alexliesenfeld/dgx-spark-printables/spark-atom/shop-img/ChatGPT Image Aug 3, 2026 at 11_18_05 PM.png

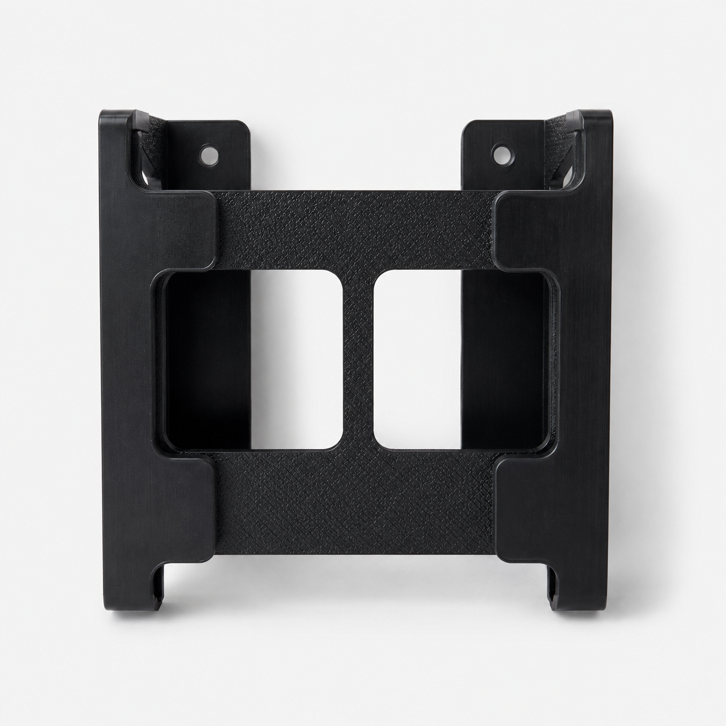
spark-atom/shop-img/ChatGPT Image Aug 3, 2026 at 11_18_05 PM.png
