alexliesenfeld/dgx-spark-printables/spark-atom/shop-img/ChatGPT Image Aug 3, 2026 at 11_45_13 PM.png

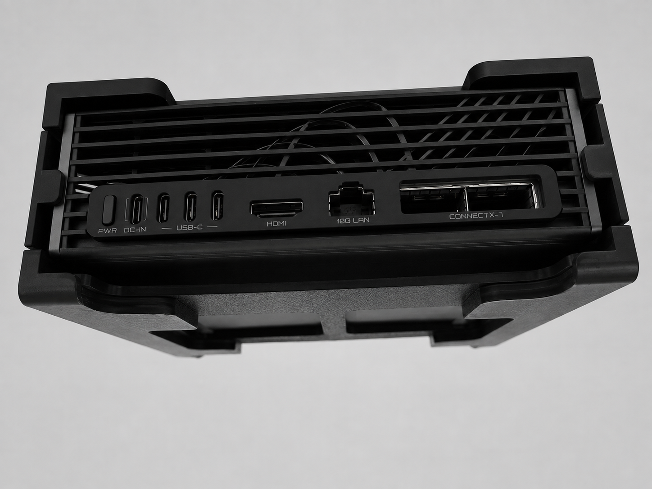
spark-atom/shop-img/ChatGPT Image Aug 3, 2026 at 11_45_13 PM.png
