alexliesenfeld/dgx-spark-printables/spark-atom/shop-img/IMG_5974.JPG

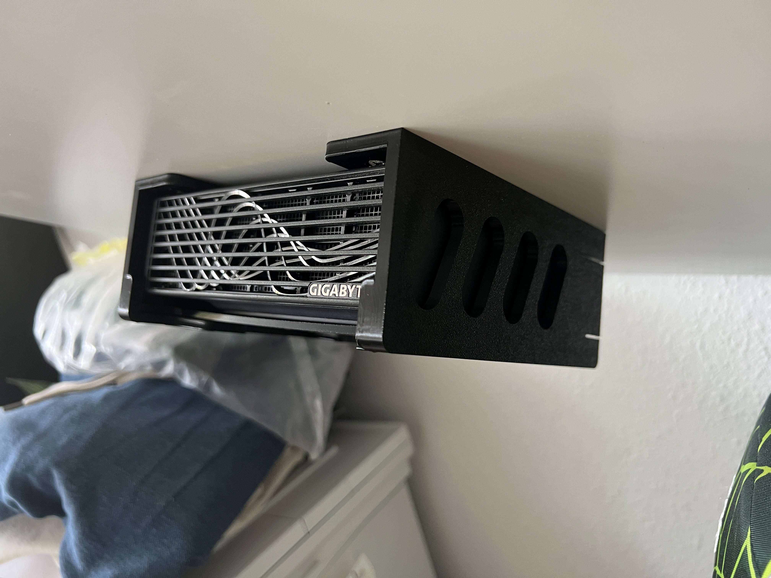
spark-atom/shop-img/IMG_5974.JPG
