alexliesenfeld/dgx-spark-printables/spark-atom/shop-img/IMG_5975.JPG

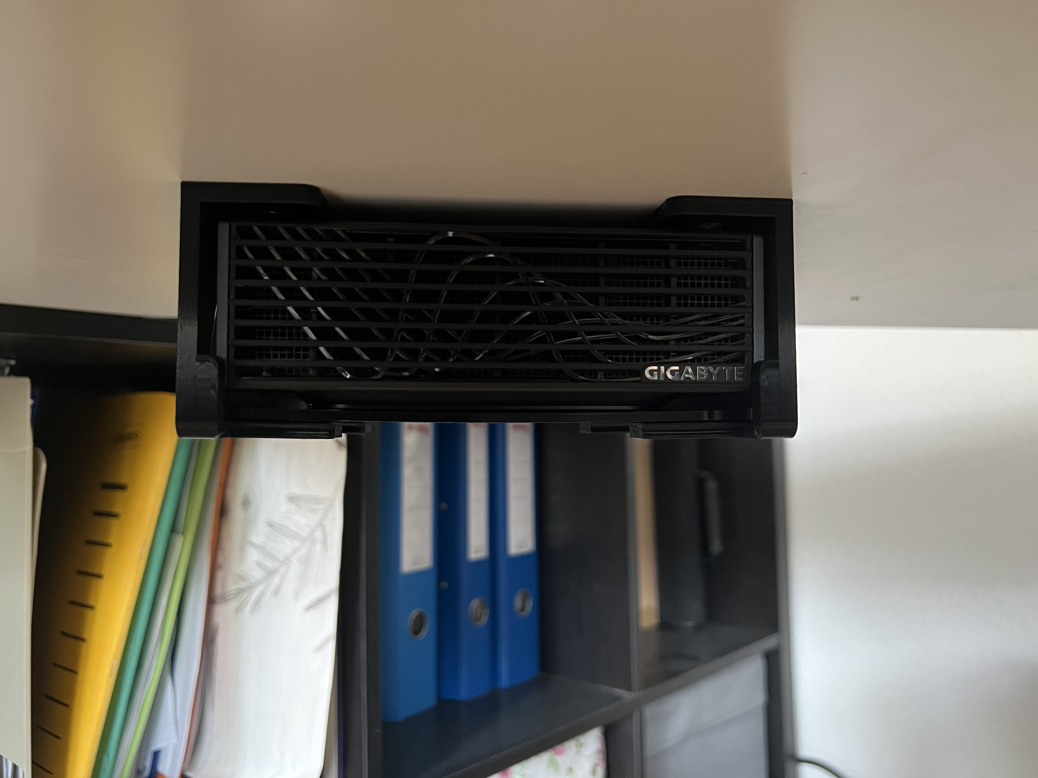
spark-atom/shop-img/IMG_5975.JPG
