alexliesenfeld/dgx-spark-printables/spark-atom/shop-img/IMG_5976.JPG

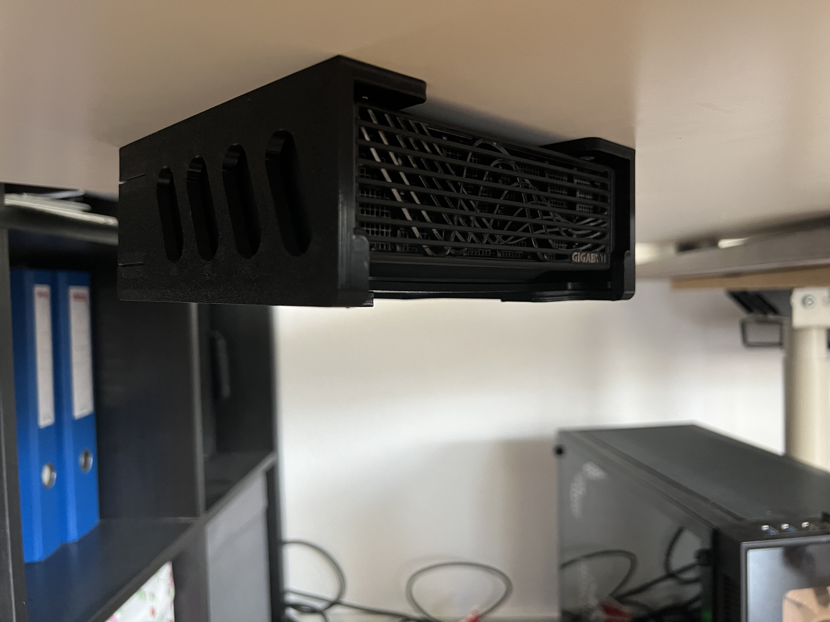
spark-atom/shop-img/IMG_5976.JPG
