alexliesenfeld/dgx-spark-printables/spark-atom/shop-img/IMG_5977.JPG

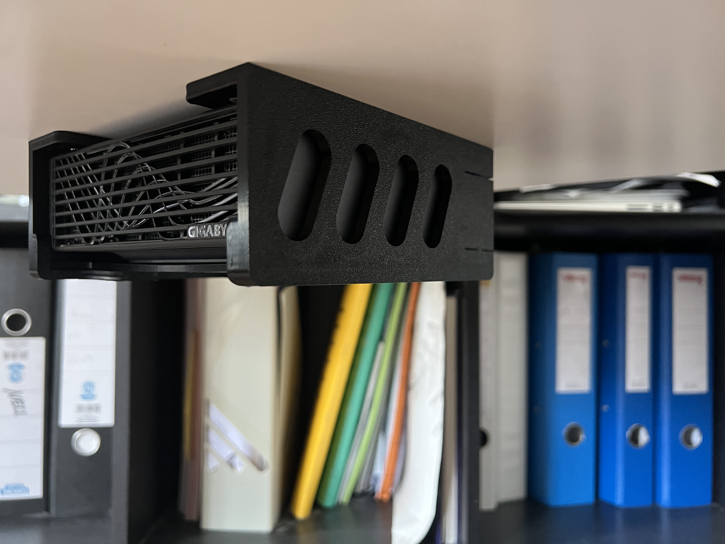
spark-atom/shop-img/IMG_5977.JPG
