alexliesenfeld/dgx-spark-printables/spark-atom/shop-img/openart-download/openart-sample_1785825434368_0cd59f5f.png

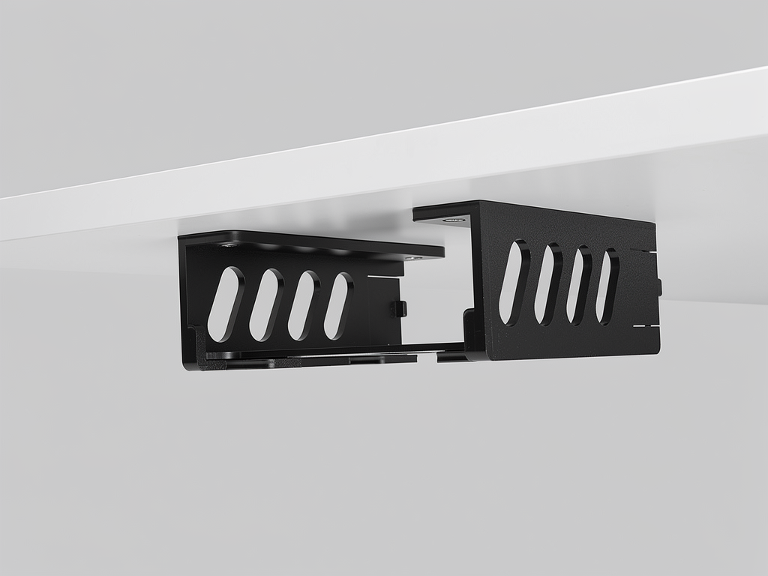
spark-atom/shop-img/openart-download/openart-sample_1785825434368_0cd59f5f.png
