alexliesenfeld/dgx-spark-printables/spark-atom/shop-img/openart-download/openart-sample_1785825800298_190668a8.png

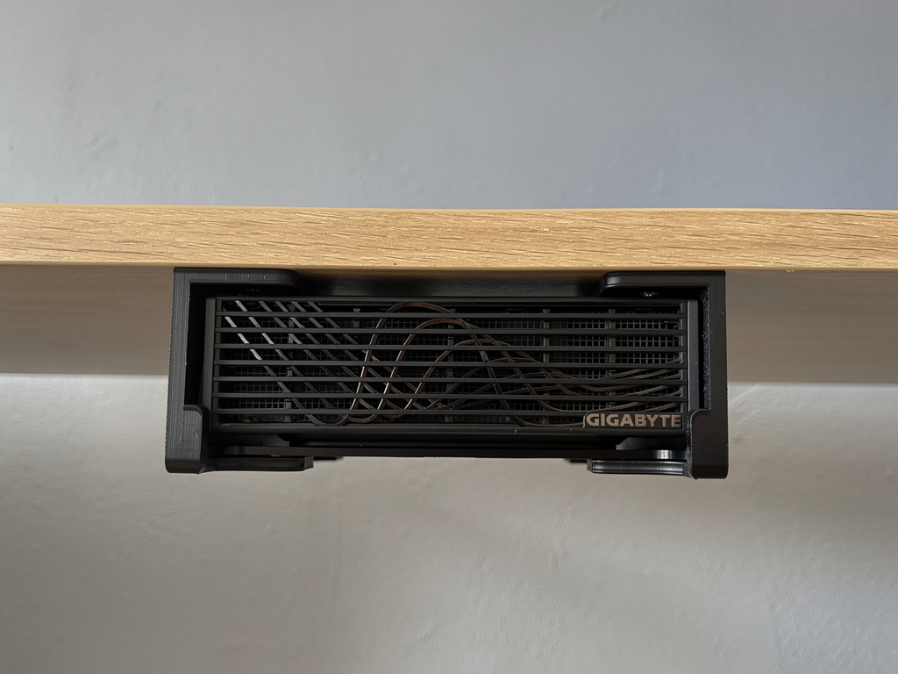
spark-atom/shop-img/openart-download/openart-sample_1785825800298_190668a8.png
