alexliesenfeld/dgx-spark-printables/spark-atom/shop-img/openart-sample_1785825800171_0b8fc502.png

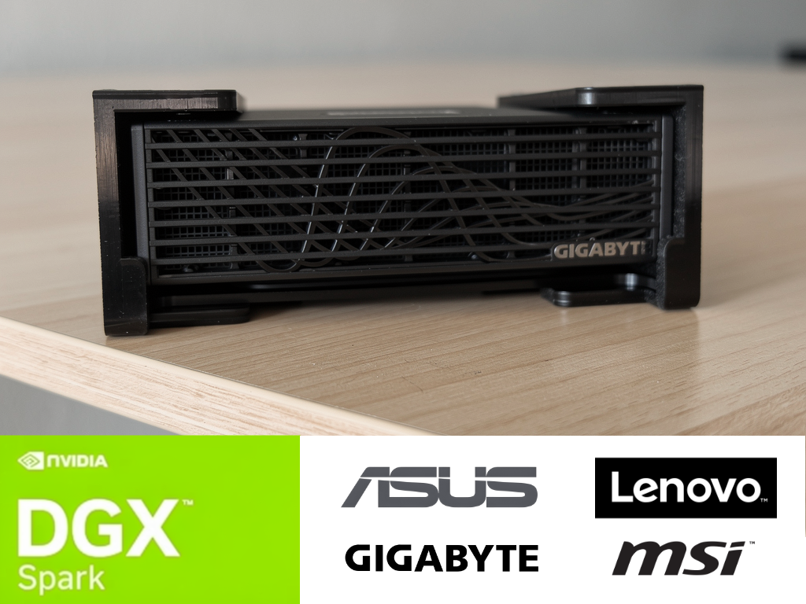
spark-atom/shop-img/openart-sample_1785825800171_0b8fc502.png
