alexliesenfeld/dgx-spark-printables/spark-atom/shop-img/untitled folder/IMG_5968.JPG

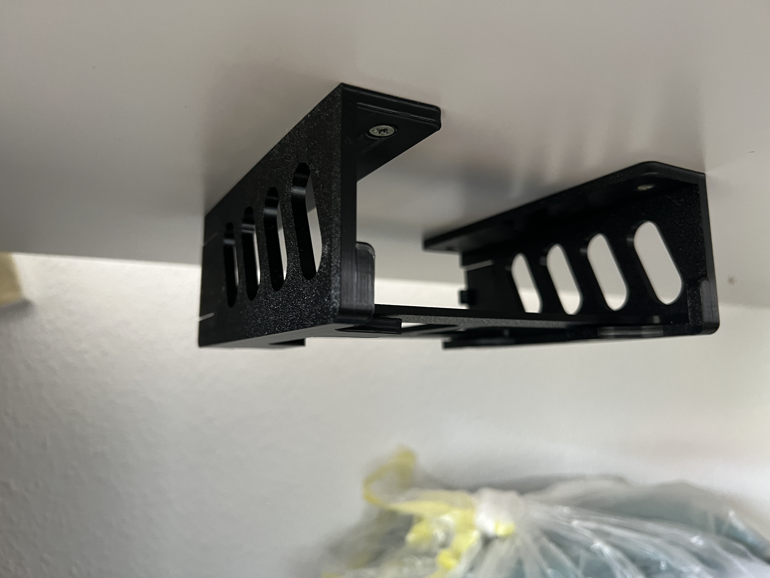
spark-atom/shop-img/untitled folder/IMG_5968.JPG
