alexliesenfeld/dgx-spark-printables/spark-atom/shop-img/untitled folder/IMG_5969.JPG

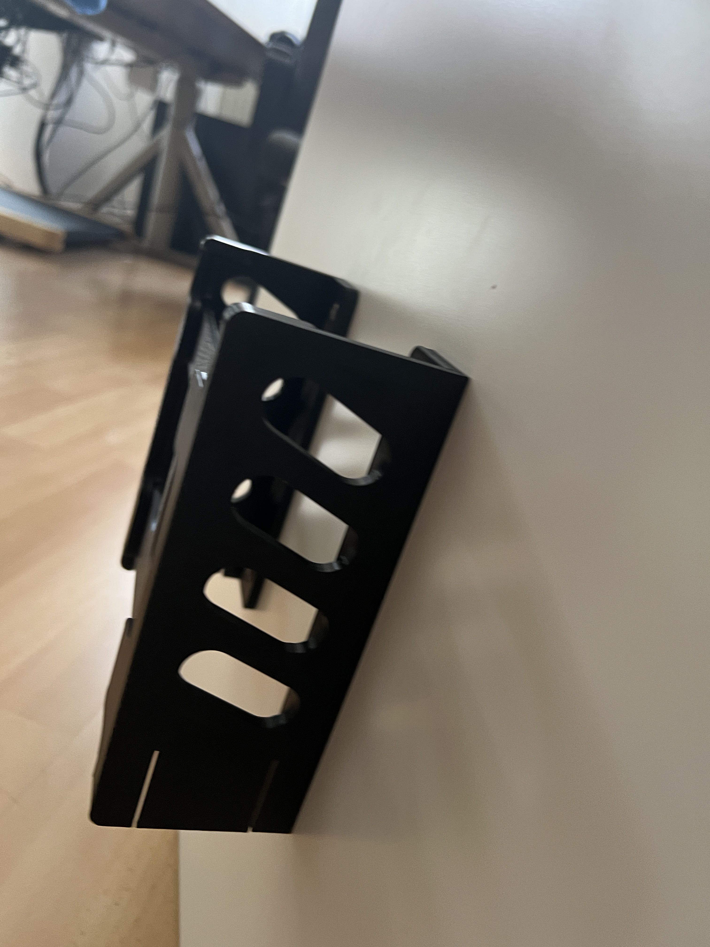
spark-atom/shop-img/untitled folder/IMG_5969.JPG
