alexliesenfeld/dgx-spark-printables/spark-atom/shop-img/untitled folder/IMG_5972.JPG

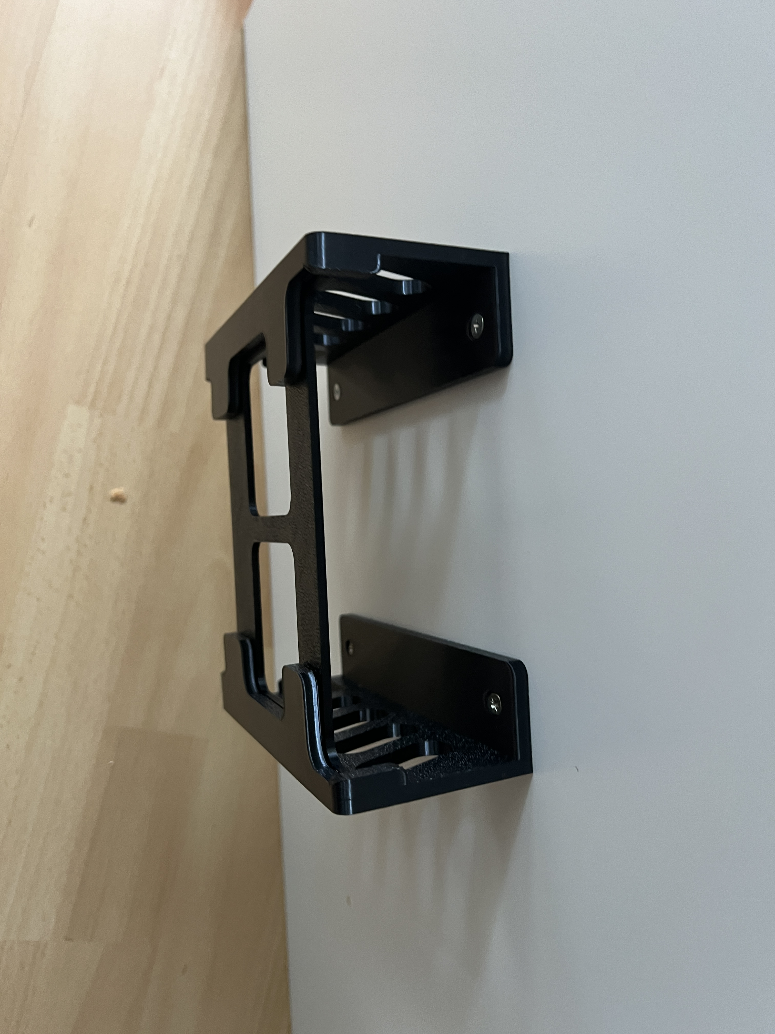
spark-atom/shop-img/untitled folder/IMG_5972.JPG
