alexliesenfeld/dgx-spark-printables/spark-rack-10/dgx_spark_rack_mount_demo.scad

/*
 * Demo view: rack mount with the 150 x 150 x 50.5 mm DGX Spark mockup and
 * two rear-mounted 80 x 80 x 25 mm fan mockups installed.
 *
 * This file is for visualization only. Export the printable assembly or its
 * individual parts from dgx_spark_rack_mount.scad instead.
 */

part_override = "demo";
include <dgx_spark_rack_mount.scad>
