alexliesenfeld/dgx-spark-printables/spark-atom/images/acer-bottom-projection.scad

/*
 * Demo-only pixel projection generated from acer.jpg.
 * Rows are stored top-to-bottom; the module flips them so the photograph's
 * bottom edge maps to Y=0, the physical front of the device.
 * Adjacent equal-shade pixels are merged into rectangles for faster previews.
 */

acer_projection_size = 160;
acer_projection_rectangles = [
    [0, 0, 1, 2, 51],
    [0, 1, 154, 1, 34],
    [0, 155, 1, 1, 51],
    [0, 156, 4, 2, 34],
    [1, 1, 2, 1, 34],
    [1, 3, 11, 1, 51],
    [1, 14, 36, 1, 34],
    [1, 50, 15, 1, 17],
    [1, 65, 3, 1, 34],
    [1, 68, 2, 1, 17],
    [1, 70, 2, 1, 34],
    [1, 72, 1, 1, 17],
    [1, 73, 1, 1, 34],
    [1, 74, 5, 1, 17],
    [1, 79, 2, 1, 34],
    [1, 81, 75, 1, 17],
    [2, 0, 3, 2, 34],
    [2, 3, 17, 1, 51],
    [2, 20, 80, 1, 34],
    [2, 100, 3, 1, 17],
    [2, 103, 1, 1, 34],
    [2, 104, 15, 1, 17],
    [2, 119, 2, 1, 34],
    [2, 121, 1, 1, 17],
    [2, 122, 1, 1, 34],
    [2, 123, 1, 1, 17],
    [2, 124, 5, 1, 34],
    [2, 129, 3, 1, 17],
    [2, 132, 2, 1, 34],
    [2, 134, 4, 1, 17],
    [2, 138, 22, 1, 34],
    [3, 3, 19, 1, 51],
    [3, 22, 1, 1, 34],
    [3, 23, 13, 1, 51],
    [3, 36, 1, 1, 34],
    [3, 37, 3, 1, 51],
    [3, 40, 62, 1, 34],
    [3, 102, 1, 1, 17],
    [3, 103, 3, 1, 34],
    [3, 106, 1, 1, 17],
    [3, 107, 2, 1, 34],
    [3, 109, 5, 1, 17],
    [3, 114, 1, 1, 34],
    [3, 115, 2, 1, 17],
    [3, 117, 43, 1, 34],
    [4, 0, 4, 1, 34],
    [4, 4, 13, 1, 51],
    [4, 17, 1, 1, 34],
    [4, 18, 1, 1, 51],
    [4, 19, 2, 1, 34],
    [4, 21, 1, 1, 51],
    [4, 22, 138, 1, 34],
    [5, 0, 160, 3, 34],
    [8, 0, 3, 2, 34],
    [8, 3, 2, 1, 51],
    [8, 5, 10, 1, 34],
    [8, 15, 1, 1, 17],
    [8, 16, 9, 1, 34],
    [8, 25, 1, 1, 17],
    [8, 26, 1, 1, 34],
    [8, 27, 118, 1, 17],
    [8, 145, 15, 1, 34],
    [9, 3, 1, 1, 51],
    [9, 4, 24, 1, 34],
    [9, 28, 1, 1, 17],
    [9, 29, 6, 1, 34],
    [9, 35, 121, 1, 17],
    [9, 156, 4, 88, 34],
    [10, 0, 2, 2, 34],
    [10, 2, 1, 2, 51],
    [10, 3, 26, 1, 34],
    [10, 29, 1, 1, 17],
    [10, 30, 3, 1, 34],
    [10, 33, 4, 1, 17],
    [10, 37, 2, 1, 34],
    [10, 39, 2, 1, 17],
    [10, 41, 1, 1, 34],
    [10, 42, 1, 1, 17],
    [10, 43, 1, 1, 34],
    [10, 44, 106, 1, 17],
    [10, 150, 1, 1, 34],
    [10, 151, 1, 1, 17],
    [10, 152, 1, 1, 34],
    [10, 153, 1, 1, 17],
    [10, 154, 1, 1, 34],
    [10, 155, 1, 1, 17],
    [11, 3, 28, 1, 34],
    [11, 31, 1, 1, 17],
    [11, 32, 7, 1, 34],
    [11, 39, 1, 1, 17],
    [11, 40, 3, 1, 34],
    [11, 43, 1, 1, 17],
    [11, 44, 1, 1, 34],
    [11, 45, 2, 1, 17],
    [11, 47, 1, 1, 34],
    [11, 48, 7, 1, 17],
    [11, 55, 1, 1, 34],
    [11, 56, 96, 1, 17],
    [11, 152, 2, 1, 34],
    [11, 154, 2, 1, 17],
    [12, 0, 50, 2, 34],
    [12, 50, 1, 2, 17],
    [12, 51, 2, 1, 34],
    [12, 53, 98, 1, 17],
    [12, 151, 1, 1, 34],
    [12, 152, 1, 1, 17],
    [12, 153, 2, 2, 34],
    [12, 155, 1, 3, 17],
    [13, 51, 3, 1, 34],
    [13, 54, 1, 1, 17],
    [13, 55, 4, 1, 34],
    [13, 59, 2, 1, 17],
    [13, 61, 2, 1, 34],
    [13, 63, 4, 1, 17],
    [13, 67, 1, 1, 34],
    [13, 68, 82, 1, 17],
    [13, 150, 1, 1, 34],
    [13, 151, 2, 1, 17],
    [14, 0, 2, 10, 34],
    [14, 2, 1, 7, 51],
    [14, 3, 64, 1, 34],
    [14, 67, 3, 1, 17],
    [14, 70, 2, 1, 34],
    [14, 72, 1, 1, 17],
    [14, 73, 1, 1, 34],
    [14, 74, 78, 1, 17],
    [14, 152, 1, 1, 34],
    [14, 153, 1, 1, 17],
    [14, 154, 1, 1, 34],
    [15, 3, 73, 1, 34],
    [15, 76, 1, 1, 17],
    [15, 77, 1, 1, 34],
    [15, 78, 1, 1, 17],
    [15, 79, 4, 1, 34],
    [15, 83, 1, 1, 17],
    [15, 84, 2, 1, 34],
    [15, 86, 18, 1, 17],
    [15, 104, 1, 1, 34],
    [15, 105, 51, 1, 17],
    [16, 3, 87, 1, 34],
    [16, 90, 2, 1, 17],
    [16, 92, 5, 1, 34],
    [16, 97, 1, 1, 17],
    [16, 98, 11, 1, 34],
    [16, 109, 1, 1, 17],
    [16, 110, 3, 1, 34],
    [16, 113, 1, 1, 17],
    [16, 114, 1, 1, 34],
    [16, 115, 12, 1, 17],
    [16, 127, 5, 1, 34],
    [16, 132, 1, 1, 17],
    [16, 133, 1, 1, 34],
    [16, 134, 1, 1, 17],
    [16, 135, 2, 1, 34],
    [16, 137, 19, 1, 17],
    [17, 3, 111, 1, 34],
    [17, 114, 1, 1, 17],
    [17, 115, 25, 1, 34],
    [17, 140, 13, 1, 17],
    [17, 153, 1, 1, 34],
    [17, 154, 2, 1, 17],
    [18, 3, 20, 1, 34],
    [18, 23, 9, 1, 51],
    [18, 32, 109, 1, 34],
    [18, 141, 1, 1, 17],
    [18, 142, 2, 1, 34],
    [18, 144, 12, 2, 17],
    [19, 3, 18, 1, 34],
    [19, 21, 11, 1, 51],
    [19, 32, 98, 1, 34],
    [19, 130, 5, 1, 51],
    [19, 135, 1, 1, 34],
    [19, 136, 1, 1, 51],
    [19, 137, 7, 1, 34],
    [20, 3, 16, 1, 34],
    [20, 19, 3, 1, 51],
    [20, 22, 6, 1, 68],
    [20, 28, 3, 1, 51],
    [20, 31, 65, 1, 34],
    [20, 96, 1, 1, 17],
    [20, 97, 3, 1, 34],
    [20, 100, 1, 2, 17],
    [20, 101, 12, 1, 34],
    [20, 113, 2, 1, 17],
    [20, 115, 1, 1, 34],
    [20, 116, 5, 1, 17],
    [20, 121, 9, 1, 34],
    [20, 130, 2, 1, 51],
    [20, 132, 3, 2, 68],
    [20, 135, 4, 1, 51],
    [20, 139, 6, 1, 34],
    [20, 145, 1, 1, 17],
    [20, 146, 1, 1, 34],
    [20, 147, 9, 1, 17],
    [21, 2, 2, 3, 51],
    [21, 4, 14, 1, 34],
    [21, 18, 2, 1, 51],
    [21, 20, 2, 1, 68],
    [21, 22, 2, 1, 85],
    [21, 24, 3, 1, 68],
    [21, 27, 2, 1, 51],
    [21, 29, 64, 1, 34],
    [21, 93, 1, 1, 17],
    [21, 94, 6, 1, 34],
    [21, 101, 9, 1, 34],
    [21, 110, 1, 1, 17],
    [21, 111, 5, 1, 34],
    [21, 116, 1, 1, 17],
    [21, 117, 2, 1, 34],
    [21, 119, 4, 1, 17],
    [21, 123, 8, 1, 34],
    [21, 131, 1, 1, 51],
    [21, 135, 1, 1, 85],
    [21, 136, 3, 1, 68],
    [21, 139, 1, 1, 51],
    [21, 140, 6, 1, 34],
    [21, 146, 3, 1, 17],
    [21, 149, 1, 2, 34],
    [21, 150, 6, 2, 17],
    [22, 4, 12, 1, 34],
    [22, 16, 3, 1, 51],
    [22, 19, 1, 1, 68],
    [22, 20, 4, 1, 85],
    [22, 24, 2, 1, 68],
    [22, 26, 2, 1, 51],
    [22, 28, 103, 1, 34],
    [22, 131, 2, 1, 51],
    [22, 133, 1, 1, 68],
    [22, 134, 5, 1, 85],
    [22, 139, 1, 1, 68],
    [22, 140, 2, 1, 51],
    [22, 142, 6, 1, 34],
    [22, 148, 1, 1, 17],
    [23, 4, 11, 1, 34],
    [23, 15, 2, 1, 51],
    [23, 17, 2, 1, 68],
    [23, 19, 4, 1, 85],
    [23, 23, 1, 1, 68],
    [23, 24, 2, 1, 51],
    [23, 26, 106, 1, 34],
    [23, 132, 1, 1, 51],
    [23, 133, 2, 1, 68],
    [23, 135, 1, 2, 85],
    [23, 136, 3, 1, 102],
    [23, 139, 2, 1, 85],
    [23, 141, 1, 1, 68],
    [23, 142, 1, 1, 51],
    [23, 143, 8, 1, 34],
    [23, 151, 5, 1, 17],
    [24, 0, 15, 1, 34],
    [24, 15, 1, 1, 51],
    [24, 16, 1, 1, 68],
    [24, 17, 2, 1, 85],
    [24, 19, 2, 1, 102],
    [24, 21, 1, 1, 85],
    [24, 22, 1, 2, 68],
    [24, 23, 2, 1, 51],
    [24, 25, 7, 1, 34],
    [24, 32, 97, 1, 17],
    [24, 129, 2, 1, 34],
    [24, 131, 3, 1, 51],
    [24, 134, 1, 1, 68],
    [24, 136, 5, 1, 102],
    [24, 141, 1, 1, 85],
    [24, 142, 1, 1, 68],
    [24, 143, 1, 1, 51],
    [24, 144, 5, 1, 34],
    [24, 149, 7, 1, 17],
    [25, 0, 14, 1, 34],
    [25, 14, 1, 1, 51],
    [25, 15, 1, 1, 68],
    [25, 16, 2, 1, 85],
    [25, 18, 2, 1, 102],
    [25, 20, 2, 1, 85],
    [25, 23, 1, 1, 51],
    [25, 24, 1, 1, 34],
    [25, 25, 2, 1, 51],
    [25, 27, 2, 1, 34],
    [25, 29, 1, 1, 17],
    [25, 30, 77, 1, 34],
    [25, 107, 1, 1, 17],
    [25, 108, 5, 1, 34],
    [25, 113, 1, 1, 17],
    [25, 114, 15, 1, 34],
    [25, 129, 2, 1, 17],
    [25, 131, 2, 1, 34],
    [25, 133, 1, 1, 68],
    [25, 134, 3, 1, 85],
    [25, 137, 2, 2, 102],
    [25, 139, 1, 1, 119],
    [25, 140, 2, 1, 102],
    [25, 142, 1, 1, 85],
    [25, 143, 1, 1, 68],
    [25, 144, 1, 2, 51],
    [25, 145, 5, 1, 34],
    [25, 150, 6, 1, 17],
    [26, 0, 2, 1, 34],
    [26, 2, 1, 1, 51],
    [26, 3, 10, 1, 34],
    [26, 13, 1, 2, 51],
    [26, 14, 2, 1, 68],
    [26, 16, 1, 1, 85],
    [26, 17, 3, 1, 102],
    [26, 20, 1, 1, 85],
    [26, 21, 1, 1, 68],
    [26, 22, 4, 1, 51],
    [26, 26, 4, 1, 34],
    [26, 30, 13, 1, 51],
    [26, 43, 2, 1, 34],
    [26, 45, 1, 1, 51],
    [26, 46, 1, 1, 34],
    [26, 47, 1, 1, 51],
    [26, 48, 85, 1, 34],
    [26, 133, 1, 1, 17],
    [26, 134, 1, 1, 51],
    [26, 135, 2, 1, 85],
    [26, 139, 3, 1, 119],
    [26, 142, 1, 1, 102],
    [26, 143, 1, 1, 85],
    [26, 145, 6, 1, 34],
    [26, 151, 5, 4, 17],
    [27, 0, 13, 1, 34],
    [27, 14, 1, 1, 68],
    [27, 15, 1, 1, 85],
    [27, 16, 3, 1, 102],
    [27, 19, 1, 1, 85],
    [27, 20, 1, 1, 68],
    [27, 21, 2, 1, 51],
    [27, 23, 1, 1, 68],
    [27, 24, 1, 1, 34],
    [27, 25, 1, 1, 17],
    [27, 26, 1, 1, 34],
    [27, 27, 9, 1, 51],
    [27, 36, 1, 1, 34],
    [27, 37, 4, 1, 51],
    [27, 41, 1, 1, 34],
    [27, 42, 1, 1, 51],
    [27, 43, 91, 1, 34],
    [27, 134, 1, 1, 17],
    [27, 135, 1, 1, 34],
    [27, 136, 3, 1, 102],
    [27, 139, 4, 1, 119],
    [27, 143, 1, 1, 102],
    [27, 144, 1, 1, 68],
    [27, 145, 1, 1, 51],
    [27, 146, 5, 1, 34],
    [28, 0, 2, 2, 34],
    [28, 2, 1, 2, 51],
    [28, 3, 9, 1, 34],
    [28, 12, 1, 1, 51],
    [28, 13, 1, 2, 68],
    [28, 14, 1, 2, 85],
    [28, 15, 3, 1, 102],
    [28, 18, 1, 2, 85],
    [28, 19, 1, 2, 68],
    [28, 20, 2, 1, 51],
    [28, 22, 1, 1, 68],
    [28, 23, 2, 1, 34],
    [28, 25, 18, 1, 51],
    [28, 43, 1, 1, 34],
    [28, 44, 1, 1, 51],
    [28, 45, 1, 1, 34],
    [28, 46, 1, 1, 51],
    [28, 47, 87, 1, 34],
    [28, 134, 1, 1, 51],
    [28, 135, 2, 1, 34],
    [28, 137, 2, 1, 102],
    [28, 139, 5, 1, 119],
    [28, 144, 1, 1, 85],
    [28, 145, 1, 1, 68],
    [28, 146, 1, 2, 51],
    [28, 147, 4, 2, 34],
    [29, 3, 8, 1, 34],
    [29, 11, 2, 1, 51],
    [29, 15, 1, 1, 102],
    [29, 16, 1, 1, 119],
    [29, 17, 1, 1, 102],
    [29, 20, 1, 1, 51],
    [29, 21, 1, 1, 68],
    [29, 22, 2, 1, 34],
    [29, 24, 24, 1, 51],
    [29, 48, 2, 1, 34],
    [29, 50, 3, 1, 51],
    [29, 53, 82, 1, 34],
    [29, 135, 1, 1, 51],
    [29, 136, 2, 1, 34],
    [29, 138, 1, 1, 119],
    [29, 139, 1, 1, 102],
    [29, 140, 4, 1, 119],
    [29, 144, 1, 1, 102],
    [29, 145, 1, 1, 85],
    [30, 0, 11, 2, 34],
    [30, 11, 1, 2, 51],
    [30, 12, 1, 2, 68],
    [30, 13, 1, 2, 85],
    [30, 14, 3, 1, 102],
    [30, 17, 1, 2, 85],
    [30, 18, 1, 1, 68],
    [30, 19, 1, 1, 51],
    [30, 20, 1, 2, 68],
    [30, 21, 1, 1, 51],
    [30, 22, 1, 1, 34],
    [30, 23, 1, 1, 51],
    [30, 24, 1, 1, 34],
    [30, 25, 15, 1, 51],
    [30, 40, 1, 1, 34],
    [30, 41, 4, 1, 51],
    [30, 45, 5, 1, 34],
    [30, 50, 2, 1, 51],
    [30, 52, 84, 1, 34],
    [30, 136, 1, 1, 51],
    [30, 137, 1, 1, 17],
    [30, 138, 1, 1, 68],
    [30, 139, 6, 1, 119],
    [30, 145, 1, 3, 102],
    [30, 146, 1, 1, 68],
    [30, 147, 1, 2, 51],
    [30, 148, 4, 3, 34],
    [30, 152, 4, 13, 17],
    [31, 14, 1, 1, 102],
    [31, 15, 1, 1, 119],
    [31, 16, 1, 1, 102],
    [31, 18, 2, 1, 51],
    [31, 21, 1, 2, 34],
    [31, 22, 21, 1, 51],
    [31, 43, 1, 1, 34],
    [31, 44, 1, 1, 51],
    [31, 45, 2, 1, 34],
    [31, 47, 2, 1, 51],
    [31, 49, 88, 1, 34],
    [31, 137, 1, 2, 51],
    [31, 138, 1, 1, 17],
    [31, 139, 1, 1, 102],
    [31, 140, 2, 1, 119],
    [31, 142, 1, 1, 136],
    [31, 143, 2, 1, 119],
    [31, 146, 1, 2, 85],
    [32, 0, 2, 2, 34],
    [32, 2, 1, 2, 51],
    [32, 3, 7, 2, 34],
    [32, 10, 2, 1, 51],
    [32, 12, 1, 4, 85],
    [32, 13, 3, 1, 102],
    [32, 16, 1, 2, 85],
    [32, 17, 1, 1, 68],
    [32, 18, 1, 1, 51],
    [32, 19, 1, 2, 68],
    [32, 20, 1, 1, 51],
    [32, 22, 30, 1, 51],
    [32, 52, 1, 1, 34],
    [32, 53, 1, 1, 51],
    [32, 54, 83, 1, 34],
    [32, 138, 1, 1, 34],
    [32, 139, 1, 1, 51],
    [32, 140, 3, 1, 119],
    [32, 143, 1, 2, 136],
    [32, 144, 1, 1, 119],
    [32, 147, 1, 3, 68],
    [33, 10, 1, 4, 51],
    [33, 11, 1, 4, 68],
    [33, 13, 1, 2, 102],
    [33, 14, 1, 2, 119],
    [33, 15, 1, 2, 102],
    [33, 17, 2, 1, 51],
    [33, 20, 1, 2, 34],
    [33, 21, 10, 1, 51],
    [33, 31, 107, 1, 34],
    [33, 138, 1, 3, 51],
    [33, 139, 1, 3, 34],
    [33, 140, 1, 1, 102],
    [33, 141, 2, 1, 119],
    [33, 144, 2, 1, 119],
    [33, 146, 1, 49, 102],
    [33, 148, 1, 6, 51],
    [33, 149, 3, 10, 34],
    [34, 0, 10, 3, 34],
    [34, 16, 1, 3, 68],
    [34, 17, 3, 1, 51],
    [34, 21, 8, 1, 51],
    [34, 29, 1, 1, 34],
    [34, 30, 1, 1, 17],
    [34, 31, 98, 1, 34],
    [34, 129, 1, 1, 17],
    [34, 130, 3, 1, 34],
    [34, 133, 2, 1, 51],
    [34, 135, 3, 1, 34],
    [34, 140, 1, 1, 85],
    [34, 141, 5, 3, 119],
    [35, 13, 3, 1, 102],
    [35, 17, 2, 1, 51],
    [35, 19, 2, 1, 34],
    [35, 21, 7, 1, 51],
    [35, 28, 1, 1, 34],
    [35, 29, 1, 1, 17],
    [35, 30, 100, 1, 51],
    [35, 130, 1, 1, 17],
    [35, 131, 1, 1, 34],
    [35, 132, 1, 2, 51],
    [35, 133, 5, 1, 34],
    [35, 140, 1, 1, 51],
    [35, 147, 1, 66, 85],
    [36, 12, 3, 32, 102],
    [36, 15, 1, 4, 85],
    [36, 17, 1, 14, 34],
    [36, 18, 1, 1, 68],
    [36, 19, 1, 10, 34],
    [36, 20, 7, 4, 51],
    [36, 27, 1, 4, 34],
    [36, 28, 1, 4, 17],
    [36, 29, 3, 1, 51],
    [36, 32, 96, 1, 34],
    [36, 128, 2, 1, 51],
    [36, 130, 1, 1, 34],
    [36, 131, 1, 4, 17],
    [36, 133, 8, 1, 34],
    [37, 0, 9, 4, 34],
    [37, 9, 2, 4, 51],
    [37, 11, 1, 16, 85],
    [37, 16, 1, 13, 51],
    [37, 18, 1, 29, 51],
    [37, 29, 2, 2, 51],
    [37, 31, 98, 2, 34],
    [37, 129, 2, 2, 51],
    [37, 132, 7, 1, 34],
    [37, 139, 1, 34, 51],
    [37, 140, 1, 1, 34],
    [37, 141, 1, 1, 102],
    [37, 142, 4, 1, 119],
    [38, 132, 2, 1, 34],
    [38, 134, 1, 1, 51],
    [38, 135, 4, 3, 34],
    [38, 140, 1, 85, 17],
    [38, 141, 2, 1, 102],
    [38, 143, 3, 22, 119],
    [39, 29, 100, 1, 34],
    [39, 129, 1, 1, 51],
    [39, 130, 1, 1, 34],
    [39, 132, 1, 1, 34],
    [39, 133, 2, 1, 51],
    [39, 141, 1, 18, 85],
    [39, 142, 1, 21, 102],
    [39, 148, 1, 6, 68],
    [40, 15, 1, 43, 68],
    [40, 20, 8, 2, 51],
    [40, 28, 1, 2, 34],
    [40, 29, 1, 1, 17],
    [40, 30, 100, 1, 34],
    [40, 130, 1, 1, 17],
    [40, 131, 3, 1, 34],
    [40, 134, 1, 1, 51],
    [41, 0, 10, 1, 34],
    [41, 10, 1, 1, 51],
    [41, 29, 2, 1, 17],
    [41, 31, 98, 1, 34],
    [41, 129, 2, 1, 17],
    [41, 131, 8, 1, 34],
    [42, 0, 4, 1, 34],
    [42, 4, 1, 1, 17],
    [42, 5, 4, 1, 34],
    [42, 9, 2, 1, 51],
    [42, 20, 10, 1, 51],
    [42, 30, 95, 1, 34],
    [42, 125, 4, 1, 17],
    [42, 129, 2, 1, 34],
    [42, 131, 1, 1, 51],
    [42, 132, 7, 1, 34],
    [43, 0, 10, 1, 34],
    [43, 10, 1, 1, 51],
    [43, 20, 42, 1, 51],
    [43, 62, 6, 1, 34],
    [43, 68, 2, 1, 51],
    [43, 70, 10, 1, 34],
    [43, 80, 1, 1, 51],
    [43, 81, 58, 1, 34],
    [43, 149, 2, 1, 34],
    [43, 151, 5, 1, 17],
    [44, 0, 9, 1, 34],
    [44, 9, 2, 1, 51],
    [44, 20, 31, 1, 51],
    [44, 51, 1, 1, 34],
    [44, 52, 11, 1, 51],
    [44, 63, 1, 1, 34],
    [44, 64, 2, 1, 51],
    [44, 66, 4, 1, 34],
    [44, 70, 1, 1, 51],
    [44, 71, 2, 1, 34],
    [44, 73, 1, 1, 51],
    [44, 74, 5, 1, 34],
    [44, 79, 1, 1, 51],
    [44, 80, 4, 1, 34],
    [44, 84, 1, 1, 51],
    [44, 85, 54, 1, 34],
    [44, 149, 3, 2, 34],
    [44, 152, 4, 2, 17],
    [45, 0, 4, 62, 34],
    [45, 4, 1, 20, 17],
    [45, 5, 5, 2, 34],
    [45, 10, 1, 2, 51],
    [45, 20, 8, 23, 51],
    [45, 28, 111, 1, 34],
    [45, 148, 1, 1, 51],
    [46, 19, 1, 1, 17],
    [46, 28, 100, 1, 17],
    [46, 128, 11, 1, 34],
    [46, 148, 1, 4, 68],
    [46, 149, 2, 15, 34],
    [46, 151, 5, 15, 17],
    [47, 5, 4, 1, 34],
    [47, 9, 2, 1, 51],
    [47, 19, 1, 1, 34],
    [47, 28, 101, 1, 17],
    [47, 129, 10, 1, 34],
    [48, 5, 5, 17, 34],
    [48, 10, 1, 77, 51],
    [48, 19, 1, 1, 17],
    [48, 28, 102, 1, 17],
    [48, 130, 9, 1, 34],
    [49, 19, 1, 1, 34],
    [49, 28, 103, 1, 17],
    [49, 131, 8, 1, 34],
    [50, 16, 2, 1, 34],
    [50, 19, 1, 8, 17],
    [50, 28, 104, 17, 17],
    [50, 132, 7, 17, 34],
    [50, 148, 1, 71, 51],
    [51, 16, 1, 1, 51],
    [51, 17, 1, 1, 34],
    [52, 16, 2, 14, 34],
    [53, 11, 1, 17, 68],
    [57, 141, 1, 66, 68],
    [58, 19, 1, 1, 34],
    [59, 19, 1, 8, 17],
    [60, 142, 2, 4, 102],
    [60, 144, 2, 4, 119],
    [61, 149, 1, 3, 34],
    [61, 150, 6, 3, 17],
    [64, 142, 1, 1, 102],
    [64, 143, 3, 1, 119],
    [64, 149, 2, 1, 34],
    [64, 151, 5, 1, 17],
    [65, 4, 2, 1, 17],
    [65, 6, 4, 1, 34],
    [65, 142, 2, 2, 102],
    [65, 144, 2, 2, 119],
    [65, 149, 1, 1, 34],
    [65, 150, 6, 1, 17],
    [66, 4, 1, 1, 17],
    [66, 5, 5, 1, 34],
    [66, 16, 3, 1, 34],
    [66, 149, 2, 2, 34],
    [66, 151, 5, 2, 17],
    [67, 4, 2, 1, 17],
    [67, 6, 4, 1, 34],
    [67, 16, 4, 2, 34],
    [67, 28, 24, 1, 34],
    [67, 52, 1, 1, 17],
    [67, 53, 1, 1, 34],
    [67, 54, 1, 1, 17],
    [67, 55, 2, 1, 34],
    [67, 57, 2, 1, 17],
    [67, 59, 1, 1, 34],
    [67, 60, 1, 1, 17],
    [67, 61, 4, 1, 34],
    [67, 65, 2, 1, 17],
    [67, 67, 2, 1, 34],
    [67, 69, 62, 1, 17],
    [67, 131, 8, 1, 34],
    [67, 142, 1, 2, 102],
    [67, 143, 3, 2, 119],
    [68, 4, 3, 2, 17],
    [68, 7, 3, 2, 34],
    [68, 12, 2, 1, 102],
    [68, 14, 1, 1, 85],
    [68, 20, 46, 1, 51],
    [68, 66, 1, 1, 34],
    [68, 67, 3, 1, 51],
    [68, 70, 2, 1, 34],
    [68, 72, 1, 1, 51],
    [68, 73, 13, 1, 34],
    [68, 86, 1, 1, 51],
    [68, 87, 52, 1, 34],
    [68, 149, 1, 3, 34],
    [68, 150, 6, 3, 17],
    [69, 12, 3, 2, 102],
    [69, 16, 3, 8, 34],
    [69, 19, 1, 56, 17],
    [69, 20, 34, 1, 51],
    [69, 54, 1, 1, 34],
    [69, 55, 4, 1, 51],
    [69, 59, 1, 1, 34],
    [69, 60, 9, 1, 51],
    [69, 69, 1, 1, 34],
    [69, 70, 1, 1, 51],
    [69, 71, 68, 1, 34],
    [69, 142, 2, 3, 102],
    [69, 144, 2, 7, 119],
    [70, 4, 2, 1, 17],
    [70, 6, 4, 1, 34],
    [70, 11, 1, 4, 85],
    [70, 20, 48, 1, 51],
    [70, 68, 2, 1, 34],
    [70, 70, 4, 1, 51],
    [70, 74, 65, 1, 34],
    [71, 4, 3, 1, 17],
    [71, 7, 3, 1, 34],
    [71, 12, 2, 3, 102],
    [71, 14, 1, 26, 85],
    [71, 20, 45, 1, 51],
    [71, 65, 1, 1, 34],
    [71, 66, 3, 1, 51],
    [71, 69, 5, 1, 34],
    [71, 74, 1, 1, 51],
    [71, 75, 65, 1, 34],
    [71, 149, 2, 1, 34],
    [71, 151, 5, 1, 17],
    [72, 4, 2, 1, 17],
    [72, 6, 4, 1, 34],
    [72, 20, 39, 1, 51],
    [72, 59, 1, 1, 34],
    [72, 60, 8, 1, 51],
    [72, 68, 71, 1, 34],
    [72, 139, 1, 2, 51],
    [72, 142, 1, 1, 85],
    [72, 143, 1, 1, 102],
    [72, 149, 1, 4, 34],
    [72, 150, 6, 4, 17],
    [73, 4, 3, 1, 17],
    [73, 7, 3, 4, 34],
    [73, 20, 48, 1, 51],
    [73, 68, 2, 1, 34],
    [73, 70, 1, 1, 51],
    [73, 71, 68, 1, 34],
    [73, 142, 2, 2, 102],
    [74, 4, 1, 2, 17],
    [74, 5, 1, 2, 34],
    [74, 6, 1, 2, 17],
    [74, 11, 2, 1, 85],
    [74, 13, 1, 1, 102],
    [74, 20, 45, 1, 51],
    [74, 65, 1, 1, 34],
    [74, 66, 1, 1, 51],
    [74, 67, 1, 1, 34],
    [74, 68, 3, 1, 51],
    [74, 71, 3, 1, 34],
    [74, 74, 1, 2, 51],
    [74, 75, 65, 2, 34],
    [75, 11, 1, 5, 85],
    [75, 12, 2, 5, 102],
    [75, 20, 53, 1, 51],
    [75, 73, 1, 1, 34],
    [75, 142, 1, 2, 85],
    [75, 143, 1, 1, 102],
    [76, 4, 3, 1, 17],
    [76, 20, 50, 1, 51],
    [76, 70, 2, 1, 34],
    [76, 72, 1, 1, 51],
    [76, 73, 2, 1, 34],
    [76, 75, 2, 1, 51],
    [76, 77, 6, 1, 34],
    [76, 83, 1, 1, 51],
    [76, 84, 55, 1, 34],
    [76, 139, 1, 2, 51],
    [76, 143, 3, 4, 119],
    [76, 149, 2, 1, 34],
    [76, 151, 5, 1, 17],
    [77, 4, 1, 1, 17],
    [77, 5, 5, 1, 34],
    [77, 16, 2, 1, 34],
    [77, 18, 1, 1, 51],
    [77, 20, 46, 1, 51],
    [77, 66, 1, 1, 34],
    [77, 67, 3, 1, 51],
    [77, 70, 1, 1, 34],
    [77, 71, 2, 1, 51],
    [77, 73, 1, 1, 34],
    [77, 74, 2, 1, 51],
    [77, 76, 16, 1, 34],
    [77, 92, 1, 1, 51],
    [77, 93, 46, 1, 34],
    [77, 142, 1, 3, 102],
    [77, 149, 1, 3, 34],
    [77, 150, 6, 3, 17],
    [78, 4, 2, 1, 17],
    [78, 6, 4, 1, 34],
    [78, 16, 3, 2, 34],
    [78, 20, 54, 1, 51],
    [78, 74, 1, 1, 34],
    [78, 75, 1, 1, 51],
    [78, 76, 4, 1, 34],
    [78, 80, 1, 1, 51],
    [78, 81, 59, 1, 34],
    [79, 4, 3, 3, 17],
    [79, 7, 3, 3, 34],
    [79, 20, 41, 1, 51],
    [79, 61, 1, 1, 34],
    [79, 62, 13, 1, 51],
    [79, 75, 3, 2, 34],
    [79, 78, 1, 1, 51],
    [79, 79, 5, 1, 34],
    [79, 84, 2, 1, 51],
    [79, 86, 8, 1, 34],
    [79, 94, 1, 1, 51],
    [79, 95, 44, 1, 34],
    [79, 139, 1, 7, 51],
    [80, 11, 2, 7, 85],
    [80, 13, 1, 17, 102],
    [80, 16, 2, 1, 34],
    [80, 18, 1, 1, 51],
    [80, 20, 53, 1, 51],
    [80, 73, 1, 1, 34],
    [80, 74, 1, 1, 51],
    [80, 78, 2, 1, 51],
    [80, 80, 3, 1, 34],
    [80, 83, 1, 1, 51],
    [80, 84, 1, 1, 34],
    [80, 85, 1, 1, 51],
    [80, 86, 53, 1, 34],
    [80, 142, 2, 1, 102],
    [80, 144, 2, 2, 119],
    [80, 149, 2, 1, 34],
    [80, 151, 5, 1, 17],
    [81, 16, 3, 20, 34],
    [81, 20, 46, 1, 51],
    [81, 66, 1, 1, 34],
    [81, 67, 2, 1, 51],
    [81, 69, 1, 1, 34],
    [81, 70, 3, 1, 51],
    [81, 73, 2, 1, 34],
    [81, 75, 1, 1, 51],
    [81, 76, 8, 1, 34],
    [81, 84, 1, 1, 51],
    [81, 85, 3, 1, 34],
    [81, 88, 1, 1, 51],
    [81, 89, 50, 1, 34],
    [81, 142, 1, 40, 85],
    [81, 143, 1, 9, 102],
    [81, 149, 1, 2, 34],
    [81, 150, 6, 2, 17],
    [82, 4, 2, 1, 17],
    [82, 6, 4, 1, 34],
    [82, 20, 43, 1, 51],
    [82, 63, 1, 1, 34],
    [82, 64, 1, 1, 51],
    [82, 65, 1, 1, 34],
    [82, 66, 2, 1, 51],
    [82, 68, 1, 1, 34],
    [82, 69, 4, 1, 51],
    [82, 73, 1, 1, 34],
    [82, 74, 1, 1, 51],
    [82, 75, 64, 1, 34],
    [82, 144, 1, 8, 119],
    [82, 145, 2, 8, 102],
    [83, 4, 3, 1, 17],
    [83, 7, 3, 1, 34],
    [83, 15, 1, 2, 51],
    [83, 20, 44, 1, 51],
    [83, 64, 1, 1, 34],
    [83, 65, 2, 1, 51],
    [83, 67, 2, 1, 34],
    [83, 69, 2, 1, 51],
    [83, 71, 2, 1, 34],
    [83, 73, 1, 1, 51],
    [83, 74, 13, 1, 34],
    [83, 87, 1, 1, 51],
    [83, 88, 51, 1, 34],
    [83, 149, 2, 4, 34],
    [83, 151, 5, 4, 17],
    [84, 4, 2, 1, 17],
    [84, 6, 4, 1, 34],
    [84, 20, 40, 1, 51],
    [84, 60, 1, 1, 34],
    [84, 61, 6, 1, 51],
    [84, 67, 4, 1, 34],
    [84, 71, 1, 3, 51],
    [84, 72, 67, 2, 34],
    [85, 4, 3, 4, 17],
    [85, 7, 3, 4, 34],
    [85, 15, 1, 1, 68],
    [85, 20, 37, 1, 51],
    [85, 57, 1, 1, 34],
    [85, 58, 3, 1, 51],
    [85, 61, 2, 1, 34],
    [85, 63, 1, 1, 51],
    [85, 64, 1, 2, 34],
    [85, 65, 5, 1, 51],
    [85, 70, 1, 1, 34],
    [86, 15, 1, 43, 51],
    [86, 20, 38, 2, 51],
    [86, 58, 1, 2, 34],
    [86, 59, 1, 1, 51],
    [86, 60, 1, 1, 34],
    [86, 61, 3, 1, 51],
    [86, 65, 1, 1, 51],
    [86, 66, 1, 1, 34],
    [86, 67, 2, 1, 51],
    [86, 69, 2, 1, 34],
    [86, 72, 68, 1, 34],
    [87, 11, 1, 1, 68],
    [87, 12, 1, 1, 85],
    [87, 59, 2, 1, 51],
    [87, 61, 5, 1, 34],
    [87, 66, 2, 1, 51],
    [87, 68, 16, 1, 34],
    [87, 84, 1, 1, 51],
    [87, 85, 54, 1, 34],
    [87, 139, 1, 1, 51],
    [87, 149, 1, 1, 34],
    [87, 150, 6, 1, 17],
    [88, 11, 2, 4, 85],
    [88, 20, 40, 1, 51],
    [88, 60, 4, 1, 34],
    [88, 64, 1, 1, 51],
    [88, 65, 1, 2, 34],
    [88, 66, 1, 2, 51],
    [88, 67, 73, 2, 34],
    [88, 149, 2, 3, 34],
    [88, 151, 5, 3, 17],
    [89, 4, 4, 1, 17],
    [89, 8, 2, 1, 34],
    [89, 20, 34, 1, 51],
    [89, 54, 1, 1, 34],
    [89, 55, 10, 1, 51],
    [90, 4, 3, 7, 17],
    [90, 7, 3, 9, 34],
    [90, 20, 37, 1, 51],
    [90, 57, 1, 1, 34],
    [90, 58, 4, 1, 51],
    [90, 62, 2, 1, 34],
    [90, 64, 2, 1, 51],
    [90, 66, 74, 1, 34],
    [90, 143, 4, 11, 102],
    [91, 20, 35, 1, 51],
    [91, 55, 84, 1, 34],
    [91, 139, 1, 4, 51],
    [91, 149, 1, 3, 34],
    [91, 150, 6, 3, 17],
    [92, 11, 1, 30, 68],
    [92, 12, 1, 5, 85],
    [92, 20, 38, 2, 51],
    [92, 58, 1, 3, 34],
    [92, 59, 1, 2, 51],
    [92, 60, 2, 1, 34],
    [92, 62, 2, 1, 51],
    [92, 64, 6, 1, 34],
    [92, 70, 1, 1, 51],
    [92, 71, 68, 1, 34],
    [93, 60, 79, 1, 34],
    [94, 20, 33, 1, 51],
    [94, 53, 1, 1, 34],
    [94, 54, 4, 1, 51],
    [94, 59, 2, 1, 51],
    [94, 61, 78, 1, 34],
    [94, 149, 2, 23, 34],
    [94, 151, 5, 3, 17],
    [95, 20, 32, 2, 51],
    [95, 52, 3, 1, 34],
    [95, 55, 1, 1, 51],
    [95, 56, 1, 1, 34],
    [95, 57, 1, 1, 51],
    [95, 58, 5, 1, 34],
    [95, 63, 1, 1, 51],
    [95, 64, 76, 1, 34],
    [96, 52, 13, 1, 34],
    [96, 65, 1, 1, 51],
    [96, 66, 74, 1, 34],
    [97, 4, 1, 10, 17],
    [97, 5, 1, 2, 34],
    [97, 6, 1, 2, 17],
    [97, 12, 3, 1, 85],
    [97, 20, 29, 3, 51],
    [97, 49, 2, 1, 34],
    [97, 51, 2, 1, 51],
    [97, 53, 87, 1, 34],
    [97, 151, 6, 1, 17],
    [97, 157, 3, 1, 34],
    [98, 12, 1, 3, 85],
    [98, 13, 1, 3, 102],
    [98, 14, 1, 3, 85],
    [98, 49, 91, 1, 34],
    [98, 151, 5, 11, 17],
    [98, 156, 4, 11, 34],
    [99, 5, 5, 8, 34],
    [99, 49, 2, 1, 34],
    [99, 51, 1, 1, 51],
    [99, 52, 88, 2, 34],
    [100, 20, 32, 1, 51],
    [101, 12, 3, 19, 85],
    [101, 16, 2, 1, 34],
    [101, 18, 1, 1, 51],
    [101, 20, 28, 1, 51],
    [101, 48, 92, 1, 34],
    [101, 143, 3, 1, 102],
    [101, 146, 2, 1, 85],
    [102, 16, 3, 13, 34],
    [102, 20, 29, 1, 51],
    [102, 49, 91, 1, 34],
    [102, 143, 4, 2, 102],
    [102, 147, 1, 1, 85],
    [103, 20, 30, 1, 51],
    [103, 50, 90, 1, 34],
    [103, 147, 1, 1, 68],
    [104, 20, 25, 1, 51],
    [104, 45, 95, 1, 34],
    [104, 143, 3, 17, 102],
    [104, 146, 2, 1, 85],
    [105, 20, 22, 1, 51],
    [105, 42, 1, 1, 34],
    [105, 43, 1, 1, 51],
    [105, 44, 2, 1, 34],
    [105, 46, 1, 1, 51],
    [105, 47, 93, 1, 34],
    [105, 146, 1, 17, 85],
    [105, 147, 1, 19, 68],
    [106, 20, 23, 1, 51],
    [106, 43, 2, 1, 34],
    [106, 45, 1, 1, 51],
    [106, 46, 2, 1, 34],
    [106, 48, 1, 1, 51],
    [106, 49, 91, 1, 34],
    [107, 0, 10, 3, 34],
    [107, 20, 18, 1, 51],
    [107, 38, 2, 1, 34],
    [107, 40, 3, 1, 51],
    [107, 43, 1, 1, 34],
    [107, 44, 2, 1, 51],
    [107, 46, 94, 2, 34],
    [108, 20, 12, 1, 51],
    [108, 32, 3, 1, 34],
    [108, 35, 3, 1, 51],
    [108, 38, 3, 1, 34],
    [108, 41, 1, 1, 51],
    [108, 42, 1, 1, 34],
    [108, 43, 1, 1, 51],
    [108, 44, 1, 1, 34],
    [108, 45, 1, 1, 51],
    [109, 20, 1, 3, 51],
    [109, 21, 1, 3, 34],
    [109, 22, 5, 1, 51],
    [109, 27, 1, 1, 34],
    [109, 28, 4, 1, 51],
    [109, 32, 1, 1, 34],
    [109, 33, 1, 1, 51],
    [109, 34, 1, 1, 34],
    [109, 35, 2, 1, 51],
    [109, 37, 2, 1, 34],
    [109, 39, 1, 2, 51],
    [109, 40, 100, 1, 34],
    [109, 151, 6, 2, 17],
    [109, 157, 3, 2, 34],
    [110, 0, 4, 2, 34],
    [110, 4, 1, 2, 17],
    [110, 5, 5, 2, 34],
    [110, 22, 4, 3, 51],
    [110, 26, 2, 2, 34],
    [110, 28, 5, 1, 51],
    [110, 33, 2, 1, 34],
    [110, 35, 1, 2, 51],
    [110, 36, 3, 1, 34],
    [110, 40, 1, 1, 34],
    [110, 41, 2, 1, 51],
    [110, 43, 97, 1, 34],
    [111, 28, 3, 1, 51],
    [111, 31, 1, 1, 34],
    [111, 32, 2, 1, 51],
    [111, 34, 1, 1, 34],
    [111, 36, 104, 1, 34],
    [111, 151, 5, 6, 17],
    [111, 156, 4, 6, 34],
    [112, 0, 10, 1, 34],
    [112, 20, 2, 1, 34],
    [112, 26, 5, 1, 34],
    [112, 31, 1, 1, 51],
    [112, 32, 1, 1, 34],
    [112, 33, 1, 1, 51],
    [112, 34, 6, 1, 34],
    [112, 40, 1, 1, 51],
    [112, 41, 99, 1, 34],
    [113, 0, 4, 1, 34],
    [113, 4, 1, 1, 17],
    [113, 5, 5, 1, 34],
    [113, 20, 3, 1, 34],
    [113, 23, 1, 1, 51],
    [113, 24, 116, 1, 34],
    [114, 0, 10, 1, 34],
    [114, 20, 120, 2, 34],
    [115, 0, 4, 1, 34],
    [115, 4, 2, 1, 17],
    [115, 6, 4, 1, 34],
    [115, 16, 2, 1, 34],
    [115, 18, 1, 1, 51],
    [116, 0, 10, 1, 34],
    [116, 16, 3, 6, 34],
    [116, 20, 11, 1, 34],
    [116, 31, 1, 1, 51],
    [116, 32, 4, 1, 34],
    [116, 36, 1, 1, 51],
    [116, 37, 1, 1, 34],
    [116, 38, 2, 1, 51],
    [116, 40, 1, 1, 34],
    [116, 41, 1, 1, 51],
    [116, 42, 98, 1, 34],
    [117, 0, 4, 5, 34],
    [117, 4, 1, 5, 17],
    [117, 5, 5, 5, 34],
    [117, 20, 86, 1, 34],
    [117, 106, 6, 1, 17],
    [117, 112, 2, 1, 34],
    [117, 114, 1, 1, 17],
    [117, 115, 11, 1, 34],
    [117, 126, 4, 1, 17],
    [117, 130, 10, 1, 34],
    [117, 149, 1, 1, 34],
    [117, 150, 7, 1, 17],
    [117, 157, 3, 10, 34],
    [118, 20, 9, 1, 34],
    [118, 29, 2, 1, 17],
    [118, 31, 98, 1, 34],
    [118, 129, 2, 1, 17],
    [118, 131, 9, 1, 34],
    [118, 149, 2, 2, 34],
    [118, 151, 6, 2, 17],
    [119, 20, 8, 2, 34],
    [119, 28, 2, 1, 17],
    [119, 30, 1, 1, 51],
    [119, 31, 15, 1, 34],
    [119, 46, 2, 1, 51],
    [119, 48, 6, 1, 34],
    [119, 54, 8, 1, 51],
    [119, 62, 2, 1, 34],
    [119, 64, 1, 1, 51],
    [119, 65, 26, 1, 34],
    [119, 91, 1, 1, 51],
    [119, 92, 4, 1, 34],
    [119, 96, 1, 1, 51],
    [119, 97, 6, 1, 34],
    [119, 103, 6, 1, 51],
    [119, 109, 19, 1, 34],
    [119, 128, 2, 1, 51],
    [119, 130, 2, 1, 17],
    [119, 132, 8, 2, 34],
    [120, 12, 2, 2, 85],
    [120, 14, 1, 4, 68],
    [120, 28, 1, 1, 17],
    [120, 29, 102, 1, 34],
    [120, 131, 1, 1, 17],
    [120, 149, 1, 1, 34],
    [120, 150, 7, 7, 17],
    [121, 20, 7, 3, 34],
    [121, 27, 2, 3, 17],
    [121, 29, 101, 1, 34],
    [121, 130, 1, 1, 51],
    [121, 131, 2, 2, 17],
    [121, 133, 7, 2, 34],
    [121, 142, 2, 2, 85],
    [121, 144, 2, 1, 102],
    [121, 148, 2, 6, 34],
    [122, 0, 10, 3, 34],
    [122, 11, 2, 2, 68],
    [122, 13, 1, 2, 85],
    [122, 16, 2, 1, 34],
    [122, 18, 1, 1, 51],
    [122, 29, 102, 2, 34],
    [122, 144, 1, 1, 102],
    [122, 145, 2, 1, 85],
    [123, 16, 3, 2, 34],
    [123, 131, 1, 1, 17],
    [123, 132, 9, 1, 34],
    [123, 141, 2, 2, 68],
    [123, 143, 4, 1, 85],
    [124, 11, 4, 1, 68],
    [124, 20, 8, 1, 34],
    [124, 28, 2, 1, 17],
    [124, 30, 100, 1, 34],
    [124, 130, 2, 1, 17],
    [124, 132, 7, 1, 34],
    [124, 139, 1, 3, 17],
    [124, 140, 1, 1, 34],
    [124, 143, 3, 2, 85],
    [124, 146, 1, 2, 68],
    [124, 147, 1, 3, 51],
    [125, 0, 11, 3, 34],
    [125, 11, 1, 3, 51],
    [125, 12, 3, 3, 68],
    [125, 16, 4, 2, 34],
    [125, 20, 1, 3, 17],
    [125, 21, 8, 1, 34],
    [125, 29, 14, 1, 17],
    [125, 43, 1, 1, 34],
    [125, 44, 11, 1, 17],
    [125, 55, 1, 1, 34],
    [125, 56, 75, 1, 17],
    [125, 131, 8, 1, 34],
    [125, 140, 2, 2, 51],
    [125, 142, 1, 1, 68],
    [126, 21, 47, 1, 34],
    [126, 68, 6, 1, 17],
    [126, 74, 1, 1, 34],
    [126, 75, 10, 1, 17],
    [126, 85, 1, 1, 34],
    [126, 86, 8, 1, 17],
    [126, 94, 5, 1, 34],
    [126, 99, 2, 1, 17],
    [126, 101, 4, 1, 34],
    [126, 105, 10, 1, 17],
    [126, 115, 1, 1, 34],
    [126, 116, 14, 1, 17],
    [126, 130, 9, 1, 34],
    [126, 142, 5, 1, 68],
    [127, 16, 2, 2, 34],
    [127, 18, 1, 1, 17],
    [127, 19, 1, 1, 34],
    [127, 21, 87, 1, 34],
    [127, 108, 1, 1, 17],
    [127, 109, 9, 1, 34],
    [127, 118, 1, 1, 17],
    [127, 119, 19, 1, 34],
    [127, 138, 1, 1, 17],
    [127, 139, 3, 3, 34],
    [127, 142, 1, 1, 51],
    [127, 143, 3, 1, 68],
    [127, 146, 1, 2, 51],
    [127, 147, 2, 2, 34],
    [127, 149, 7, 2, 17],
    [127, 156, 4, 4, 34],
    [128, 0, 12, 3, 34],
    [128, 12, 1, 2, 51],
    [128, 13, 2, 2, 68],
    [128, 18, 2, 2, 17],
    [128, 20, 1, 2, 34],
    [128, 21, 1, 1, 17],
    [128, 22, 52, 1, 34],
    [128, 74, 1, 1, 17],
    [128, 75, 4, 1, 34],
    [128, 79, 1, 1, 17],
    [128, 80, 11, 1, 34],
    [128, 91, 1, 1, 17],
    [128, 92, 13, 1, 34],
    [128, 105, 1, 1, 17],
    [128, 106, 1, 1, 34],
    [128, 107, 2, 1, 17],
    [128, 109, 28, 2, 34],
    [128, 137, 2, 2, 17],
    [128, 142, 2, 1, 51],
    [128, 144, 2, 1, 68],
    [129, 15, 2, 2, 51],
    [129, 17, 1, 3, 34],
    [129, 21, 2, 1, 17],
    [129, 23, 49, 1, 34],
    [129, 72, 1, 1, 17],
    [129, 73, 14, 1, 34],
    [129, 87, 1, 2, 17],
    [129, 88, 18, 1, 34],
    [129, 106, 1, 1, 17],
    [129, 107, 1, 1, 34],
    [129, 108, 1, 1, 17],
    [129, 142, 4, 1, 51],
    [129, 146, 2, 2, 34],
    [129, 148, 8, 2, 17],
    [130, 12, 2, 1, 51],
    [130, 14, 1, 1, 68],
    [130, 18, 3, 1, 17],
    [130, 21, 1, 1, 34],
    [130, 22, 2, 1, 17],
    [130, 24, 50, 1, 34],
    [130, 74, 1, 1, 17],
    [130, 75, 12, 1, 34],
    [130, 88, 2, 1, 34],
    [130, 90, 1, 1, 17],
    [130, 91, 14, 1, 34],
    [130, 105, 1, 1, 17],
    [130, 106, 7, 1, 34],
    [130, 113, 1, 1, 17],
    [130, 114, 22, 1, 34],
    [130, 136, 4, 1, 17],
    [130, 140, 3, 1, 34],
    [130, 143, 3, 1, 51],
    [131, 0, 13, 1, 34],
    [131, 13, 4, 1, 51],
    [131, 18, 4, 1, 17],
    [131, 22, 1, 1, 34],
    [131, 23, 2, 1, 17],
    [131, 25, 45, 1, 34],
    [131, 70, 1, 1, 17],
    [131, 71, 1, 1, 34],
    [131, 72, 5, 1, 17],
    [131, 77, 3, 1, 34],
    [131, 80, 1, 1, 17],
    [131, 81, 4, 1, 34],
    [131, 85, 2, 1, 17],
    [131, 87, 2, 1, 34],
    [131, 89, 1, 1, 17],
    [131, 90, 1, 1, 34],
    [131, 91, 1, 1, 17],
    [131, 92, 13, 1, 34],
    [131, 105, 2, 1, 17],
    [131, 107, 5, 1, 34],
    [131, 112, 1, 1, 17],
    [131, 113, 21, 1, 34],
    [131, 134, 7, 1, 17],
    [131, 141, 2, 1, 34],
    [131, 143, 2, 1, 51],
    [131, 145, 2, 1, 34],
    [131, 147, 10, 1, 17],
    [131, 157, 3, 2, 34],
    [132, 0, 9, 1, 34],
    [132, 9, 1, 1, 17],
    [132, 10, 4, 1, 34],
    [132, 14, 3, 2, 51],
    [132, 17, 2, 2, 34],
    [132, 19, 4, 1, 17],
    [132, 23, 1, 1, 34],
    [132, 24, 2, 1, 17],
    [132, 26, 38, 1, 34],
    [132, 64, 9, 1, 17],
    [132, 73, 1, 1, 34],
    [132, 74, 5, 1, 17],
    [132, 79, 1, 1, 34],
    [132, 80, 3, 1, 17],
    [132, 83, 1, 1, 34],
    [132, 84, 6, 1, 17],
    [132, 90, 3, 1, 34],
    [132, 93, 1, 1, 17],
    [132, 94, 3, 1, 34],
    [132, 97, 1, 1, 17],
    [132, 98, 5, 1, 34],
    [132, 103, 2, 1, 17],
    [132, 105, 1, 2, 34],
    [132, 106, 4, 1, 17],
    [132, 110, 3, 1, 34],
    [132, 113, 2, 1, 17],
    [132, 115, 1, 1, 34],
    [132, 116, 1, 1, 17],
    [132, 117, 6, 1, 34],
    [132, 123, 1, 2, 17],
    [132, 124, 4, 2, 34],
    [132, 128, 1, 2, 17],
    [132, 129, 4, 1, 34],
    [132, 133, 8, 1, 17],
    [132, 141, 5, 2, 34],
    [132, 146, 11, 1, 17],
    [133, 0, 8, 1, 34],
    [133, 8, 1, 1, 17],
    [133, 9, 5, 1, 34],
    [133, 19, 9, 1, 17],
    [133, 28, 37, 1, 34],
    [133, 65, 12, 1, 17],
    [133, 77, 2, 1, 34],
    [133, 79, 1, 1, 17],
    [133, 80, 1, 1, 34],
    [133, 81, 7, 1, 17],
    [133, 88, 1, 1, 34],
    [133, 89, 4, 1, 17],
    [133, 93, 8, 1, 34],
    [133, 101, 4, 1, 17],
    [133, 106, 2, 1, 17],
    [133, 108, 2, 1, 34],
    [133, 110, 5, 1, 17],
    [133, 115, 4, 1, 34],
    [133, 119, 3, 1, 17],
    [133, 122, 1, 1, 34],
    [133, 129, 1, 1, 34],
    [133, 130, 11, 1, 17],
    [133, 146, 10, 1, 17],
    [133, 156, 4, 8, 34],
    [134, 0, 9, 1, 34],
    [134, 9, 3, 1, 17],
    [134, 12, 3, 1, 34],
    [134, 15, 3, 1, 51],
    [134, 18, 1, 1, 34],
    [134, 19, 13, 1, 17],
    [134, 32, 13, 1, 34],
    [134, 45, 1, 1, 17],
    [134, 46, 4, 1, 34],
    [134, 50, 4, 1, 17],
    [134, 54, 2, 1, 34],
    [134, 56, 85, 1, 17],
    [134, 141, 4, 1, 34],
    [134, 145, 11, 1, 17],
    [135, 0, 8, 2, 34],
    [135, 8, 2, 1, 17],
    [135, 10, 6, 1, 34],
    [135, 16, 2, 1, 51],
    [135, 18, 2, 1, 34],
    [135, 20, 120, 1, 17],
    [135, 140, 4, 1, 34],
    [135, 144, 12, 1, 17],
    [136, 8, 3, 1, 17],
    [136, 11, 1, 1, 34],
    [136, 12, 1, 1, 17],
    [136, 13, 8, 1, 34],
    [136, 21, 135, 2, 17],
    [137, 0, 7, 1, 34],
    [137, 7, 3, 1, 17],
    [137, 10, 1, 1, 34],
    [137, 11, 3, 1, 17],
    [137, 14, 7, 1, 34],
    [138, 0, 6, 1, 34],
    [138, 6, 1, 1, 17],
    [138, 7, 1, 1, 34],
    [138, 8, 7, 1, 17],
    [138, 15, 7, 1, 34],
    [138, 22, 134, 1, 17],
    [139, 0, 5, 1, 34],
    [139, 5, 10, 1, 17],
    [139, 15, 8, 1, 34],
    [139, 23, 133, 2, 17],
    [140, 0, 6, 1, 34],
    [140, 6, 12, 1, 17],
    [140, 18, 5, 1, 34],
    [141, 0, 4, 8, 34],
    [141, 4, 15, 1, 17],
    [141, 19, 5, 1, 34],
    [141, 24, 133, 1, 17],
    [141, 157, 3, 1, 34],
    [142, 4, 152, 3, 17],
    [142, 156, 4, 10, 34],
    [145, 4, 6, 1, 17],
    [145, 10, 140, 1, 0],
    [145, 150, 6, 1, 17],
    [146, 4, 152, 3, 17],
    [149, 0, 3, 1, 34],
    [149, 3, 153, 1, 17],
    [150, 0, 4, 2, 34],
    [150, 4, 152, 2, 17],
    [152, 0, 48, 1, 34],
    [152, 48, 2, 1, 17],
    [152, 50, 10, 1, 34],
    [152, 60, 1, 1, 17],
    [152, 61, 99, 1, 34],
    [153, 0, 160, 1, 34],
    [154, 0, 29, 1, 34],
    [154, 29, 1, 1, 17],
    [154, 30, 8, 1, 34],
    [154, 38, 3, 1, 17],
    [154, 41, 3, 1, 34],
    [154, 44, 1, 1, 17],
    [154, 45, 1, 1, 34],
    [154, 46, 1, 1, 17],
    [154, 47, 4, 1, 34],
    [154, 51, 4, 1, 17],
    [154, 55, 3, 1, 34],
    [154, 58, 2, 1, 17],
    [154, 60, 4, 1, 34],
    [154, 64, 2, 1, 17],
    [154, 66, 20, 1, 34],
    [154, 86, 1, 1, 17],
    [154, 87, 73, 1, 34],
    [155, 0, 30, 1, 34],
    [155, 30, 1, 1, 17],
    [155, 31, 6, 1, 34],
    [155, 37, 5, 1, 17],
    [155, 42, 1, 1, 34],
    [155, 43, 5, 1, 17],
    [155, 48, 3, 1, 34],
    [155, 51, 2, 1, 17],
    [155, 53, 2, 1, 34],
    [155, 55, 1, 1, 17],
    [155, 56, 1, 1, 34],
    [155, 57, 1, 1, 17],
    [155, 58, 1, 1, 34],
    [155, 59, 5, 1, 17],
    [155, 64, 14, 1, 34],
    [155, 78, 24, 1, 17],
    [155, 102, 58, 1, 34],
    [156, 0, 3, 2, 34],
    [156, 3, 1, 2, 51],
    [156, 4, 2, 1, 34],
    [156, 6, 1, 1, 17],
    [156, 7, 2, 1, 34],
    [156, 9, 2, 1, 17],
    [156, 11, 1, 1, 34],
    [156, 12, 1, 1, 17],
    [156, 13, 1, 1, 34],
    [156, 14, 1, 1, 17],
    [156, 15, 1, 1, 34],
    [156, 16, 140, 1, 17],
    [156, 156, 4, 2, 34],
    [157, 4, 3, 1, 17],
    [157, 7, 1, 1, 34],
    [157, 8, 2, 1, 17],
    [157, 10, 1, 1, 34],
    [157, 11, 145, 1, 17],
    [158, 0, 4, 1, 34],
    [158, 4, 156, 1, 17],
    [159, 0, 159, 1, 17],
    [159, 159, 1, 1, 34]
];

module acer_bottom_projection(width = 150, depth = 150, thickness = 0.05) {
    pixel_x = width / acer_projection_size;
    pixel_y = depth / acer_projection_size;

    for (rect = acer_projection_rectangles) {
        shade = rect[4] / 255;
        color([shade, shade, shade])
            translate([rect[1] * pixel_x,
                       (acer_projection_size - rect[0] - rect[3]) * pixel_y,
                       -thickness])
                cube([rect[2] * pixel_x + 0.01,
                      rect[3] * pixel_y + 0.01,
                      thickness]);
    }
}
