alexliesenfeld/dgx-spark-printables/spark-atom/images/asus-gx10-bottom-projection.scad

/*
 * Demo-only pixel projection generated from asus-gx10-bottom.jpg.
 * Rows are stored top-to-bottom; the module flips them so the photograph's
 * bottom edge maps to Y=0, the physical front of the device.
 * Adjacent equal-shade pixels are merged into rectangles for faster previews.
 */

gx10_projection_size = 160;
gx10_projection_rectangles = [
    [0, 0, 1, 1, 153],
    [0, 1, 1, 1, 187],
    [0, 2, 62, 2, 170],
    [0, 64, 1, 2, 153],
    [0, 65, 1, 2, 170],
    [0, 66, 2, 1, 153],
    [0, 68, 2, 1, 170],
    [0, 70, 4, 1, 153],
    [0, 74, 3, 1, 170],
    [0, 77, 1, 1, 153],
    [0, 78, 1, 1, 170],
    [0, 79, 3, 1, 153],
    [0, 82, 1, 1, 170],
    [0, 83, 28, 1, 153],
    [0, 111, 29, 1, 136],
    [0, 140, 19, 1, 119],
    [0, 159, 1, 1, 85],
    [1, 0, 1, 81, 136],
    [1, 1, 1, 81, 153],
    [1, 66, 1, 1, 153],
    [1, 67, 3, 1, 170],
    [1, 70, 3, 1, 153],
    [1, 73, 6, 1, 170],
    [1, 79, 1, 1, 153],
    [1, 80, 1, 1, 170],
    [1, 81, 1, 1, 153],
    [1, 82, 2, 1, 170],
    [1, 84, 21, 1, 153],
    [1, 105, 2, 1, 136],
    [1, 107, 2, 1, 153],
    [1, 109, 24, 1, 136],
    [1, 133, 22, 1, 119],
    [1, 155, 3, 1, 102],
    [1, 158, 2, 1, 85],
    [2, 2, 63, 1, 204],
    [2, 65, 1, 1, 187],
    [2, 66, 4, 1, 204],
    [2, 70, 23, 1, 187],
    [2, 93, 30, 1, 170],
    [2, 123, 15, 1, 153],
    [2, 138, 1, 1, 136],
    [2, 139, 1, 1, 153],
    [2, 140, 9, 1, 136],
    [2, 149, 1, 1, 119],
    [2, 150, 1, 1, 136],
    [2, 151, 1, 1, 119],
    [2, 152, 4, 1, 136],
    [2, 156, 2, 1, 119],
    [2, 158, 1, 5, 102],
    [2, 159, 1, 5, 85],
    [3, 2, 6, 1, 187],
    [3, 8, 4, 1, 204],
    [3, 12, 8, 1, 187],
    [3, 20, 4, 1, 204],
    [3, 24, 7, 1, 187],
    [3, 31, 1, 1, 204],
    [3, 32, 40, 1, 187],
    [3, 72, 43, 1, 170],
    [3, 115, 1, 1, 153],
    [3, 116, 1, 1, 170],
    [3, 117, 14, 1, 153],
    [3, 131, 18, 1, 136],
    [3, 149, 3, 1, 119],
    [3, 152, 1, 1, 136],
    [3, 153, 5, 1, 119],
    [4, 2, 3, 2, 187],
    [4, 5, 3, 2, 204],
    [4, 8, 1, 1, 187],
    [4, 9, 9, 1, 204],
    [4, 18, 4, 1, 187],
    [4, 22, 14, 1, 204],
    [4, 36, 2, 1, 187],
    [4, 38, 2, 1, 204],
    [4, 40, 2, 1, 187],
    [4, 42, 4, 1, 204],
    [4, 46, 2, 1, 187],
    [4, 48, 4, 1, 204],
    [4, 52, 23, 1, 187],
    [4, 75, 2, 1, 170],
    [4, 77, 6, 1, 187],
    [4, 83, 1, 1, 170],
    [4, 84, 1, 2, 187],
    [4, 85, 29, 1, 170],
    [4, 114, 17, 1, 153],
    [4, 131, 1, 1, 136],
    [4, 132, 1, 1, 153],
    [4, 133, 14, 1, 136],
    [4, 147, 2, 1, 119],
    [4, 149, 1, 1, 136],
    [4, 150, 8, 1, 119],
    [5, 8, 2, 3, 187],
    [5, 10, 8, 1, 204],
    [5, 18, 1, 1, 187],
    [5, 19, 1, 1, 204],
    [5, 20, 2, 1, 187],
    [5, 22, 5, 1, 204],
    [5, 27, 1, 1, 187],
    [5, 28, 2, 1, 204],
    [5, 30, 1, 1, 187],
    [5, 31, 5, 1, 204],
    [5, 36, 3, 1, 187],
    [5, 39, 1, 1, 204],
    [5, 40, 3, 1, 187],
    [5, 43, 1, 1, 204],
    [5, 44, 5, 1, 187],
    [5, 49, 2, 1, 204],
    [5, 51, 23, 1, 187],
    [5, 74, 4, 1, 170],
    [5, 78, 1, 1, 187],
    [5, 79, 5, 1, 170],
    [5, 85, 26, 1, 170],
    [5, 111, 1, 2, 153],
    [5, 112, 2, 1, 170],
    [5, 114, 16, 1, 153],
    [5, 130, 1, 1, 136],
    [5, 131, 2, 1, 153],
    [5, 133, 2, 1, 136],
    [5, 135, 1, 1, 153],
    [5, 136, 12, 1, 136],
    [5, 148, 10, 1, 119],
    [6, 2, 4, 1, 187],
    [6, 6, 2, 1, 204],
    [6, 10, 1, 1, 204],
    [6, 11, 1, 1, 187],
    [6, 12, 8, 1, 204],
    [6, 20, 3, 1, 187],
    [6, 23, 3, 1, 204],
    [6, 26, 5, 1, 187],
    [6, 31, 3, 1, 204],
    [6, 34, 4, 2, 187],
    [6, 38, 2, 3, 204],
    [6, 40, 1, 2, 187],
    [6, 41, 3, 2, 204],
    [6, 44, 6, 2, 187],
    [6, 50, 2, 1, 204],
    [6, 52, 23, 1, 187],
    [6, 75, 1, 1, 170],
    [6, 76, 5, 1, 187],
    [6, 81, 1, 1, 170],
    [6, 82, 1, 1, 187],
    [6, 83, 28, 1, 170],
    [6, 112, 1, 2, 170],
    [6, 113, 19, 1, 153],
    [6, 132, 1, 1, 136],
    [6, 133, 1, 1, 153],
    [6, 134, 13, 1, 136],
    [6, 147, 1, 1, 119],
    [6, 148, 3, 1, 136],
    [6, 151, 7, 1, 119],
    [7, 2, 2, 1, 187],
    [7, 4, 4, 1, 204],
    [7, 10, 2, 1, 170],
    [7, 12, 1, 1, 153],
    [7, 13, 1, 1, 170],
    [7, 14, 1, 1, 204],
    [7, 15, 1, 1, 187],
    [7, 16, 4, 1, 204],
    [7, 20, 2, 1, 187],
    [7, 22, 4, 1, 204],
    [7, 26, 4, 1, 187],
    [7, 30, 4, 1, 204],
    [7, 50, 1, 1, 204],
    [7, 51, 32, 1, 187],
    [7, 83, 27, 1, 170],
    [7, 110, 2, 1, 153],
    [7, 113, 18, 1, 153],
    [7, 131, 1, 1, 136],
    [7, 132, 1, 1, 153],
    [7, 133, 14, 1, 136],
    [7, 147, 1, 1, 102],
    [7, 148, 2, 1, 85],
    [7, 150, 8, 1, 119],
    [7, 158, 2, 26, 85],
    [8, 2, 5, 1, 204],
    [8, 7, 1, 1, 187],
    [8, 8, 1, 1, 204],
    [8, 9, 1, 1, 153],
    [8, 10, 1, 1, 170],
    [8, 11, 2, 1, 204],
    [8, 13, 1, 1, 136],
    [8, 14, 1, 3, 170],
    [8, 15, 5, 1, 204],
    [8, 20, 1, 1, 187],
    [8, 21, 6, 1, 204],
    [8, 27, 1, 1, 187],
    [8, 28, 7, 1, 204],
    [8, 35, 3, 1, 187],
    [8, 40, 4, 1, 187],
    [8, 44, 1, 3, 204],
    [8, 45, 1, 1, 187],
    [8, 46, 1, 1, 204],
    [8, 47, 27, 1, 187],
    [8, 74, 1, 1, 170],
    [8, 75, 1, 1, 187],
    [8, 76, 1, 1, 170],
    [8, 77, 2, 1, 187],
    [8, 79, 1, 1, 170],
    [8, 80, 3, 1, 187],
    [8, 83, 29, 1, 170],
    [8, 112, 2, 1, 153],
    [8, 114, 1, 1, 170],
    [8, 115, 16, 1, 153],
    [8, 131, 3, 1, 136],
    [8, 134, 1, 1, 153],
    [8, 135, 10, 1, 136],
    [8, 145, 1, 1, 119],
    [8, 146, 1, 1, 102],
    [8, 147, 2, 1, 68],
    [8, 149, 1, 1, 51],
    [8, 150, 1, 1, 102],
    [8, 151, 1, 1, 136],
    [8, 152, 6, 1, 119],
    [9, 2, 6, 1, 204],
    [9, 8, 1, 1, 187],
    [9, 9, 1, 2, 136],
    [9, 10, 1, 1, 204],
    [9, 11, 1, 1, 187],
    [9, 12, 1, 1, 204],
    [9, 13, 1, 2, 153],
    [9, 15, 4, 1, 204],
    [9, 19, 2, 1, 187],
    [9, 21, 3, 1, 204],
    [9, 24, 1, 1, 187],
    [9, 25, 1, 1, 204],
    [9, 26, 2, 1, 187],
    [9, 28, 6, 1, 204],
    [9, 34, 4, 1, 187],
    [9, 38, 3, 1, 204],
    [9, 41, 3, 1, 187],
    [9, 45, 2, 1, 187],
    [9, 47, 1, 1, 204],
    [9, 48, 26, 1, 187],
    [9, 74, 4, 1, 170],
    [9, 78, 3, 1, 187],
    [9, 81, 29, 1, 170],
    [9, 110, 15, 1, 153],
    [9, 125, 1, 1, 136],
    [9, 126, 5, 1, 153],
    [9, 131, 14, 1, 136],
    [9, 145, 1, 2, 102],
    [9, 146, 5, 1, 68],
    [9, 151, 6, 1, 119],
    [9, 157, 1, 1, 102],
    [10, 2, 5, 2, 204],
    [10, 7, 1, 2, 187],
    [10, 8, 1, 2, 204],
    [10, 10, 3, 1, 204],
    [10, 15, 3, 1, 204],
    [10, 18, 4, 2, 187],
    [10, 22, 2, 2, 204],
    [10, 24, 6, 1, 187],
    [10, 30, 6, 1, 204],
    [10, 36, 3, 1, 187],
    [10, 39, 3, 1, 204],
    [10, 42, 2, 1, 187],
    [10, 45, 3, 1, 187],
    [10, 48, 2, 1, 204],
    [10, 50, 23, 2, 187],
    [10, 73, 3, 1, 170],
    [10, 76, 3, 1, 187],
    [10, 79, 32, 1, 170],
    [10, 111, 15, 1, 153],
    [10, 126, 16, 1, 136],
    [10, 142, 2, 1, 119],
    [10, 144, 1, 1, 136],
    [10, 146, 1, 1, 68],
    [10, 147, 2, 1, 85],
    [10, 149, 1, 1, 68],
    [10, 150, 1, 1, 102],
    [10, 151, 7, 1, 119],
    [11, 9, 1, 1, 170],
    [11, 10, 1, 1, 153],
    [11, 11, 3, 1, 170],
    [11, 14, 4, 1, 204],
    [11, 24, 5, 1, 187],
    [11, 29, 7, 1, 204],
    [11, 36, 4, 1, 187],
    [11, 40, 2, 1, 204],
    [11, 42, 1, 1, 187],
    [11, 43, 1, 1, 204],
    [11, 44, 5, 1, 187],
    [11, 49, 1, 1, 204],
    [11, 73, 4, 1, 170],
    [11, 77, 4, 1, 187],
    [11, 81, 30, 1, 170],
    [11, 111, 13, 1, 153],
    [11, 124, 1, 1, 136],
    [11, 125, 1, 1, 153],
    [11, 126, 20, 1, 136],
    [11, 146, 1, 1, 85],
    [11, 147, 1, 1, 51],
    [11, 148, 1, 1, 68],
    [11, 149, 1, 1, 102],
    [11, 150, 8, 1, 119],
    [12, 2, 4, 2, 204],
    [12, 6, 2, 2, 187],
    [12, 8, 2, 1, 204],
    [12, 10, 3, 1, 170],
    [12, 13, 4, 1, 204],
    [12, 17, 3, 1, 187],
    [12, 20, 5, 1, 204],
    [12, 25, 1, 1, 187],
    [12, 26, 2, 1, 204],
    [12, 28, 8, 2, 187],
    [12, 36, 4, 1, 204],
    [12, 40, 1, 1, 187],
    [12, 41, 4, 1, 204],
    [12, 45, 6, 1, 187],
    [12, 51, 1, 1, 204],
    [12, 52, 25, 1, 187],
    [12, 77, 28, 1, 170],
    [12, 105, 1, 2, 153],
    [12, 106, 2, 1, 170],
    [12, 108, 1, 1, 153],
    [12, 109, 1, 1, 170],
    [12, 110, 15, 1, 153],
    [12, 125, 5, 1, 136],
    [12, 130, 1, 1, 153],
    [12, 131, 11, 1, 136],
    [12, 142, 1, 1, 119],
    [12, 143, 1, 1, 136],
    [12, 144, 2, 1, 119],
    [12, 146, 1, 2, 136],
    [12, 147, 2, 1, 119],
    [12, 149, 1, 1, 136],
    [12, 150, 7, 1, 119],
    [12, 157, 1, 2, 102],
    [13, 8, 5, 1, 204],
    [13, 13, 1, 1, 187],
    [13, 14, 5, 1, 204],
    [13, 19, 1, 1, 187],
    [13, 20, 4, 1, 170],
    [13, 24, 1, 1, 187],
    [13, 25, 3, 1, 204],
    [13, 36, 3, 1, 204],
    [13, 39, 1, 1, 187],
    [13, 40, 2, 1, 204],
    [13, 42, 2, 1, 187],
    [13, 44, 1, 1, 204],
    [13, 45, 31, 1, 187],
    [13, 76, 29, 2, 170],
    [13, 106, 1, 1, 170],
    [13, 107, 20, 1, 153],
    [13, 127, 9, 1, 136],
    [13, 136, 4, 1, 119],
    [13, 140, 3, 1, 136],
    [13, 143, 3, 1, 119],
    [13, 147, 10, 1, 119],
    [14, 2, 1, 1, 187],
    [14, 3, 2, 1, 204],
    [14, 5, 3, 1, 187],
    [14, 8, 3, 1, 204],
    [14, 11, 3, 1, 187],
    [14, 14, 4, 1, 204],
    [14, 18, 1, 1, 153],
    [14, 19, 2, 1, 119],
    [14, 21, 3, 1, 102],
    [14, 24, 1, 1, 119],
    [14, 25, 1, 1, 136],
    [14, 26, 1, 1, 170],
    [14, 27, 3, 1, 204],
    [14, 30, 5, 1, 187],
    [14, 35, 3, 2, 204],
    [14, 38, 28, 1, 187],
    [14, 66, 2, 1, 170],
    [14, 68, 1, 1, 187],
    [14, 69, 3, 1, 170],
    [14, 72, 1, 1, 187],
    [14, 73, 1, 1, 170],
    [14, 74, 2, 2, 187],
    [14, 105, 14, 1, 153],
    [14, 119, 1, 2, 136],
    [14, 120, 4, 2, 153],
    [14, 124, 10, 1, 136],
    [14, 134, 1, 1, 102],
    [14, 135, 2, 1, 85],
    [14, 137, 3, 1, 68],
    [14, 140, 1, 1, 85],
    [14, 141, 1, 1, 102],
    [14, 142, 1, 1, 136],
    [14, 143, 13, 1, 119],
    [14, 156, 1, 1, 102],
    [14, 157, 1, 1, 119],
    [15, 2, 2, 4, 204],
    [15, 4, 1, 1, 187],
    [15, 5, 1, 1, 204],
    [15, 6, 2, 1, 187],
    [15, 8, 4, 1, 204],
    [15, 12, 3, 1, 187],
    [15, 15, 1, 1, 204],
    [15, 16, 1, 1, 187],
    [15, 17, 1, 1, 136],
    [15, 18, 2, 1, 102],
    [15, 20, 4, 1, 119],
    [15, 24, 3, 1, 102],
    [15, 27, 1, 1, 170],
    [15, 28, 1, 1, 204],
    [15, 29, 1, 1, 187],
    [15, 30, 1, 1, 204],
    [15, 31, 4, 1, 187],
    [15, 38, 6, 1, 187],
    [15, 44, 1, 1, 204],
    [15, 45, 1, 1, 187],
    [15, 46, 1, 1, 204],
    [15, 47, 19, 1, 187],
    [15, 66, 1, 1, 170],
    [15, 67, 2, 1, 187],
    [15, 69, 5, 1, 170],
    [15, 76, 28, 1, 170],
    [15, 104, 1, 1, 153],
    [15, 105, 1, 1, 170],
    [15, 106, 13, 1, 153],
    [15, 124, 8, 1, 136],
    [15, 132, 1, 1, 119],
    [15, 133, 1, 1, 85],
    [15, 134, 8, 1, 68],
    [15, 142, 1, 1, 85],
    [15, 143, 12, 1, 119],
    [15, 155, 3, 1, 102],
    [16, 4, 8, 2, 187],
    [16, 12, 3, 2, 204],
    [16, 15, 1, 1, 187],
    [16, 16, 1, 1, 119],
    [16, 17, 1, 1, 102],
    [16, 18, 9, 1, 119],
    [16, 27, 1, 1, 102],
    [16, 28, 1, 1, 153],
    [16, 29, 1, 1, 204],
    [16, 30, 2, 1, 187],
    [16, 32, 6, 1, 204],
    [16, 38, 3, 1, 187],
    [16, 41, 1, 1, 204],
    [16, 42, 23, 1, 187],
    [16, 65, 7, 1, 170],
    [16, 72, 3, 2, 187],
    [16, 75, 27, 2, 170],
    [16, 102, 1, 1, 153],
    [16, 103, 4, 1, 170],
    [16, 107, 13, 1, 153],
    [16, 120, 2, 1, 136],
    [16, 122, 2, 1, 153],
    [16, 124, 3, 1, 136],
    [16, 127, 1, 1, 153],
    [16, 128, 3, 1, 136],
    [16, 131, 1, 1, 119],
    [16, 132, 1, 1, 85],
    [16, 133, 1, 1, 68],
    [16, 134, 8, 1, 85],
    [16, 142, 2, 1, 68],
    [16, 144, 11, 1, 119],
    [16, 155, 1, 1, 102],
    [16, 156, 1, 1, 119],
    [16, 157, 1, 2, 102],
    [17, 15, 1, 1, 136],
    [17, 16, 1, 1, 102],
    [17, 17, 11, 1, 119],
    [17, 28, 1, 1, 85],
    [17, 29, 1, 1, 170],
    [17, 30, 1, 1, 204],
    [17, 31, 1, 1, 187],
    [17, 32, 4, 1, 204],
    [17, 36, 9, 1, 187],
    [17, 45, 1, 1, 204],
    [17, 46, 20, 1, 187],
    [17, 66, 4, 1, 170],
    [17, 70, 1, 1, 187],
    [17, 71, 1, 2, 170],
    [17, 102, 2, 1, 153],
    [17, 104, 2, 1, 170],
    [17, 106, 14, 1, 153],
    [17, 120, 1, 1, 136],
    [17, 121, 2, 1, 153],
    [17, 123, 1, 1, 136],
    [17, 124, 1, 1, 153],
    [17, 125, 5, 1, 136],
    [17, 130, 1, 1, 119],
    [17, 131, 1, 1, 85],
    [17, 132, 4, 1, 68],
    [17, 136, 4, 1, 85],
    [17, 140, 2, 1, 68],
    [17, 142, 1, 1, 85],
    [17, 143, 1, 1, 68],
    [17, 144, 1, 1, 85],
    [17, 145, 9, 1, 119],
    [17, 154, 1, 1, 102],
    [17, 155, 2, 1, 119],
    [18, 4, 2, 1, 187],
    [18, 6, 2, 2, 204],
    [18, 8, 1, 2, 187],
    [18, 9, 5, 2, 204],
    [18, 14, 1, 1, 170],
    [18, 15, 1, 3, 102],
    [18, 16, 10, 1, 119],
    [18, 26, 1, 1, 102],
    [18, 27, 1, 1, 119],
    [18, 28, 1, 1, 102],
    [18, 29, 1, 1, 119],
    [18, 30, 10, 1, 187],
    [18, 40, 1, 1, 204],
    [18, 41, 5, 1, 187],
    [18, 46, 1, 1, 204],
    [18, 47, 24, 1, 187],
    [18, 72, 2, 1, 187],
    [18, 74, 29, 1, 170],
    [18, 103, 17, 1, 153],
    [18, 120, 10, 1, 136],
    [18, 130, 1, 1, 85],
    [18, 131, 7, 1, 68],
    [18, 138, 1, 1, 85],
    [18, 139, 1, 1, 68],
    [18, 140, 1, 2, 85],
    [18, 141, 2, 2, 68],
    [18, 143, 1, 2, 85],
    [18, 144, 1, 1, 68],
    [18, 145, 1, 1, 102],
    [18, 146, 2, 1, 119],
    [18, 148, 1, 1, 102],
    [18, 149, 6, 1, 119],
    [18, 155, 3, 1, 102],
    [19, 2, 2, 1, 187],
    [19, 4, 1, 1, 204],
    [19, 5, 1, 1, 187],
    [19, 14, 1, 1, 136],
    [19, 16, 13, 1, 119],
    [19, 29, 1, 5, 85],
    [19, 30, 1, 1, 170],
    [19, 31, 1, 5, 204],
    [19, 32, 35, 1, 187],
    [19, 67, 1, 1, 170],
    [19, 68, 5, 1, 187],
    [19, 73, 1, 1, 170],
    [19, 74, 1, 1, 187],
    [19, 75, 26, 1, 170],
    [19, 101, 1, 1, 153],
    [19, 102, 4, 1, 170],
    [19, 106, 13, 1, 153],
    [19, 119, 10, 1, 136],
    [19, 129, 1, 1, 119],
    [19, 130, 1, 2, 68],
    [19, 131, 1, 1, 85],
    [19, 132, 8, 1, 68],
    [19, 144, 2, 1, 68],
    [19, 146, 7, 1, 119],
    [19, 153, 1, 1, 102],
    [19, 154, 2, 1, 119],
    [19, 156, 2, 1, 102],
    [20, 2, 12, 1, 204],
    [20, 14, 1, 1, 119],
    [20, 16, 11, 1, 119],
    [20, 27, 1, 4, 102],
    [20, 28, 1, 5, 119],
    [20, 30, 1, 1, 136],
    [20, 32, 1, 4, 187],
    [20, 33, 2, 1, 204],
    [20, 35, 10, 1, 187],
    [20, 45, 1, 1, 204],
    [20, 46, 23, 1, 187],
    [20, 69, 30, 1, 170],
    [20, 99, 1, 1, 153],
    [20, 100, 4, 1, 170],
    [20, 104, 13, 1, 153],
    [20, 117, 2, 1, 136],
    [20, 119, 1, 1, 153],
    [20, 120, 9, 1, 136],
    [20, 129, 1, 1, 102],
    [20, 131, 4, 1, 85],
    [20, 135, 3, 2, 68],
    [20, 138, 2, 1, 85],
    [20, 140, 6, 1, 68],
    [20, 146, 1, 2, 102],
    [20, 147, 5, 1, 119],
    [20, 152, 1, 2, 102],
    [20, 153, 1, 2, 119],
    [20, 154, 4, 2, 102],
    [21, 2, 11, 1, 204],
    [21, 13, 1, 2, 187],
    [21, 14, 13, 1, 119],
    [21, 30, 1, 3, 119],
    [21, 33, 1, 1, 204],
    [21, 34, 28, 1, 187],
    [21, 62, 2, 1, 170],
    [21, 64, 6, 1, 187],
    [21, 70, 28, 1, 170],
    [21, 98, 2, 1, 153],
    [21, 100, 2, 1, 170],
    [21, 102, 14, 1, 153],
    [21, 116, 4, 1, 136],
    [21, 120, 1, 1, 153],
    [21, 121, 8, 1, 136],
    [21, 129, 1, 3, 85],
    [21, 130, 2, 1, 68],
    [21, 132, 3, 1, 85],
    [21, 138, 1, 1, 85],
    [21, 139, 7, 1, 68],
    [21, 147, 3, 1, 119],
    [21, 150, 1, 1, 102],
    [21, 151, 1, 1, 119],
    [22, 2, 4, 1, 204],
    [22, 6, 4, 1, 187],
    [22, 10, 3, 1, 204],
    [22, 14, 1, 2, 119],
    [22, 15, 1, 4, 102],
    [22, 16, 11, 1, 119],
    [22, 33, 2, 2, 204],
    [22, 35, 3, 2, 187],
    [22, 38, 1, 1, 204],
    [22, 39, 29, 1, 187],
    [22, 68, 29, 1, 170],
    [22, 97, 2, 1, 153],
    [22, 99, 3, 1, 170],
    [22, 102, 11, 1, 153],
    [22, 113, 1, 1, 136],
    [22, 114, 3, 1, 153],
    [22, 117, 12, 1, 136],
    [22, 130, 1, 2, 68],
    [22, 131, 3, 2, 85],
    [22, 134, 12, 1, 68],
    [22, 146, 1, 1, 85],
    [22, 147, 6, 1, 119],
    [22, 153, 5, 1, 102],
    [23, 2, 2, 1, 204],
    [23, 4, 9, 1, 187],
    [23, 13, 1, 1, 204],
    [23, 16, 5, 1, 119],
    [23, 21, 3, 1, 102],
    [23, 24, 3, 1, 119],
    [23, 38, 2, 1, 204],
    [23, 40, 26, 1, 187],
    [23, 66, 32, 1, 170],
    [23, 98, 20, 1, 153],
    [23, 118, 11, 1, 136],
    [23, 134, 4, 1, 68],
    [23, 138, 1, 1, 85],
    [23, 139, 7, 1, 68],
    [23, 146, 1, 3, 102],
    [23, 147, 4, 1, 119],
    [23, 151, 7, 1, 102],
    [24, 2, 3, 1, 204],
    [24, 5, 6, 1, 187],
    [24, 11, 3, 2, 204],
    [24, 14, 1, 1, 136],
    [24, 16, 2, 1, 119],
    [24, 18, 1, 1, 102],
    [24, 19, 4, 1, 119],
    [24, 23, 1, 2, 102],
    [24, 24, 2, 2, 119],
    [24, 26, 2, 1, 102],
    [24, 29, 1, 1, 68],
    [24, 30, 1, 1, 153],
    [24, 31, 4, 1, 204],
    [24, 35, 4, 1, 187],
    [24, 39, 1, 1, 204],
    [24, 40, 18, 1, 187],
    [24, 58, 1, 1, 170],
    [24, 59, 1, 1, 187],
    [24, 60, 2, 1, 170],
    [24, 62, 2, 2, 187],
    [24, 64, 33, 1, 170],
    [24, 97, 1, 1, 153],
    [24, 98, 1, 1, 170],
    [24, 99, 18, 1, 153],
    [24, 117, 1, 1, 136],
    [24, 118, 1, 1, 153],
    [24, 119, 10, 1, 136],
    [24, 129, 1, 1, 102],
    [24, 130, 1, 2, 51],
    [24, 131, 1, 1, 85],
    [24, 132, 14, 1, 68],
    [24, 147, 1, 1, 119],
    [24, 148, 1, 1, 102],
    [24, 149, 3, 1, 119],
    [24, 152, 6, 1, 102],
    [25, 2, 4, 1, 204],
    [25, 6, 5, 1, 187],
    [25, 14, 1, 1, 170],
    [25, 16, 7, 1, 119],
    [25, 26, 1, 1, 102],
    [25, 27, 1, 1, 119],
    [25, 28, 1, 1, 102],
    [25, 29, 1, 1, 85],
    [25, 30, 1, 1, 170],
    [25, 31, 1, 1, 204],
    [25, 32, 2, 1, 187],
    [25, 34, 2, 1, 204],
    [25, 36, 22, 1, 187],
    [25, 58, 4, 1, 170],
    [25, 64, 4, 1, 170],
    [25, 68, 1, 1, 187],
    [25, 69, 27, 1, 170],
    [25, 96, 20, 1, 153],
    [25, 116, 1, 1, 136],
    [25, 117, 1, 1, 153],
    [25, 118, 11, 1, 136],
    [25, 129, 1, 1, 119],
    [25, 131, 1, 1, 68],
    [25, 132, 1, 2, 85],
    [25, 133, 13, 1, 68],
    [25, 147, 2, 1, 119],
    [25, 149, 1, 1, 102],
    [25, 150, 1, 1, 119],
    [25, 151, 1, 1, 102],
    [25, 152, 1, 1, 119],
    [25, 153, 5, 1, 102],
    [26, 2, 2, 1, 204],
    [26, 4, 8, 1, 187],
    [26, 12, 1, 1, 204],
    [26, 13, 1, 1, 187],
    [26, 14, 1, 1, 204],
    [26, 15, 1, 1, 136],
    [26, 16, 1, 1, 102],
    [26, 17, 5, 1, 119],
    [26, 22, 2, 2, 102],
    [26, 24, 1, 1, 119],
    [26, 25, 1, 1, 102],
    [26, 26, 2, 1, 119],
    [26, 28, 1, 1, 68],
    [26, 29, 1, 1, 136],
    [26, 30, 30, 2, 187],
    [26, 60, 1, 1, 170],
    [26, 61, 1, 1, 187],
    [26, 62, 1, 1, 170],
    [26, 63, 1, 1, 187],
    [26, 64, 31, 1, 170],
    [26, 95, 1, 1, 153],
    [26, 96, 2, 1, 170],
    [26, 98, 13, 1, 153],
    [26, 111, 1, 1, 136],
    [26, 112, 4, 1, 153],
    [26, 116, 12, 1, 136],
    [26, 128, 1, 1, 119],
    [26, 129, 1, 1, 136],
    [26, 130, 1, 1, 85],
    [26, 131, 1, 1, 51],
    [26, 133, 11, 1, 68],
    [26, 144, 1, 1, 51],
    [26, 145, 1, 1, 85],
    [26, 146, 1, 2, 119],
    [26, 147, 11, 1, 102],
    [27, 2, 10, 1, 187],
    [27, 12, 3, 1, 204],
    [27, 15, 1, 1, 187],
    [27, 16, 1, 1, 119],
    [27, 17, 1, 1, 102],
    [27, 18, 4, 1, 119],
    [27, 24, 2, 1, 119],
    [27, 26, 1, 1, 102],
    [27, 27, 1, 1, 68],
    [27, 28, 1, 1, 119],
    [27, 29, 1, 1, 170],
    [27, 60, 37, 1, 170],
    [27, 97, 16, 1, 153],
    [27, 113, 16, 1, 136],
    [27, 129, 2, 1, 119],
    [27, 131, 1, 1, 68],
    [27, 132, 1, 1, 51],
    [27, 133, 1, 1, 85],
    [27, 134, 9, 1, 68],
    [27, 143, 1, 1, 51],
    [27, 144, 1, 1, 68],
    [27, 145, 1, 1, 102],
    [27, 147, 2, 1, 102],
    [27, 149, 1, 1, 119],
    [27, 150, 8, 1, 102],
    [28, 2, 3, 1, 187],
    [28, 5, 9, 1, 204],
    [28, 14, 1, 1, 187],
    [28, 15, 1, 1, 204],
    [28, 16, 1, 1, 187],
    [28, 17, 1, 1, 119],
    [28, 18, 1, 1, 85],
    [28, 19, 1, 2, 102],
    [28, 20, 5, 1, 119],
    [28, 25, 1, 1, 85],
    [28, 26, 1, 1, 68],
    [28, 27, 1, 1, 119],
    [28, 28, 1, 1, 170],
    [28, 29, 26, 1, 187],
    [28, 55, 1, 1, 170],
    [28, 56, 8, 1, 187],
    [28, 64, 2, 1, 170],
    [28, 66, 1, 1, 187],
    [28, 67, 27, 1, 170],
    [28, 94, 1, 1, 153],
    [28, 95, 1, 1, 170],
    [28, 96, 16, 1, 153],
    [28, 112, 15, 1, 136],
    [28, 127, 2, 1, 119],
    [28, 129, 1, 1, 136],
    [28, 130, 2, 1, 119],
    [28, 132, 2, 1, 51],
    [28, 134, 2, 1, 68],
    [28, 136, 4, 1, 85],
    [28, 140, 2, 1, 68],
    [28, 142, 2, 1, 51],
    [28, 144, 1, 1, 102],
    [28, 145, 1, 1, 119],
    [28, 146, 1, 1, 102],
    [28, 147, 1, 1, 119],
    [28, 148, 10, 1, 102],
    [29, 2, 2, 1, 187],
    [29, 4, 4, 1, 204],
    [29, 8, 1, 1, 187],
    [29, 9, 3, 1, 204],
    [29, 12, 6, 1, 187],
    [29, 18, 1, 1, 153],
    [29, 20, 5, 1, 85],
    [29, 25, 1, 1, 102],
    [29, 26, 1, 1, 153],
    [29, 27, 1, 1, 170],
    [29, 28, 2, 1, 187],
    [29, 30, 1, 1, 204],
    [29, 31, 1, 1, 187],
    [29, 32, 2, 1, 204],
    [29, 34, 18, 1, 187],
    [29, 52, 4, 1, 170],
    [29, 56, 1, 1, 187],
    [29, 57, 1, 1, 170],
    [29, 58, 2, 1, 187],
    [29, 60, 1, 1, 170],
    [29, 61, 4, 1, 187],
    [29, 65, 28, 1, 170],
    [29, 93, 17, 1, 153],
    [29, 110, 1, 1, 136],
    [29, 111, 1, 1, 153],
    [29, 112, 17, 1, 136],
    [29, 129, 4, 1, 119],
    [29, 133, 1, 1, 68],
    [29, 134, 4, 1, 51],
    [29, 138, 1, 1, 68],
    [29, 139, 3, 1, 51],
    [29, 142, 1, 1, 68],
    [29, 143, 1, 1, 102],
    [29, 144, 2, 1, 119],
    [29, 146, 12, 1, 102],
    [30, 2, 3, 2, 187],
    [30, 5, 5, 1, 204],
    [30, 10, 4, 1, 187],
    [30, 14, 3, 2, 204],
    [30, 17, 1, 1, 187],
    [30, 18, 1, 1, 204],
    [30, 19, 1, 1, 187],
    [30, 20, 1, 1, 170],
    [30, 21, 1, 1, 153],
    [30, 22, 1, 1, 136],
    [30, 23, 1, 1, 153],
    [30, 24, 1, 1, 170],
    [30, 25, 5, 1, 187],
    [30, 30, 4, 1, 204],
    [30, 34, 20, 1, 187],
    [30, 54, 1, 1, 170],
    [30, 55, 3, 1, 187],
    [30, 58, 4, 1, 170],
    [30, 62, 2, 1, 187],
    [30, 64, 29, 1, 170],
    [30, 93, 14, 1, 153],
    [30, 107, 1, 1, 136],
    [30, 108, 6, 1, 153],
    [30, 114, 13, 1, 136],
    [30, 127, 1, 1, 119],
    [30, 128, 2, 1, 136],
    [30, 130, 4, 1, 119],
    [30, 134, 1, 1, 102],
    [30, 135, 1, 1, 68],
    [30, 136, 4, 1, 51],
    [30, 140, 1, 1, 68],
    [30, 141, 1, 1, 85],
    [30, 142, 2, 1, 102],
    [30, 144, 1, 1, 119],
    [30, 145, 3, 1, 102],
    [30, 148, 1, 1, 119],
    [30, 149, 9, 1, 102],
    [31, 5, 6, 1, 204],
    [31, 11, 3, 1, 187],
    [31, 17, 3, 1, 187],
    [31, 20, 4, 1, 204],
    [31, 24, 5, 1, 187],
    [31, 29, 2, 1, 204],
    [31, 31, 24, 1, 187],
    [31, 55, 7, 1, 170],
    [31, 62, 1, 1, 187],
    [31, 63, 25, 1, 170],
    [31, 88, 1, 1, 153],
    [31, 89, 1, 1, 170],
    [31, 90, 18, 1, 153],
    [31, 108, 2, 1, 136],
    [31, 110, 2, 1, 153],
    [31, 112, 13, 1, 136],
    [31, 125, 11, 1, 119],
    [31, 136, 6, 1, 102],
    [31, 142, 3, 1, 119],
    [31, 145, 13, 1, 102],
    [32, 2, 5, 1, 204],
    [32, 7, 3, 1, 187],
    [32, 10, 6, 1, 204],
    [32, 16, 9, 1, 187],
    [32, 25, 1, 1, 204],
    [32, 26, 25, 1, 187],
    [32, 51, 2, 1, 170],
    [32, 53, 6, 1, 187],
    [32, 59, 2, 1, 170],
    [32, 61, 2, 1, 187],
    [32, 63, 29, 1, 170],
    [32, 92, 17, 1, 153],
    [32, 109, 17, 1, 136],
    [32, 126, 18, 1, 119],
    [32, 144, 14, 1, 102],
    [33, 2, 4, 1, 204],
    [33, 6, 4, 1, 187],
    [33, 10, 4, 1, 204],
    [33, 14, 2, 1, 187],
    [33, 16, 2, 1, 204],
    [33, 18, 6, 1, 187],
    [33, 24, 2, 1, 204],
    [33, 26, 24, 1, 187],
    [33, 50, 4, 1, 170],
    [33, 54, 4, 1, 187],
    [33, 58, 34, 1, 170],
    [33, 92, 16, 1, 153],
    [33, 108, 13, 1, 136],
    [33, 121, 1, 1, 119],
    [33, 122, 1, 1, 136],
    [33, 123, 1, 1, 119],
    [33, 124, 1, 1, 136],
    [33, 125, 17, 1, 119],
    [33, 142, 1, 1, 102],
    [33, 143, 1, 1, 119],
    [33, 144, 13, 1, 102],
    [33, 157, 1, 1, 85],
    [33, 158, 2, 4, 68],
    [34, 2, 6, 1, 204],
    [34, 8, 8, 1, 187],
    [34, 16, 4, 2, 204],
    [34, 20, 8, 1, 187],
    [34, 28, 1, 1, 204],
    [34, 29, 23, 1, 187],
    [34, 52, 3, 2, 170],
    [34, 55, 1, 2, 187],
    [34, 56, 30, 1, 170],
    [34, 86, 1, 1, 153],
    [34, 87, 6, 1, 170],
    [34, 93, 13, 1, 153],
    [34, 106, 2, 1, 136],
    [34, 108, 1, 1, 153],
    [34, 109, 13, 1, 136],
    [34, 122, 1, 1, 119],
    [34, 123, 1, 1, 136],
    [34, 124, 12, 1, 119],
    [34, 136, 3, 1, 102],
    [34, 139, 2, 1, 119],
    [34, 141, 1, 1, 102],
    [34, 142, 1, 1, 119],
    [34, 143, 15, 1, 102],
    [35, 2, 5, 1, 204],
    [35, 7, 9, 1, 187],
    [35, 20, 32, 1, 187],
    [35, 56, 33, 1, 170],
    [35, 89, 1, 1, 153],
    [35, 90, 1, 1, 170],
    [35, 91, 15, 1, 153],
    [35, 106, 1, 1, 136],
    [35, 107, 1, 1, 153],
    [35, 108, 12, 1, 136],
    [35, 120, 4, 1, 119],
    [35, 124, 1, 1, 136],
    [35, 125, 11, 1, 119],
    [35, 136, 1, 1, 102],
    [35, 137, 1, 1, 119],
    [35, 138, 2, 1, 102],
    [35, 140, 1, 1, 119],
    [35, 141, 13, 1, 102],
    [35, 154, 1, 1, 85],
    [35, 155, 2, 1, 102],
    [35, 157, 1, 2, 85],
    [36, 2, 4, 1, 204],
    [36, 6, 2, 1, 187],
    [36, 8, 2, 3, 204],
    [36, 10, 5, 1, 187],
    [36, 15, 1, 1, 204],
    [36, 16, 3, 1, 187],
    [36, 19, 2, 1, 204],
    [36, 21, 5, 2, 187],
    [36, 26, 1, 2, 204],
    [36, 27, 20, 1, 187],
    [36, 47, 1, 1, 170],
    [36, 48, 8, 2, 187],
    [36, 56, 2, 1, 170],
    [36, 58, 2, 1, 187],
    [36, 60, 27, 1, 170],
    [36, 87, 19, 1, 153],
    [36, 106, 15, 1, 136],
    [36, 121, 2, 1, 119],
    [36, 123, 1, 1, 136],
    [36, 124, 15, 1, 119],
    [36, 139, 18, 1, 102],
    [37, 2, 3, 1, 204],
    [37, 5, 3, 1, 187],
    [37, 10, 4, 2, 187],
    [37, 14, 2, 1, 204],
    [37, 16, 4, 1, 187],
    [37, 20, 1, 1, 204],
    [37, 27, 19, 1, 187],
    [37, 46, 2, 1, 170],
    [37, 56, 27, 1, 170],
    [37, 83, 1, 1, 153],
    [37, 84, 2, 1, 170],
    [37, 86, 19, 1, 153],
    [37, 105, 14, 1, 136],
    [37, 119, 2, 1, 119],
    [37, 121, 1, 1, 136],
    [37, 122, 14, 1, 119],
    [37, 136, 4, 1, 102],
    [37, 140, 1, 1, 119],
    [37, 141, 8, 1, 102],
    [37, 149, 1, 1, 85],
    [37, 150, 6, 1, 102],
    [37, 156, 2, 1, 85],
    [37, 158, 1, 1, 68],
    [37, 159, 1, 1, 85],
    [38, 2, 6, 1, 187],
    [38, 14, 1, 1, 204],
    [38, 15, 5, 1, 187],
    [38, 20, 2, 1, 204],
    [38, 22, 24, 2, 187],
    [38, 46, 3, 1, 170],
    [38, 49, 1, 1, 187],
    [38, 50, 4, 1, 170],
    [38, 54, 2, 1, 187],
    [38, 56, 28, 1, 170],
    [38, 84, 1, 1, 153],
    [38, 85, 2, 1, 170],
    [38, 87, 15, 1, 153],
    [38, 102, 16, 2, 136],
    [38, 118, 1, 2, 119],
    [38, 119, 6, 1, 136],
    [38, 125, 11, 1, 119],
    [38, 136, 1, 1, 102],
    [38, 137, 1, 1, 119],
    [38, 138, 12, 1, 102],
    [38, 150, 1, 1, 85],
    [38, 151, 4, 1, 102],
    [38, 155, 1, 1, 85],
    [38, 156, 2, 1, 102],
    [38, 158, 2, 1, 85],
    [39, 2, 7, 1, 187],
    [39, 9, 1, 1, 204],
    [39, 10, 1, 1, 187],
    [39, 11, 1, 1, 204],
    [39, 12, 9, 1, 187],
    [39, 21, 1, 1, 204],
    [39, 46, 9, 1, 170],
    [39, 55, 1, 1, 187],
    [39, 56, 26, 1, 170],
    [39, 82, 2, 1, 153],
    [39, 84, 4, 1, 170],
    [39, 88, 14, 1, 153],
    [39, 119, 1, 1, 136],
    [39, 120, 16, 1, 119],
    [39, 136, 2, 1, 102],
    [39, 138, 1, 1, 119],
    [39, 139, 13, 1, 102],
    [39, 152, 1, 1, 85],
    [39, 153, 1, 1, 102],
    [39, 154, 2, 1, 85],
    [39, 156, 1, 1, 102],
    [39, 157, 1, 1, 85],
    [39, 158, 2, 1, 68],
    [40, 2, 1, 3, 204],
    [40, 3, 4, 2, 187],
    [40, 7, 1, 2, 204],
    [40, 8, 2, 1, 187],
    [40, 10, 3, 1, 204],
    [40, 13, 1, 1, 187],
    [40, 14, 1, 1, 204],
    [40, 15, 1, 1, 187],
    [40, 16, 2, 2, 204],
    [40, 18, 25, 1, 187],
    [40, 43, 1, 1, 170],
    [40, 44, 4, 2, 187],
    [40, 48, 1, 2, 170],
    [40, 49, 3, 2, 187],
    [40, 52, 30, 1, 170],
    [40, 82, 1, 1, 153],
    [40, 83, 1, 1, 170],
    [40, 84, 18, 1, 153],
    [40, 102, 14, 2, 136],
    [40, 116, 2, 1, 119],
    [40, 118, 2, 1, 136],
    [40, 120, 13, 1, 119],
    [40, 133, 18, 1, 102],
    [40, 151, 3, 1, 85],
    [40, 154, 1, 1, 102],
    [40, 155, 4, 1, 85],
    [40, 159, 1, 1, 68],
    [41, 8, 4, 1, 187],
    [41, 12, 2, 1, 204],
    [41, 14, 2, 1, 187],
    [41, 18, 24, 1, 187],
    [41, 42, 2, 1, 170],
    [41, 52, 31, 1, 170],
    [41, 83, 16, 1, 153],
    [41, 99, 1, 1, 136],
    [41, 100, 2, 1, 153],
    [41, 116, 1, 1, 119],
    [41, 117, 1, 1, 136],
    [41, 118, 13, 1, 119],
    [41, 131, 3, 1, 102],
    [41, 134, 1, 1, 119],
    [41, 135, 16, 1, 102],
    [41, 151, 2, 1, 85],
    [41, 153, 1, 1, 102],
    [41, 154, 6, 1, 85],
    [42, 3, 13, 1, 187],
    [42, 16, 1, 1, 204],
    [42, 17, 25, 1, 187],
    [42, 42, 4, 1, 170],
    [42, 46, 3, 1, 187],
    [42, 49, 2, 1, 170],
    [42, 51, 1, 1, 187],
    [42, 52, 27, 1, 170],
    [42, 79, 1, 1, 153],
    [42, 80, 1, 1, 170],
    [42, 81, 4, 1, 153],
    [42, 85, 1, 1, 170],
    [42, 86, 14, 1, 153],
    [42, 100, 3, 1, 136],
    [42, 103, 1, 2, 153],
    [42, 104, 11, 1, 136],
    [42, 115, 2, 1, 119],
    [42, 117, 2, 1, 136],
    [42, 119, 1, 1, 119],
    [42, 120, 1, 1, 136],
    [42, 121, 11, 1, 119],
    [42, 132, 17, 1, 102],
    [42, 149, 2, 1, 85],
    [42, 151, 1, 1, 102],
    [42, 152, 5, 1, 85],
    [42, 157, 1, 1, 102],
    [42, 158, 1, 1, 68],
    [42, 159, 1, 1, 85],
    [43, 2, 4, 3, 187],
    [43, 6, 1, 1, 204],
    [43, 7, 34, 1, 187],
    [43, 41, 5, 1, 170],
    [43, 46, 1, 1, 187],
    [43, 47, 3, 1, 170],
    [43, 50, 1, 1, 187],
    [43, 51, 29, 1, 170],
    [43, 80, 1, 1, 153],
    [43, 81, 1, 1, 170],
    [43, 82, 1, 1, 153],
    [43, 83, 2, 1, 170],
    [43, 85, 13, 1, 153],
    [43, 98, 1, 1, 136],
    [43, 99, 3, 1, 153],
    [43, 102, 1, 1, 136],
    [43, 104, 9, 1, 136],
    [43, 113, 2, 1, 119],
    [43, 115, 2, 1, 136],
    [43, 117, 14, 1, 119],
    [43, 131, 15, 1, 102],
    [43, 146, 2, 2, 85],
    [43, 148, 5, 1, 102],
    [43, 153, 5, 1, 85],
    [43, 158, 2, 1, 68],
    [44, 6, 4, 2, 204],
    [44, 10, 34, 1, 187],
    [44, 44, 4, 2, 170],
    [44, 48, 2, 1, 187],
    [44, 50, 29, 1, 170],
    [44, 79, 1, 1, 153],
    [44, 80, 2, 1, 170],
    [44, 82, 13, 1, 153],
    [44, 95, 1, 1, 136],
    [44, 96, 1, 1, 153],
    [44, 97, 2, 1, 136],
    [44, 99, 1, 1, 153],
    [44, 100, 12, 1, 136],
    [44, 112, 5, 1, 119],
    [44, 117, 1, 1, 136],
    [44, 118, 11, 1, 119],
    [44, 129, 5, 1, 102],
    [44, 134, 1, 1, 119],
    [44, 135, 1, 1, 102],
    [44, 136, 1, 1, 119],
    [44, 137, 9, 1, 102],
    [44, 148, 1, 1, 102],
    [44, 149, 9, 1, 85],
    [44, 158, 1, 1, 68],
    [44, 159, 1, 1, 85],
    [45, 10, 4, 1, 187],
    [45, 14, 1, 1, 204],
    [45, 15, 25, 1, 187],
    [45, 40, 1, 1, 170],
    [45, 41, 3, 1, 187],
    [45, 48, 1, 1, 187],
    [45, 49, 31, 1, 170],
    [45, 80, 17, 1, 153],
    [45, 97, 16, 1, 136],
    [45, 113, 16, 1, 119],
    [45, 129, 1, 1, 102],
    [45, 130, 3, 1, 119],
    [45, 133, 14, 1, 102],
    [45, 147, 1, 1, 85],
    [45, 148, 2, 1, 102],
    [45, 150, 1, 1, 85],
    [45, 151, 3, 1, 102],
    [45, 154, 4, 1, 85],
    [45, 158, 2, 1, 68],
    [46, 2, 1, 2, 204],
    [46, 3, 36, 1, 187],
    [46, 39, 3, 1, 170],
    [46, 42, 4, 2, 187],
    [46, 46, 29, 1, 170],
    [46, 75, 1, 1, 153],
    [46, 76, 1, 1, 170],
    [46, 77, 1, 1, 153],
    [46, 78, 3, 1, 170],
    [46, 81, 15, 1, 153],
    [46, 96, 15, 1, 136],
    [46, 111, 1, 1, 119],
    [46, 112, 2, 1, 136],
    [46, 114, 16, 1, 119],
    [46, 130, 1, 1, 102],
    [46, 131, 2, 1, 119],
    [46, 133, 2, 1, 102],
    [46, 135, 1, 1, 119],
    [46, 136, 11, 1, 102],
    [46, 147, 2, 1, 85],
    [46, 149, 1, 1, 102],
    [46, 150, 8, 1, 85],
    [46, 158, 1, 3, 68],
    [46, 159, 1, 3, 85],
    [47, 3, 37, 1, 187],
    [47, 40, 2, 1, 170],
    [47, 46, 33, 1, 170],
    [47, 79, 16, 1, 153],
    [47, 95, 1, 1, 136],
    [47, 96, 1, 1, 153],
    [47, 97, 17, 1, 136],
    [47, 114, 1, 1, 119],
    [47, 115, 1, 1, 136],
    [47, 116, 8, 1, 119],
    [47, 124, 2, 1, 102],
    [47, 126, 2, 1, 119],
    [47, 128, 16, 1, 102],
    [47, 144, 1, 1, 85],
    [47, 145, 4, 1, 102],
    [47, 149, 9, 1, 85],
    [48, 2, 42, 1, 187],
    [48, 44, 29, 1, 170],
    [48, 73, 1, 1, 153],
    [48, 74, 3, 1, 170],
    [48, 77, 18, 1, 153],
    [48, 95, 13, 1, 136],
    [48, 108, 1, 1, 119],
    [48, 109, 5, 1, 136],
    [48, 114, 9, 1, 119],
    [48, 123, 1, 2, 102],
    [48, 124, 2, 2, 119],
    [48, 126, 4, 1, 102],
    [48, 130, 1, 1, 119],
    [48, 131, 12, 1, 102],
    [48, 143, 1, 3, 85],
    [48, 144, 5, 1, 102],
    [48, 149, 1, 2, 85],
    [48, 150, 1, 1, 102],
    [48, 151, 1, 1, 85],
    [48, 152, 1, 1, 102],
    [48, 153, 5, 1, 85],
    [49, 2, 30, 1, 187],
    [49, 32, 2, 1, 170],
    [49, 34, 6, 1, 187],
    [49, 40, 2, 1, 170],
    [49, 42, 2, 1, 187],
    [49, 44, 32, 1, 170],
    [49, 76, 18, 1, 153],
    [49, 94, 13, 3, 136],
    [49, 107, 2, 1, 119],
    [49, 109, 4, 1, 136],
    [49, 113, 10, 1, 119],
    [49, 126, 2, 1, 102],
    [49, 128, 1, 1, 119],
    [49, 129, 14, 1, 102],
    [49, 144, 2, 1, 102],
    [49, 146, 1, 1, 85],
    [49, 147, 2, 1, 102],
    [49, 150, 2, 1, 102],
    [49, 152, 6, 1, 85],
    [49, 158, 2, 20, 68],
    [50, 2, 2, 1, 187],
    [50, 4, 2, 1, 204],
    [50, 6, 26, 1, 187],
    [50, 32, 6, 1, 170],
    [50, 38, 1, 1, 187],
    [50, 39, 1, 1, 170],
    [50, 40, 3, 1, 187],
    [50, 43, 30, 1, 170],
    [50, 73, 21, 1, 153],
    [50, 107, 1, 2, 119],
    [50, 108, 1, 1, 136],
    [50, 109, 2, 1, 119],
    [50, 111, 1, 1, 136],
    [50, 112, 13, 1, 119],
    [50, 125, 18, 1, 102],
    [50, 144, 1, 1, 102],
    [50, 145, 2, 1, 85],
    [50, 147, 1, 1, 102],
    [50, 148, 6, 1, 85],
    [50, 154, 1, 1, 102],
    [50, 155, 3, 1, 85],
    [51, 2, 27, 1, 187],
    [51, 29, 1, 1, 170],
    [51, 30, 1, 1, 187],
    [51, 31, 9, 1, 170],
    [51, 40, 1, 3, 187],
    [51, 41, 29, 1, 170],
    [51, 70, 1, 1, 153],
    [51, 71, 1, 1, 170],
    [51, 72, 22, 1, 153],
    [51, 108, 2, 1, 136],
    [51, 110, 17, 1, 119],
    [51, 127, 17, 1, 102],
    [51, 144, 5, 1, 85],
    [51, 149, 1, 1, 102],
    [51, 150, 8, 1, 85],
    [52, 2, 34, 1, 187],
    [52, 36, 4, 2, 170],
    [52, 41, 28, 1, 170],
    [52, 69, 2, 1, 153],
    [52, 71, 3, 1, 170],
    [52, 74, 16, 1, 153],
    [52, 90, 3, 1, 136],
    [52, 93, 1, 1, 153],
    [52, 94, 9, 2, 136],
    [52, 103, 1, 1, 119],
    [52, 104, 1, 1, 136],
    [52, 105, 1, 1, 119],
    [52, 106, 1, 1, 136],
    [52, 107, 4, 1, 119],
    [52, 111, 2, 1, 136],
    [52, 113, 11, 1, 119],
    [52, 124, 2, 1, 102],
    [52, 126, 1, 1, 119],
    [52, 127, 15, 1, 102],
    [52, 142, 2, 1, 85],
    [52, 144, 1, 1, 102],
    [52, 145, 13, 1, 85],
    [53, 2, 32, 1, 187],
    [53, 34, 1, 1, 170],
    [53, 35, 1, 1, 187],
    [53, 41, 29, 1, 170],
    [53, 70, 3, 1, 153],
    [53, 73, 1, 2, 170],
    [53, 74, 1, 1, 153],
    [53, 75, 2, 1, 170],
    [53, 77, 11, 1, 153],
    [53, 88, 4, 1, 136],
    [53, 92, 2, 1, 153],
    [53, 103, 2, 1, 119],
    [53, 105, 1, 1, 136],
    [53, 106, 17, 1, 119],
    [53, 123, 16, 1, 102],
    [53, 139, 1, 2, 85],
    [53, 140, 2, 2, 102],
    [53, 142, 1, 1, 85],
    [53, 143, 1, 1, 102],
    [53, 144, 14, 1, 85],
    [54, 2, 30, 1, 187],
    [54, 32, 2, 1, 170],
    [54, 34, 6, 1, 187],
    [54, 40, 31, 1, 170],
    [54, 71, 2, 1, 153],
    [54, 74, 14, 1, 153],
    [54, 88, 17, 1, 136],
    [54, 105, 4, 1, 119],
    [54, 109, 1, 1, 136],
    [54, 110, 9, 1, 119],
    [54, 119, 2, 1, 102],
    [54, 121, 2, 1, 119],
    [54, 123, 12, 1, 102],
    [54, 135, 1, 1, 85],
    [54, 136, 3, 1, 102],
    [54, 142, 3, 1, 85],
    [54, 145, 1, 2, 102],
    [54, 146, 12, 1, 85],
    [55, 2, 23, 3, 187],
    [55, 25, 1, 1, 170],
    [55, 26, 4, 1, 187],
    [55, 30, 4, 1, 170],
    [55, 34, 3, 1, 187],
    [55, 37, 29, 1, 170],
    [55, 66, 2, 1, 153],
    [55, 68, 1, 1, 170],
    [55, 69, 3, 1, 153],
    [55, 72, 1, 1, 170],
    [55, 73, 15, 1, 153],
    [55, 88, 19, 1, 136],
    [55, 107, 12, 1, 119],
    [55, 119, 1, 1, 102],
    [55, 120, 2, 1, 119],
    [55, 122, 10, 1, 102],
    [55, 132, 1, 1, 85],
    [55, 133, 3, 1, 102],
    [55, 136, 1, 1, 85],
    [55, 137, 1, 1, 102],
    [55, 138, 2, 1, 85],
    [55, 140, 1, 1, 102],
    [55, 141, 4, 1, 85],
    [55, 146, 6, 1, 85],
    [55, 152, 1, 1, 102],
    [55, 153, 5, 1, 85],
    [56, 25, 46, 1, 170],
    [56, 71, 13, 1, 153],
    [56, 84, 4, 1, 136],
    [56, 88, 1, 1, 153],
    [56, 89, 1, 1, 136],
    [56, 90, 1, 1, 153],
    [56, 91, 12, 1, 136],
    [56, 103, 2, 1, 119],
    [56, 105, 1, 1, 136],
    [56, 106, 8, 1, 119],
    [56, 114, 1, 1, 102],
    [56, 115, 8, 1, 119],
    [56, 123, 17, 1, 102],
    [56, 140, 4, 1, 85],
    [56, 144, 1, 1, 102],
    [56, 145, 13, 1, 85],
    [57, 25, 43, 1, 170],
    [57, 68, 2, 1, 153],
    [57, 70, 1, 1, 170],
    [57, 71, 14, 1, 153],
    [57, 85, 1, 1, 136],
    [57, 86, 1, 1, 153],
    [57, 87, 15, 1, 136],
    [57, 102, 15, 1, 119],
    [57, 117, 1, 1, 102],
    [57, 118, 3, 1, 119],
    [57, 121, 16, 1, 102],
    [57, 137, 1, 2, 85],
    [57, 138, 2, 1, 102],
    [57, 140, 18, 1, 85],
    [58, 2, 24, 1, 187],
    [58, 26, 2, 1, 170],
    [58, 28, 1, 1, 187],
    [58, 29, 1, 1, 170],
    [58, 30, 3, 1, 187],
    [58, 33, 34, 1, 170],
    [58, 67, 19, 1, 153],
    [58, 86, 2, 1, 136],
    [58, 88, 1, 1, 153],
    [58, 89, 10, 1, 136],
    [58, 99, 1, 1, 119],
    [58, 100, 1, 1, 136],
    [58, 101, 13, 1, 119],
    [58, 114, 2, 1, 102],
    [58, 116, 3, 1, 119],
    [58, 119, 18, 1, 102],
    [58, 138, 1, 1, 102],
    [58, 139, 4, 1, 85],
    [58, 143, 1, 1, 102],
    [58, 144, 14, 1, 85],
    [59, 2, 23, 1, 187],
    [59, 25, 3, 1, 170],
    [59, 28, 6, 1, 187],
    [59, 34, 30, 1, 170],
    [59, 64, 2, 1, 153],
    [59, 66, 2, 1, 170],
    [59, 68, 15, 1, 153],
    [59, 83, 18, 1, 136],
    [59, 101, 14, 1, 119],
    [59, 115, 3, 1, 102],
    [59, 118, 3, 1, 119],
    [59, 121, 10, 1, 102],
    [59, 131, 2, 1, 85],
    [59, 133, 5, 1, 102],
    [59, 138, 6, 1, 85],
    [59, 144, 1, 1, 102],
    [59, 145, 13, 1, 85],
    [60, 2, 15, 4, 187],
    [60, 17, 1, 2, 170],
    [60, 18, 4, 2, 187],
    [60, 22, 1, 1, 170],
    [60, 23, 3, 1, 187],
    [60, 26, 4, 2, 170],
    [60, 30, 1, 1, 187],
    [60, 31, 2, 1, 170],
    [60, 33, 1, 2, 187],
    [60, 34, 27, 1, 170],
    [60, 61, 1, 1, 153],
    [60, 62, 2, 2, 170],
    [60, 64, 19, 1, 153],
    [60, 83, 12, 1, 136],
    [60, 95, 1, 1, 119],
    [60, 96, 2, 1, 136],
    [60, 98, 1, 1, 119],
    [60, 99, 3, 1, 136],
    [60, 102, 2, 1, 119],
    [60, 104, 1, 1, 136],
    [60, 105, 11, 1, 119],
    [60, 116, 20, 1, 102],
    [60, 136, 1, 1, 85],
    [60, 137, 1, 1, 102],
    [60, 138, 2, 1, 85],
    [60, 140, 1, 1, 102],
    [60, 141, 2, 1, 85],
    [60, 143, 1, 1, 102],
    [60, 144, 14, 1, 85],
    [61, 22, 2, 1, 170],
    [61, 24, 2, 1, 187],
    [61, 30, 2, 1, 187],
    [61, 32, 1, 1, 170],
    [61, 34, 26, 1, 170],
    [61, 60, 2, 1, 153],
    [61, 64, 20, 1, 153],
    [61, 84, 16, 1, 136],
    [61, 100, 14, 1, 119],
    [61, 114, 2, 1, 102],
    [61, 116, 1, 1, 119],
    [61, 117, 14, 1, 102],
    [61, 131, 2, 1, 85],
    [61, 133, 2, 1, 102],
    [61, 135, 1, 1, 85],
    [61, 136, 1, 1, 102],
    [61, 137, 15, 1, 85],
    [61, 152, 1, 1, 68],
    [61, 153, 5, 1, 85],
    [62, 17, 3, 2, 170],
    [62, 20, 3, 1, 187],
    [62, 23, 1, 1, 170],
    [62, 24, 3, 2, 187],
    [62, 27, 4, 2, 170],
    [62, 31, 1, 2, 187],
    [62, 32, 30, 1, 170],
    [62, 62, 1, 1, 153],
    [62, 63, 1, 1, 170],
    [62, 64, 1, 1, 153],
    [62, 65, 1, 1, 170],
    [62, 66, 13, 1, 153],
    [62, 79, 1, 1, 136],
    [62, 80, 2, 2, 153],
    [62, 82, 1, 1, 136],
    [62, 83, 1, 1, 153],
    [62, 84, 13, 1, 136],
    [62, 97, 16, 1, 119],
    [62, 113, 1, 1, 102],
    [62, 114, 1, 1, 119],
    [62, 115, 2, 1, 102],
    [62, 117, 1, 1, 119],
    [62, 118, 15, 1, 102],
    [62, 133, 1, 1, 85],
    [62, 134, 3, 1, 102],
    [62, 137, 19, 1, 85],
    [62, 156, 1, 1, 68],
    [62, 157, 1, 1, 85],
    [63, 20, 2, 1, 187],
    [63, 22, 2, 1, 170],
    [63, 32, 26, 1, 170],
    [63, 58, 1, 1, 153],
    [63, 59, 1, 1, 170],
    [63, 60, 18, 1, 153],
    [63, 78, 2, 2, 136],
    [63, 82, 14, 1, 136],
    [63, 96, 1, 1, 119],
    [63, 97, 1, 1, 136],
    [63, 98, 14, 1, 119],
    [63, 112, 13, 1, 102],
    [63, 125, 1, 1, 85],
    [63, 126, 4, 1, 102],
    [63, 130, 1, 2, 85],
    [63, 131, 2, 2, 102],
    [63, 133, 21, 1, 85],
    [63, 154, 1, 1, 68],
    [63, 155, 3, 1, 85],
    [64, 2, 13, 1, 187],
    [64, 15, 1, 1, 170],
    [64, 16, 4, 1, 187],
    [64, 20, 4, 1, 170],
    [64, 24, 1, 1, 187],
    [64, 25, 33, 1, 170],
    [64, 58, 2, 1, 153],
    [64, 60, 3, 1, 170],
    [64, 63, 15, 1, 153],
    [64, 80, 1, 1, 153],
    [64, 81, 13, 1, 136],
    [64, 94, 1, 1, 119],
    [64, 95, 1, 1, 136],
    [64, 96, 14, 1, 119],
    [64, 110, 1, 1, 102],
    [64, 111, 1, 1, 119],
    [64, 112, 2, 1, 102],
    [64, 114, 1, 1, 119],
    [64, 115, 11, 1, 102],
    [64, 126, 1, 1, 85],
    [64, 127, 3, 1, 102],
    [64, 133, 22, 1, 85],
    [64, 155, 1, 1, 68],
    [64, 156, 2, 1, 85],
    [65, 2, 5, 1, 187],
    [65, 7, 1, 1, 170],
    [65, 8, 4, 1, 187],
    [65, 12, 5, 1, 170],
    [65, 17, 3, 1, 187],
    [65, 20, 6, 1, 170],
    [65, 26, 1, 1, 187],
    [65, 27, 34, 1, 170],
    [65, 61, 15, 1, 153],
    [65, 76, 16, 1, 136],
    [65, 92, 2, 1, 119],
    [65, 94, 1, 1, 136],
    [65, 95, 16, 1, 119],
    [65, 111, 1, 1, 102],
    [65, 112, 2, 1, 119],
    [65, 114, 14, 1, 102],
    [65, 128, 2, 1, 85],
    [65, 130, 2, 1, 102],
    [65, 132, 2, 1, 85],
    [65, 134, 1, 1, 102],
    [65, 135, 19, 1, 85],
    [65, 154, 3, 1, 68],
    [65, 157, 1, 1, 85],
    [66, 2, 19, 1, 187],
    [66, 21, 3, 1, 170],
    [66, 24, 1, 1, 187],
    [66, 25, 3, 1, 170],
    [66, 28, 1, 1, 187],
    [66, 29, 31, 1, 170],
    [66, 60, 2, 1, 153],
    [66, 62, 2, 1, 170],
    [66, 64, 14, 1, 153],
    [66, 78, 2, 1, 136],
    [66, 80, 1, 1, 153],
    [66, 81, 14, 1, 136],
    [66, 95, 13, 1, 119],
    [66, 108, 1, 1, 102],
    [66, 109, 2, 1, 119],
    [66, 111, 17, 1, 102],
    [66, 128, 1, 1, 85],
    [66, 129, 1, 1, 102],
    [66, 130, 1, 1, 85],
    [66, 131, 2, 1, 102],
    [66, 133, 3, 1, 85],
    [66, 136, 1, 1, 102],
    [66, 137, 21, 1, 85],
    [67, 2, 4, 1, 187],
    [67, 6, 3, 1, 170],
    [67, 9, 2, 1, 187],
    [67, 11, 2, 1, 170],
    [67, 13, 2, 1, 187],
    [67, 15, 2, 1, 170],
    [67, 17, 2, 1, 187],
    [67, 19, 18, 1, 170],
    [67, 37, 1, 1, 153],
    [67, 38, 3, 1, 170],
    [67, 41, 1, 1, 153],
    [67, 42, 3, 1, 170],
    [67, 45, 2, 1, 153],
    [67, 47, 2, 1, 170],
    [67, 49, 2, 1, 153],
    [67, 51, 2, 1, 170],
    [67, 53, 1, 1, 153],
    [67, 54, 1, 1, 136],
    [67, 55, 1, 1, 153],
    [67, 56, 1, 3, 170],
    [67, 57, 1, 1, 153],
    [67, 58, 1, 1, 136],
    [67, 59, 5, 1, 153],
    [67, 64, 1, 1, 170],
    [67, 65, 2, 1, 153],
    [67, 67, 1, 1, 136],
    [67, 68, 3, 1, 153],
    [67, 71, 1, 1, 136],
    [67, 72, 3, 1, 153],
    [67, 75, 2, 1, 136],
    [67, 77, 1, 3, 153],
    [67, 78, 6, 1, 136],
    [67, 84, 1, 1, 119],
    [67, 85, 3, 1, 136],
    [67, 88, 1, 1, 119],
    [67, 89, 1, 1, 136],
    [67, 90, 4, 1, 119],
    [67, 94, 2, 1, 136],
    [67, 96, 1, 1, 119],
    [67, 97, 1, 1, 102],
    [67, 98, 7, 1, 119],
    [67, 105, 1, 1, 102],
    [67, 106, 3, 1, 119],
    [67, 109, 14, 1, 102],
    [67, 123, 1, 1, 85],
    [67, 124, 2, 1, 102],
    [67, 126, 2, 1, 85],
    [67, 128, 2, 1, 102],
    [67, 130, 2, 1, 85],
    [67, 132, 1, 1, 102],
    [67, 133, 25, 1, 85],
    [68, 2, 1, 3, 187],
    [68, 3, 2, 2, 170],
    [68, 5, 1, 2, 204],
    [68, 6, 1, 1, 85],
    [68, 7, 1, 2, 0],
    [68, 8, 1, 2, 102],
    [68, 9, 1, 2, 204],
    [68, 10, 1, 1, 119],
    [68, 11, 1, 2, 0],
    [68, 12, 1, 2, 51],
    [68, 13, 1, 2, 204],
    [68, 14, 1, 1, 170],
    [68, 15, 2, 1, 17],
    [68, 17, 1, 2, 170],
    [68, 18, 1, 2, 187],
    [68, 19, 1, 1, 51],
    [68, 20, 1, 2, 0],
    [68, 21, 1, 2, 136],
    [68, 22, 1, 2, 204],
    [68, 23, 1, 2, 85],
    [68, 24, 1, 1, 17],
    [68, 25, 1, 2, 102],
    [68, 26, 1, 2, 204],
    [68, 27, 1, 1, 136],
    [68, 28, 1, 1, 17],
    [68, 29, 1, 2, 51],
    [68, 30, 2, 1, 170],
    [68, 32, 1, 1, 34],
    [68, 33, 1, 1, 17],
    [68, 34, 1, 2, 153],
    [68, 35, 1, 2, 187],
    [68, 36, 1, 2, 51],
    [68, 37, 1, 1, 17],
    [68, 38, 1, 2, 119],
    [68, 39, 1, 1, 187],
    [68, 40, 1, 1, 102],
    [68, 41, 1, 2, 0],
    [68, 42, 1, 1, 85],
    [68, 43, 1, 2, 187],
    [68, 44, 1, 1, 136],
    [68, 45, 1, 2, 17],
    [68, 46, 1, 2, 51],
    [68, 47, 1, 2, 170],
    [68, 48, 1, 2, 153],
    [68, 49, 1, 1, 34],
    [68, 50, 1, 1, 17],
    [68, 51, 1, 2, 136],
    [68, 52, 1, 2, 170],
    [68, 53, 1, 1, 68],
    [68, 54, 1, 2, 0],
    [68, 55, 1, 2, 102],
    [68, 57, 1, 1, 102],
    [68, 58, 1, 2, 0],
    [68, 59, 1, 2, 51],
    [68, 60, 1, 2, 170],
    [68, 61, 1, 1, 136],
    [68, 62, 2, 1, 17],
    [68, 64, 2, 2, 153],
    [68, 66, 1, 1, 34],
    [68, 67, 1, 2, 0],
    [68, 68, 1, 2, 119],
    [68, 69, 1, 2, 170],
    [68, 70, 1, 1, 68],
    [68, 71, 1, 2, 0],
    [68, 72, 1, 2, 85],
    [68, 73, 1, 2, 170],
    [68, 74, 1, 1, 102],
    [68, 75, 1, 2, 0],
    [68, 76, 1, 2, 51],
    [68, 78, 1, 2, 119],
    [68, 79, 2, 1, 17],
    [68, 81, 2, 1, 136],
    [68, 83, 1, 1, 51],
    [68, 84, 1, 2, 0],
    [68, 85, 1, 1, 85],
    [68, 86, 1, 2, 153],
    [68, 87, 1, 1, 68],
    [68, 88, 1, 2, 0],
    [68, 89, 1, 2, 51],
    [68, 90, 1, 2, 153],
    [68, 91, 1, 1, 102],
    [68, 92, 1, 2, 0],
    [68, 93, 1, 2, 34],
    [68, 94, 1, 2, 136],
    [68, 95, 1, 1, 119],
    [68, 96, 2, 1, 17],
    [68, 98, 1, 2, 102],
    [68, 99, 1, 2, 119],
    [68, 100, 1, 1, 51],
    [68, 101, 1, 2, 0],
    [68, 102, 1, 2, 68],
    [68, 103, 1, 2, 136],
    [68, 104, 1, 1, 68],
    [68, 105, 1, 2, 0],
    [68, 106, 1, 2, 51],
    [68, 107, 1, 2, 119],
    [68, 108, 1, 2, 85],
    [68, 109, 2, 1, 17],
    [68, 111, 1, 2, 119],
    [68, 112, 1, 2, 102],
    [68, 113, 1, 2, 17],
    [68, 114, 1, 2, 0],
    [68, 115, 1, 2, 85],
    [68, 116, 1, 2, 119],
    [68, 117, 1, 1, 51],
    [68, 118, 1, 2, 0],
    [68, 119, 1, 1, 51],
    [68, 120, 1, 1, 102],
    [68, 121, 1, 1, 68],
    [68, 122, 1, 2, 0],
    [68, 123, 1, 2, 34],
    [68, 124, 1, 1, 102],
    [68, 125, 1, 1, 85],
    [68, 126, 2, 1, 17],
    [68, 128, 1, 1, 85],
    [68, 129, 1, 1, 102],
    [68, 130, 1, 1, 34],
    [68, 131, 1, 2, 0],
    [68, 132, 1, 2, 68],
    [68, 133, 1, 2, 102],
    [68, 134, 1, 1, 51],
    [68, 135, 1, 2, 0],
    [68, 136, 1, 2, 51],
    [68, 137, 1, 2, 102],
    [68, 138, 1, 1, 68],
    [68, 139, 1, 2, 0],
    [68, 140, 1, 2, 17],
    [68, 141, 1, 1, 102],
    [68, 142, 1, 2, 68],
    [68, 143, 2, 1, 17],
    [68, 145, 1, 1, 68],
    [68, 146, 1, 1, 85],
    [68, 147, 1, 1, 34],
    [68, 148, 1, 2, 0],
    [68, 149, 1, 1, 51],
    [68, 150, 1, 1, 85],
    [68, 151, 1, 1, 51],
    [68, 152, 1, 2, 0],
    [68, 153, 1, 1, 34],
    [68, 154, 4, 1, 85],
    [69, 6, 1, 1, 68],
    [69, 10, 1, 1, 102],
    [69, 14, 1, 1, 153],
    [69, 15, 1, 1, 0],
    [69, 16, 1, 1, 17],
    [69, 19, 1, 1, 17],
    [69, 24, 1, 1, 0],
    [69, 27, 1, 1, 119],
    [69, 28, 1, 1, 0],
    [69, 30, 1, 1, 170],
    [69, 31, 1, 1, 153],
    [69, 32, 2, 1, 17],
    [69, 37, 1, 1, 0],
    [69, 39, 1, 1, 204],
    [69, 40, 1, 1, 85],
    [69, 42, 1, 1, 68],
    [69, 44, 1, 1, 119],
    [69, 49, 2, 1, 17],
    [69, 53, 1, 1, 51],
    [69, 57, 1, 1, 85],
    [69, 61, 1, 1, 119],
    [69, 62, 1, 1, 0],
    [69, 63, 1, 1, 17],
    [69, 66, 1, 1, 17],
    [69, 70, 1, 1, 51],
    [69, 74, 1, 1, 85],
    [69, 79, 1, 1, 0],
    [69, 80, 1, 1, 17],
    [69, 81, 1, 1, 119],
    [69, 82, 1, 1, 136],
    [69, 83, 1, 1, 17],
    [69, 85, 1, 1, 102],
    [69, 87, 1, 1, 51],
    [69, 91, 1, 1, 85],
    [69, 95, 1, 1, 102],
    [69, 96, 1, 1, 0],
    [69, 97, 1, 1, 17],
    [69, 100, 1, 1, 17],
    [69, 104, 1, 1, 51],
    [69, 109, 1, 1, 0],
    [69, 110, 1, 1, 17],
    [69, 117, 1, 1, 34],
    [69, 119, 1, 1, 68],
    [69, 120, 1, 1, 119],
    [69, 121, 1, 1, 51],
    [69, 124, 1, 1, 119],
    [69, 125, 1, 1, 68],
    [69, 126, 1, 1, 0],
    [69, 127, 1, 1, 17],
    [69, 128, 1, 2, 102],
    [69, 129, 1, 1, 85],
    [69, 130, 1, 1, 17],
    [69, 134, 1, 1, 34],
    [69, 138, 1, 1, 51],
    [69, 141, 1, 1, 85],
    [69, 143, 2, 1, 0],
    [69, 145, 2, 1, 85],
    [69, 147, 1, 1, 17],
    [69, 149, 1, 1, 68],
    [69, 150, 1, 1, 102],
    [69, 151, 1, 1, 34],
    [69, 153, 1, 1, 51],
    [69, 154, 2, 1, 85],
    [69, 156, 4, 1, 68],
    [70, 3, 1, 1, 170],
    [70, 4, 2, 2, 187],
    [70, 6, 1, 2, 170],
    [70, 7, 1, 1, 153],
    [70, 8, 1, 2, 170],
    [70, 9, 1, 2, 187],
    [70, 10, 1, 2, 170],
    [70, 11, 1, 1, 153],
    [70, 12, 1, 1, 170],
    [70, 13, 1, 2, 187],
    [70, 14, 6, 1, 170],
    [70, 20, 1, 1, 153],
    [70, 21, 3, 2, 170],
    [70, 24, 1, 1, 153],
    [70, 25, 3, 2, 170],
    [70, 28, 1, 1, 153],
    [70, 29, 3, 1, 170],
    [70, 32, 1, 1, 153],
    [70, 33, 4, 1, 170],
    [70, 37, 1, 1, 153],
    [70, 38, 3, 2, 170],
    [70, 41, 1, 1, 153],
    [70, 42, 3, 1, 170],
    [70, 45, 1, 1, 153],
    [70, 46, 3, 1, 170],
    [70, 49, 2, 1, 153],
    [70, 51, 2, 1, 170],
    [70, 53, 5, 1, 153],
    [70, 58, 1, 1, 136],
    [70, 59, 3, 1, 153],
    [70, 62, 1, 1, 136],
    [70, 63, 3, 1, 153],
    [70, 66, 2, 1, 136],
    [70, 68, 2, 1, 153],
    [70, 70, 2, 1, 136],
    [70, 72, 2, 1, 153],
    [70, 74, 1, 2, 136],
    [70, 75, 1, 1, 119],
    [70, 76, 3, 1, 136],
    [70, 79, 1, 1, 119],
    [70, 80, 3, 1, 136],
    [70, 83, 2, 1, 119],
    [70, 85, 2, 1, 136],
    [70, 87, 2, 1, 119],
    [70, 89, 3, 1, 136],
    [70, 92, 1, 1, 102],
    [70, 93, 3, 1, 119],
    [70, 96, 1, 2, 102],
    [70, 97, 4, 1, 119],
    [70, 101, 1, 1, 102],
    [70, 102, 2, 1, 119],
    [70, 104, 8, 1, 102],
    [70, 112, 1, 1, 119],
    [70, 113, 2, 1, 102],
    [70, 115, 1, 1, 119],
    [70, 116, 2, 1, 102],
    [70, 118, 1, 1, 85],
    [70, 119, 3, 1, 102],
    [70, 122, 1, 1, 85],
    [70, 123, 3, 1, 102],
    [70, 126, 2, 1, 85],
    [70, 129, 6, 1, 85],
    [70, 135, 1, 1, 68],
    [70, 136, 7, 1, 85],
    [70, 143, 1, 1, 68],
    [70, 144, 7, 1, 85],
    [70, 151, 2, 1, 68],
    [70, 153, 5, 1, 85],
    [70, 158, 2, 4, 68],
    [71, 2, 2, 1, 170],
    [71, 7, 1, 1, 136],
    [71, 11, 1, 1, 136],
    [71, 12, 1, 1, 153],
    [71, 14, 1, 1, 170],
    [71, 15, 2, 1, 153],
    [71, 17, 2, 10, 170],
    [71, 19, 1, 1, 153],
    [71, 20, 1, 1, 136],
    [71, 24, 1, 1, 136],
    [71, 28, 1, 1, 136],
    [71, 29, 1, 1, 153],
    [71, 30, 2, 1, 170],
    [71, 32, 2, 1, 136],
    [71, 34, 2, 1, 170],
    [71, 36, 1, 1, 153],
    [71, 37, 1, 1, 119],
    [71, 41, 1, 1, 119],
    [71, 42, 1, 1, 153],
    [71, 43, 2, 1, 170],
    [71, 45, 2, 1, 136],
    [71, 47, 2, 1, 170],
    [71, 49, 1, 1, 136],
    [71, 50, 1, 1, 119],
    [71, 51, 1, 1, 153],
    [71, 52, 1, 3, 170],
    [71, 53, 1, 1, 153],
    [71, 54, 1, 1, 119],
    [71, 55, 1, 1, 153],
    [71, 56, 1, 3, 170],
    [71, 57, 1, 1, 153],
    [71, 58, 1, 1, 119],
    [71, 59, 1, 1, 136],
    [71, 60, 2, 1, 153],
    [71, 62, 2, 1, 119],
    [71, 64, 2, 1, 153],
    [71, 66, 1, 1, 119],
    [71, 67, 1, 1, 102],
    [71, 68, 1, 1, 136],
    [71, 69, 1, 1, 153],
    [71, 70, 1, 1, 136],
    [71, 71, 1, 1, 102],
    [71, 72, 1, 1, 136],
    [71, 73, 1, 1, 153],
    [71, 75, 1, 1, 102],
    [71, 76, 1, 1, 119],
    [71, 77, 2, 1, 136],
    [71, 79, 2, 1, 102],
    [71, 81, 2, 1, 136],
    [71, 83, 1, 1, 119],
    [71, 84, 1, 1, 102],
    [71, 85, 1, 1, 119],
    [71, 86, 1, 1, 136],
    [71, 87, 1, 1, 119],
    [71, 88, 1, 1, 102],
    [71, 89, 1, 1, 119],
    [71, 90, 1, 3, 136],
    [71, 91, 1, 1, 119],
    [71, 92, 1, 1, 85],
    [71, 93, 1, 1, 102],
    [71, 94, 2, 1, 119],
    [71, 97, 1, 1, 85],
    [71, 98, 2, 1, 119],
    [71, 100, 1, 1, 102],
    [71, 101, 1, 1, 85],
    [71, 102, 1, 1, 102],
    [71, 103, 1, 1, 119],
    [71, 104, 1, 1, 102],
    [71, 105, 1, 1, 85],
    [71, 106, 1, 1, 102],
    [71, 107, 1, 3, 119],
    [71, 108, 1, 1, 102],
    [71, 109, 2, 1, 85],
    [71, 111, 2, 3, 102],
    [71, 113, 2, 1, 85],
    [71, 115, 3, 1, 102],
    [71, 118, 1, 1, 68],
    [71, 119, 1, 1, 85],
    [71, 120, 1, 1, 102],
    [71, 121, 1, 1, 85],
    [71, 122, 1, 1, 68],
    [71, 123, 1, 1, 85],
    [71, 124, 1, 3, 102],
    [71, 125, 1, 1, 85],
    [71, 126, 2, 1, 68],
    [71, 128, 3, 1, 85],
    [71, 131, 1, 1, 68],
    [71, 132, 3, 1, 85],
    [71, 135, 2, 1, 68],
    [71, 137, 2, 1, 85],
    [71, 139, 2, 1, 68],
    [71, 141, 2, 1, 85],
    [71, 143, 2, 1, 68],
    [71, 145, 3, 1, 85],
    [71, 148, 2, 1, 68],
    [71, 150, 1, 3, 85],
    [71, 151, 3, 1, 68],
    [71, 154, 4, 1, 85],
    [72, 2, 3, 2, 170],
    [72, 5, 1, 2, 204],
    [72, 6, 1, 1, 51],
    [72, 7, 1, 2, 0],
    [72, 8, 1, 1, 85],
    [72, 9, 1, 2, 204],
    [72, 10, 1, 1, 102],
    [72, 11, 1, 1, 0],
    [72, 12, 1, 1, 51],
    [72, 13, 1, 1, 204],
    [72, 14, 1, 2, 153],
    [72, 15, 2, 1, 0],
    [72, 19, 1, 1, 17],
    [72, 20, 1, 1, 0],
    [72, 21, 1, 1, 119],
    [72, 22, 1, 2, 204],
    [72, 23, 1, 1, 68],
    [72, 24, 1, 1, 0],
    [72, 25, 1, 1, 85],
    [72, 26, 1, 2, 204],
    [72, 27, 1, 1, 119],
    [72, 28, 1, 1, 0],
    [72, 29, 1, 1, 51],
    [72, 30, 1, 2, 170],
    [72, 31, 1, 2, 153],
    [72, 32, 2, 1, 17],
    [72, 34, 1, 2, 153],
    [72, 35, 1, 2, 170],
    [72, 36, 1, 1, 51],
    [72, 37, 1, 1, 0],
    [72, 38, 1, 1, 102],
    [72, 39, 1, 1, 204],
    [72, 40, 1, 1, 85],
    [72, 41, 1, 1, 0],
    [72, 42, 1, 1, 68],
    [72, 43, 1, 1, 187],
    [72, 44, 1, 1, 119],
    [72, 45, 1, 1, 0],
    [72, 46, 1, 1, 34],
    [72, 47, 1, 2, 170],
    [72, 48, 1, 2, 153],
    [72, 49, 1, 1, 17],
    [72, 50, 1, 1, 0],
    [72, 51, 1, 1, 119],
    [72, 53, 1, 1, 51],
    [72, 54, 1, 1, 0],
    [72, 55, 1, 1, 85],
    [72, 57, 1, 1, 85],
    [72, 58, 1, 1, 0],
    [72, 59, 1, 1, 51],
    [72, 60, 1, 2, 170],
    [72, 61, 1, 2, 119],
    [72, 62, 1, 1, 0],
    [72, 63, 1, 1, 17],
    [72, 64, 1, 1, 136],
    [72, 65, 1, 1, 153],
    [72, 66, 1, 1, 17],
    [72, 67, 1, 1, 0],
    [72, 68, 1, 1, 102],
    [72, 69, 1, 2, 170],
    [72, 70, 1, 1, 51],
    [72, 71, 1, 1, 0],
    [72, 72, 1, 1, 68],
    [72, 73, 1, 1, 170],
    [72, 74, 1, 2, 85],
    [72, 75, 1, 1, 0],
    [72, 76, 1, 1, 17],
    [72, 77, 1, 2, 153],
    [72, 78, 1, 2, 119],
    [72, 79, 2, 1, 0],
    [72, 81, 1, 2, 119],
    [72, 82, 1, 2, 136],
    [72, 83, 1, 1, 17],
    [72, 84, 1, 1, 0],
    [72, 85, 1, 1, 85],
    [72, 86, 1, 2, 153],
    [72, 87, 1, 1, 51],
    [72, 88, 1, 1, 0],
    [72, 89, 1, 1, 51],
    [72, 91, 1, 1, 85],
    [72, 92, 1, 1, 0],
    [72, 93, 1, 1, 17],
    [72, 94, 1, 2, 119],
    [72, 95, 1, 2, 102],
    [72, 96, 2, 1, 0],
    [72, 98, 1, 1, 102],
    [72, 99, 1, 1, 119],
    [72, 100, 1, 1, 17],
    [72, 101, 1, 1, 0],
    [72, 102, 1, 1, 68],
    [72, 103, 1, 1, 136],
    [72, 104, 1, 1, 51],
    [72, 105, 1, 2, 0],
    [72, 106, 1, 1, 34],
    [72, 108, 1, 2, 85],
    [72, 109, 2, 1, 0],
    [72, 113, 1, 1, 17],
    [72, 114, 1, 1, 0],
    [72, 115, 1, 2, 85],
    [72, 116, 1, 1, 119],
    [72, 117, 1, 1, 34],
    [72, 118, 1, 1, 0],
    [72, 119, 1, 1, 51],
    [72, 120, 1, 1, 119],
    [72, 121, 1, 1, 51],
    [72, 122, 1, 2, 0],
    [72, 123, 1, 1, 17],
    [72, 125, 1, 1, 68],
    [72, 126, 2, 1, 0],
    [72, 128, 2, 1, 85],
    [72, 130, 1, 1, 17],
    [72, 131, 1, 1, 0],
    [72, 132, 1, 1, 68],
    [72, 133, 1, 2, 102],
    [72, 134, 1, 2, 51],
    [72, 135, 1, 1, 0],
    [72, 136, 1, 1, 34],
    [72, 137, 1, 2, 102],
    [72, 138, 1, 1, 51],
    [72, 139, 1, 1, 0],
    [72, 140, 1, 1, 17],
    [72, 141, 1, 2, 85],
    [72, 142, 1, 2, 68],
    [72, 143, 2, 1, 0],
    [72, 145, 1, 1, 68],
    [72, 146, 1, 1, 85],
    [72, 147, 1, 1, 17],
    [72, 148, 1, 1, 0],
    [72, 149, 1, 1, 51],
    [72, 151, 1, 2, 51],
    [72, 152, 1, 2, 0],
    [72, 153, 1, 1, 34],
    [72, 154, 1, 2, 85],
    [72, 155, 1, 3, 68],
    [72, 156, 2, 2, 85],
    [73, 6, 1, 1, 85],
    [73, 8, 1, 1, 119],
    [73, 10, 1, 1, 119],
    [73, 11, 1, 1, 17],
    [73, 12, 1, 1, 68],
    [73, 13, 1, 1, 187],
    [73, 15, 1, 1, 17],
    [73, 16, 1, 1, 51],
    [73, 19, 1, 1, 51],
    [73, 20, 1, 1, 17],
    [73, 21, 1, 1, 136],
    [73, 23, 1, 1, 102],
    [73, 24, 1, 1, 17],
    [73, 25, 1, 1, 102],
    [73, 27, 1, 1, 136],
    [73, 28, 1, 1, 34],
    [73, 29, 1, 1, 85],
    [73, 32, 2, 1, 51],
    [73, 36, 1, 1, 68],
    [73, 37, 1, 1, 34],
    [73, 38, 1, 1, 136],
    [73, 39, 1, 1, 187],
    [73, 40, 1, 1, 102],
    [73, 41, 1, 1, 17],
    [73, 42, 1, 1, 102],
    [73, 43, 1, 1, 170],
    [73, 44, 1, 1, 136],
    [73, 45, 1, 1, 17],
    [73, 46, 1, 1, 51],
    [73, 49, 2, 1, 51],
    [73, 51, 1, 1, 136],
    [73, 53, 1, 1, 68],
    [73, 54, 1, 1, 17],
    [73, 55, 1, 1, 102],
    [73, 57, 1, 1, 102],
    [73, 58, 1, 1, 17],
    [73, 59, 1, 1, 85],
    [73, 62, 1, 1, 17],
    [73, 63, 1, 1, 51],
    [73, 64, 2, 1, 153],
    [73, 66, 1, 1, 51],
    [73, 67, 1, 1, 17],
    [73, 68, 1, 1, 119],
    [73, 70, 1, 1, 68],
    [73, 71, 1, 1, 17],
    [73, 72, 1, 1, 85],
    [73, 73, 1, 1, 153],
    [73, 75, 1, 1, 17],
    [73, 76, 1, 1, 68],
    [73, 79, 1, 1, 17],
    [73, 80, 1, 1, 34],
    [73, 83, 1, 1, 51],
    [73, 84, 1, 1, 17],
    [73, 85, 1, 1, 102],
    [73, 87, 1, 1, 68],
    [73, 88, 1, 1, 17],
    [73, 89, 1, 1, 68],
    [73, 91, 1, 1, 102],
    [73, 92, 1, 1, 17],
    [73, 93, 1, 1, 51],
    [73, 96, 2, 1, 17],
    [73, 98, 2, 1, 119],
    [73, 100, 1, 1, 51],
    [73, 101, 1, 1, 17],
    [73, 102, 1, 1, 85],
    [73, 103, 1, 1, 119],
    [73, 104, 1, 1, 68],
    [73, 106, 1, 1, 51],
    [73, 109, 1, 1, 17],
    [73, 110, 1, 1, 34],
    [73, 113, 2, 1, 17],
    [73, 116, 1, 1, 102],
    [73, 117, 1, 1, 51],
    [73, 118, 1, 1, 17],
    [73, 119, 1, 1, 68],
    [73, 120, 1, 1, 102],
    [73, 121, 1, 1, 68],
    [73, 123, 1, 1, 51],
    [73, 125, 1, 1, 85],
    [73, 126, 2, 1, 17],
    [73, 128, 1, 1, 102],
    [73, 129, 1, 1, 85],
    [73, 130, 2, 1, 17],
    [73, 132, 1, 1, 85],
    [73, 135, 1, 1, 17],
    [73, 136, 1, 1, 51],
    [73, 138, 1, 1, 68],
    [73, 139, 1, 1, 17],
    [73, 140, 1, 1, 51],
    [73, 143, 2, 1, 17],
    [73, 145, 2, 1, 85],
    [73, 147, 2, 1, 17],
    [73, 149, 1, 1, 68],
    [73, 153, 1, 1, 51],
    [74, 2, 2, 1, 170],
    [74, 4, 2, 1, 187],
    [74, 6, 2, 1, 204],
    [74, 8, 1, 1, 187],
    [74, 9, 1, 1, 170],
    [74, 10, 3, 1, 187],
    [74, 13, 2, 1, 170],
    [74, 15, 2, 1, 187],
    [74, 19, 3, 1, 187],
    [74, 22, 1, 1, 170],
    [74, 23, 2, 1, 187],
    [74, 25, 3, 1, 170],
    [74, 28, 2, 1, 187],
    [74, 30, 22, 1, 170],
    [74, 52, 1, 1, 153],
    [74, 53, 3, 1, 170],
    [74, 56, 2, 1, 153],
    [74, 58, 2, 1, 170],
    [74, 60, 2, 1, 153],
    [74, 62, 2, 1, 170],
    [74, 64, 9, 1, 153],
    [74, 73, 2, 1, 136],
    [74, 75, 2, 1, 153],
    [74, 77, 2, 2, 136],
    [74, 79, 2, 1, 153],
    [74, 81, 9, 1, 136],
    [74, 90, 2, 1, 119],
    [74, 92, 2, 1, 136],
    [74, 94, 3, 1, 119],
    [74, 97, 1, 1, 136],
    [74, 98, 5, 1, 119],
    [74, 103, 1, 1, 102],
    [74, 104, 3, 1, 119],
    [74, 107, 2, 1, 102],
    [74, 109, 2, 1, 119],
    [74, 111, 9, 1, 102],
    [74, 120, 1, 1, 85],
    [74, 121, 3, 1, 102],
    [74, 124, 1, 1, 85],
    [74, 125, 3, 1, 102],
    [74, 128, 3, 1, 85],
    [74, 131, 1, 1, 102],
    [74, 132, 3, 1, 85],
    [74, 135, 2, 1, 102],
    [74, 137, 2, 2, 85],
    [74, 139, 1, 1, 102],
    [74, 140, 15, 1, 85],
    [74, 156, 1, 1, 85],
    [74, 157, 3, 1, 68],
    [75, 2, 3, 4, 170],
    [75, 5, 1, 1, 187],
    [75, 6, 1, 1, 136],
    [75, 7, 1, 1, 85],
    [75, 8, 1, 1, 153],
    [75, 9, 1, 4, 204],
    [75, 10, 1, 1, 153],
    [75, 11, 1, 1, 85],
    [75, 12, 1, 1, 119],
    [75, 13, 1, 4, 187],
    [75, 14, 1, 1, 170],
    [75, 15, 2, 1, 102],
    [75, 19, 1, 1, 119],
    [75, 20, 1, 1, 85],
    [75, 21, 1, 1, 153],
    [75, 22, 1, 1, 187],
    [75, 23, 1, 1, 136],
    [75, 24, 1, 1, 85],
    [75, 25, 1, 1, 136],
    [75, 26, 1, 1, 170],
    [75, 27, 1, 1, 153],
    [75, 28, 1, 1, 85],
    [75, 29, 1, 1, 119],
    [75, 30, 2, 1, 170],
    [75, 32, 1, 1, 102],
    [75, 33, 1, 1, 85],
    [75, 34, 2, 1, 170],
    [75, 36, 1, 1, 119],
    [75, 37, 1, 1, 68],
    [75, 38, 1, 1, 136],
    [75, 39, 1, 1, 170],
    [75, 40, 1, 1, 136],
    [75, 41, 1, 1, 68],
    [75, 42, 1, 1, 119],
    [75, 43, 1, 4, 170],
    [75, 44, 1, 1, 153],
    [75, 45, 1, 1, 85],
    [75, 46, 1, 1, 102],
    [75, 47, 1, 4, 170],
    [75, 48, 1, 4, 153],
    [75, 49, 1, 1, 102],
    [75, 50, 1, 1, 85],
    [75, 51, 1, 1, 153],
    [75, 52, 1, 4, 170],
    [75, 53, 1, 1, 119],
    [75, 54, 1, 1, 68],
    [75, 55, 1, 1, 136],
    [75, 56, 1, 4, 170],
    [75, 57, 1, 1, 119],
    [75, 58, 1, 1, 68],
    [75, 59, 1, 1, 102],
    [75, 60, 1, 1, 153],
    [75, 61, 1, 1, 136],
    [75, 62, 1, 1, 68],
    [75, 63, 1, 1, 85],
    [75, 64, 2, 1, 153],
    [75, 66, 1, 1, 85],
    [75, 67, 1, 1, 68],
    [75, 68, 1, 1, 136],
    [75, 69, 1, 4, 153],
    [75, 70, 1, 1, 102],
    [75, 71, 1, 1, 51],
    [75, 72, 1, 1, 102],
    [75, 73, 1, 4, 153],
    [75, 74, 1, 1, 119],
    [75, 75, 1, 1, 68],
    [75, 76, 1, 1, 85],
    [75, 79, 2, 1, 68],
    [75, 81, 1, 3, 119],
    [75, 82, 1, 3, 136],
    [75, 83, 1, 1, 85],
    [75, 84, 1, 1, 51],
    [75, 85, 1, 1, 102],
    [75, 86, 1, 4, 136],
    [75, 87, 1, 1, 102],
    [75, 88, 1, 1, 51],
    [75, 89, 1, 1, 85],
    [75, 90, 1, 4, 136],
    [75, 91, 1, 1, 119],
    [75, 92, 1, 1, 51],
    [75, 93, 1, 1, 68],
    [75, 94, 2, 1, 119],
    [75, 96, 1, 1, 68],
    [75, 97, 1, 1, 51],
    [75, 98, 1, 4, 102],
    [75, 99, 1, 4, 119],
    [75, 100, 1, 1, 85],
    [75, 101, 1, 1, 51],
    [75, 102, 1, 1, 85],
    [75, 103, 1, 4, 119],
    [75, 104, 1, 1, 102],
    [75, 105, 1, 1, 51],
    [75, 106, 1, 1, 68],
    [75, 107, 1, 4, 119],
    [75, 108, 1, 1, 102],
    [75, 109, 2, 1, 51],
    [75, 111, 2, 2, 102],
    [75, 113, 1, 1, 68],
    [75, 114, 1, 1, 51],
    [75, 115, 1, 2, 85],
    [75, 116, 1, 3, 102],
    [75, 117, 1, 1, 85],
    [75, 118, 1, 1, 51],
    [75, 119, 1, 1, 68],
    [75, 120, 1, 4, 102],
    [75, 121, 1, 1, 85],
    [75, 122, 2, 1, 51],
    [75, 124, 2, 1, 85],
    [75, 126, 2, 1, 51],
    [75, 128, 1, 1, 102],
    [75, 129, 1, 1, 85],
    [75, 130, 1, 1, 68],
    [75, 131, 1, 1, 51],
    [75, 132, 2, 1, 85],
    [75, 134, 1, 1, 68],
    [75, 135, 1, 1, 51],
    [75, 136, 1, 1, 68],
    [75, 139, 2, 1, 51],
    [75, 141, 2, 1, 85],
    [75, 143, 2, 1, 51],
    [75, 145, 1, 3, 68],
    [75, 146, 1, 3, 85],
    [75, 147, 2, 1, 51],
    [75, 149, 1, 1, 68],
    [75, 150, 1, 1, 85],
    [75, 151, 1, 1, 68],
    [75, 152, 2, 1, 51],
    [75, 154, 4, 1, 85],
    [75, 158, 2, 2, 68],
    [76, 5, 1, 1, 204],
    [76, 6, 1, 2, 51],
    [76, 7, 1, 2, 0],
    [76, 8, 1, 2, 85],
    [76, 10, 1, 2, 102],
    [76, 11, 1, 2, 0],
    [76, 12, 1, 2, 51],
    [76, 14, 1, 2, 153],
    [76, 15, 1, 2, 0],
    [76, 16, 1, 2, 17],
    [76, 19, 1, 2, 17],
    [76, 20, 1, 2, 0],
    [76, 21, 1, 2, 119],
    [76, 22, 1, 2, 204],
    [76, 23, 1, 2, 68],
    [76, 24, 1, 2, 0],
    [76, 25, 1, 2, 85],
    [76, 26, 1, 2, 204],
    [76, 27, 1, 2, 119],
    [76, 28, 1, 2, 0],
    [76, 29, 1, 2, 51],
    [76, 30, 1, 2, 170],
    [76, 31, 1, 2, 153],
    [76, 32, 2, 2, 17],
    [76, 34, 1, 3, 153],
    [76, 35, 1, 3, 170],
    [76, 36, 1, 2, 51],
    [76, 37, 1, 1, 0],
    [76, 38, 1, 2, 102],
    [76, 39, 1, 2, 187],
    [76, 40, 1, 2, 68],
    [76, 41, 1, 2, 0],
    [76, 42, 1, 2, 68],
    [76, 44, 1, 2, 119],
    [76, 45, 1, 2, 0],
    [76, 46, 1, 1, 17],
    [76, 49, 1, 1, 17],
    [76, 50, 1, 1, 0],
    [76, 51, 1, 2, 119],
    [76, 53, 1, 2, 51],
    [76, 54, 1, 2, 0],
    [76, 55, 1, 2, 85],
    [76, 57, 1, 2, 85],
    [76, 58, 1, 2, 0],
    [76, 59, 1, 2, 51],
    [76, 60, 1, 2, 170],
    [76, 61, 1, 2, 119],
    [76, 62, 1, 2, 0],
    [76, 63, 1, 2, 17],
    [76, 64, 1, 1, 136],
    [76, 65, 1, 1, 153],
    [76, 66, 1, 2, 17],
    [76, 67, 1, 2, 0],
    [76, 68, 1, 2, 102],
    [76, 70, 1, 2, 51],
    [76, 71, 1, 2, 0],
    [76, 72, 1, 2, 68],
    [76, 74, 1, 2, 85],
    [76, 75, 1, 2, 0],
    [76, 76, 1, 2, 34],
    [76, 77, 1, 3, 136],
    [76, 78, 1, 1, 119],
    [76, 79, 2, 1, 0],
    [76, 83, 1, 2, 17],
    [76, 84, 1, 2, 0],
    [76, 85, 1, 2, 85],
    [76, 87, 1, 2, 51],
    [76, 88, 1, 2, 0],
    [76, 89, 1, 2, 51],
    [76, 91, 1, 2, 85],
    [76, 92, 1, 2, 0],
    [76, 93, 1, 2, 17],
    [76, 94, 1, 3, 119],
    [76, 95, 1, 3, 102],
    [76, 96, 2, 2, 0],
    [76, 100, 1, 2, 17],
    [76, 101, 1, 2, 0],
    [76, 102, 1, 1, 51],
    [76, 104, 1, 2, 51],
    [76, 105, 1, 2, 0],
    [76, 106, 1, 1, 34],
    [76, 108, 1, 1, 85],
    [76, 109, 1, 2, 0],
    [76, 110, 1, 2, 17],
    [76, 113, 1, 2, 17],
    [76, 114, 1, 2, 0],
    [76, 117, 1, 2, 17],
    [76, 118, 1, 2, 0],
    [76, 119, 1, 2, 51],
    [76, 121, 1, 2, 51],
    [76, 122, 1, 2, 0],
    [76, 123, 1, 2, 17],
    [76, 124, 1, 3, 102],
    [76, 125, 1, 2, 68],
    [76, 126, 2, 2, 0],
    [76, 128, 2, 11, 85],
    [76, 130, 1, 2, 17],
    [76, 131, 1, 2, 0],
    [76, 132, 1, 2, 68],
    [76, 133, 1, 3, 102],
    [76, 134, 1, 2, 34],
    [76, 135, 1, 2, 0],
    [76, 136, 1, 2, 51],
    [76, 137, 1, 2, 102],
    [76, 138, 1, 2, 51],
    [76, 139, 1, 2, 0],
    [76, 140, 1, 2, 17],
    [76, 141, 1, 3, 85],
    [76, 142, 1, 3, 68],
    [76, 143, 2, 2, 0],
    [76, 147, 1, 2, 17],
    [76, 148, 1, 2, 0],
    [76, 149, 1, 2, 51],
    [76, 150, 1, 1, 102],
    [76, 151, 1, 2, 34],
    [76, 152, 1, 2, 0],
    [76, 153, 1, 2, 34],
    [76, 154, 1, 3, 85],
    [76, 155, 1, 1, 68],
    [76, 156, 2, 1, 85],
    [77, 5, 1, 2, 187],
    [77, 37, 1, 1, 17],
    [77, 46, 1, 1, 51],
    [77, 49, 2, 1, 17],
    [77, 64, 2, 1, 136],
    [77, 78, 1, 1, 102],
    [77, 79, 1, 1, 0],
    [77, 80, 1, 1, 17],
    [77, 102, 1, 1, 68],
    [77, 106, 1, 1, 17],
    [77, 108, 1, 1, 68],
    [77, 111, 1, 1, 102],
    [77, 112, 1, 1, 85],
    [77, 115, 1, 1, 68],
    [77, 150, 1, 2, 85],
    [77, 155, 5, 1, 68],
    [78, 6, 1, 1, 102],
    [78, 7, 1, 1, 34],
    [78, 8, 1, 1, 119],
    [78, 10, 1, 1, 136],
    [78, 11, 1, 1, 34],
    [78, 12, 1, 1, 102],
    [78, 14, 1, 1, 170],
    [78, 15, 1, 1, 51],
    [78, 16, 1, 1, 68],
    [78, 19, 1, 1, 68],
    [78, 20, 1, 1, 51],
    [78, 21, 1, 1, 136],
    [78, 22, 1, 1, 187],
    [78, 23, 1, 1, 102],
    [78, 24, 1, 1, 51],
    [78, 25, 1, 1, 119],
    [78, 26, 1, 1, 187],
    [78, 27, 1, 1, 136],
    [78, 28, 1, 1, 51],
    [78, 29, 1, 1, 85],
    [78, 30, 2, 1, 170],
    [78, 32, 2, 1, 68],
    [78, 36, 1, 1, 85],
    [78, 37, 1, 1, 51],
    [78, 38, 1, 1, 136],
    [78, 39, 1, 1, 170],
    [78, 40, 1, 1, 119],
    [78, 41, 1, 1, 51],
    [78, 42, 1, 1, 102],
    [78, 44, 1, 1, 136],
    [78, 45, 1, 1, 51],
    [78, 46, 1, 1, 85],
    [78, 49, 1, 1, 68],
    [78, 50, 1, 1, 51],
    [78, 51, 1, 1, 136],
    [78, 53, 1, 1, 85],
    [78, 54, 1, 1, 51],
    [78, 55, 1, 1, 119],
    [78, 57, 1, 1, 102],
    [78, 58, 1, 1, 51],
    [78, 59, 1, 1, 85],
    [78, 60, 1, 1, 153],
    [78, 61, 1, 1, 136],
    [78, 62, 1, 1, 51],
    [78, 63, 1, 1, 68],
    [78, 64, 1, 2, 153],
    [78, 65, 1, 2, 136],
    [78, 66, 2, 1, 51],
    [78, 68, 1, 1, 119],
    [78, 70, 1, 1, 85],
    [78, 71, 1, 1, 34],
    [78, 72, 1, 1, 102],
    [78, 74, 1, 1, 102],
    [78, 75, 1, 1, 34],
    [78, 76, 1, 1, 68],
    [78, 78, 1, 1, 119],
    [78, 79, 2, 1, 51],
    [78, 81, 2, 1, 136],
    [78, 83, 2, 1, 51],
    [78, 85, 1, 1, 102],
    [78, 87, 1, 1, 68],
    [78, 88, 1, 1, 34],
    [78, 89, 1, 1, 85],
    [78, 91, 1, 1, 102],
    [78, 92, 1, 1, 34],
    [78, 93, 1, 1, 68],
    [78, 96, 2, 1, 51],
    [78, 100, 1, 1, 51],
    [78, 101, 1, 1, 34],
    [78, 102, 1, 1, 85],
    [78, 104, 1, 1, 68],
    [78, 105, 1, 1, 17],
    [78, 106, 1, 1, 68],
    [78, 108, 1, 1, 85],
    [78, 109, 1, 1, 17],
    [78, 110, 1, 1, 51],
    [78, 111, 2, 1, 102],
    [78, 113, 1, 1, 51],
    [78, 114, 1, 1, 34],
    [78, 115, 2, 1, 102],
    [78, 117, 1, 1, 51],
    [78, 118, 1, 1, 17],
    [78, 119, 1, 1, 68],
    [78, 121, 1, 1, 68],
    [78, 122, 1, 1, 17],
    [78, 123, 1, 1, 51],
    [78, 125, 1, 1, 85],
    [78, 126, 1, 1, 17],
    [78, 127, 1, 1, 51],
    [78, 130, 1, 1, 51],
    [78, 131, 1, 1, 17],
    [78, 132, 1, 1, 85],
    [78, 134, 1, 1, 51],
    [78, 135, 1, 1, 17],
    [78, 136, 1, 1, 68],
    [78, 137, 1, 1, 85],
    [78, 138, 1, 1, 68],
    [78, 139, 1, 1, 17],
    [78, 140, 1, 1, 51],
    [78, 143, 1, 1, 17],
    [78, 144, 1, 1, 34],
    [78, 145, 2, 1, 85],
    [78, 147, 1, 1, 51],
    [78, 148, 1, 1, 17],
    [78, 149, 1, 1, 68],
    [78, 151, 1, 1, 51],
    [78, 152, 1, 1, 17],
    [78, 153, 1, 1, 51],
    [78, 155, 2, 1, 68],
    [78, 157, 1, 1, 85],
    [78, 158, 2, 1, 68],
    [79, 2, 4, 1, 170],
    [79, 6, 2, 1, 204],
    [79, 8, 1, 1, 187],
    [79, 9, 1, 1, 170],
    [79, 10, 1, 1, 187],
    [79, 11, 1, 1, 204],
    [79, 12, 1, 1, 187],
    [79, 13, 2, 1, 170],
    [79, 15, 2, 1, 204],
    [79, 19, 1, 1, 187],
    [79, 20, 1, 1, 204],
    [79, 21, 2, 1, 170],
    [79, 23, 2, 1, 187],
    [79, 25, 3, 1, 170],
    [79, 28, 1, 1, 187],
    [79, 29, 3, 1, 170],
    [79, 32, 1, 1, 187],
    [79, 33, 10, 1, 170],
    [79, 43, 1, 1, 153],
    [79, 44, 3, 1, 170],
    [79, 47, 2, 5, 153],
    [79, 49, 2, 1, 170],
    [79, 51, 2, 1, 153],
    [79, 53, 2, 1, 170],
    [79, 55, 2, 1, 153],
    [79, 57, 2, 1, 170],
    [79, 59, 3, 1, 153],
    [79, 62, 2, 1, 170],
    [79, 66, 3, 1, 153],
    [79, 69, 1, 1, 136],
    [79, 70, 2, 1, 153],
    [79, 72, 3, 1, 136],
    [79, 75, 2, 1, 153],
    [79, 77, 4, 1, 136],
    [79, 81, 2, 1, 119],
    [79, 83, 2, 1, 136],
    [79, 85, 2, 1, 119],
    [79, 87, 3, 1, 136],
    [79, 90, 2, 1, 119],
    [79, 92, 1, 1, 136],
    [79, 93, 6, 1, 119],
    [79, 99, 1, 1, 102],
    [79, 100, 3, 1, 119],
    [79, 103, 1, 1, 102],
    [79, 104, 3, 1, 119],
    [79, 107, 3, 1, 102],
    [79, 110, 1, 1, 119],
    [79, 111, 6, 1, 102],
    [79, 117, 2, 1, 119],
    [79, 119, 1, 1, 102],
    [79, 120, 1, 1, 85],
    [79, 121, 3, 1, 102],
    [79, 124, 1, 1, 85],
    [79, 125, 3, 1, 102],
    [79, 130, 2, 1, 102],
    [79, 132, 3, 1, 85],
    [79, 135, 1, 1, 102],
    [79, 136, 3, 1, 85],
    [79, 139, 1, 1, 102],
    [79, 140, 3, 1, 85],
    [79, 143, 1, 1, 102],
    [79, 144, 2, 1, 85],
    [79, 146, 1, 1, 68],
    [79, 147, 3, 1, 85],
    [79, 150, 1, 1, 68],
    [79, 151, 5, 1, 85],
    [79, 156, 4, 1, 68],
    [80, 2, 3, 7, 170],
    [80, 5, 1, 7, 187],
    [80, 6, 1, 1, 119],
    [80, 7, 1, 1, 51],
    [80, 8, 1, 1, 136],
    [80, 9, 1, 7, 204],
    [80, 10, 1, 1, 136],
    [80, 11, 1, 1, 51],
    [80, 12, 1, 1, 102],
    [80, 13, 1, 7, 187],
    [80, 14, 1, 1, 170],
    [80, 15, 2, 1, 68],
    [80, 19, 1, 1, 85],
    [80, 20, 1, 1, 51],
    [80, 21, 1, 1, 153],
    [80, 22, 1, 1, 187],
    [80, 23, 1, 1, 119],
    [80, 24, 1, 1, 51],
    [80, 25, 1, 1, 119],
    [80, 26, 1, 1, 170],
    [80, 27, 1, 1, 136],
    [80, 28, 1, 1, 51],
    [80, 29, 1, 1, 85],
    [80, 30, 2, 1, 170],
    [80, 32, 2, 1, 68],
    [80, 34, 1, 1, 153],
    [80, 35, 1, 7, 170],
    [80, 36, 1, 1, 102],
    [80, 37, 1, 1, 51],
    [80, 38, 1, 1, 136],
    [80, 39, 1, 7, 170],
    [80, 40, 1, 1, 119],
    [80, 41, 1, 1, 51],
    [80, 42, 1, 1, 102],
    [80, 43, 1, 7, 170],
    [80, 44, 1, 1, 136],
    [80, 45, 1, 1, 51],
    [80, 46, 1, 1, 68],
    [80, 49, 1, 1, 68],
    [80, 50, 1, 1, 51],
    [80, 51, 1, 1, 136],
    [80, 52, 1, 6, 170],
    [80, 53, 1, 1, 85],
    [80, 54, 1, 1, 34],
    [80, 55, 1, 1, 102],
    [80, 56, 1, 6, 170],
    [80, 57, 1, 1, 119],
    [80, 58, 1, 1, 51],
    [80, 59, 1, 1, 85],
    [80, 60, 1, 7, 153],
    [80, 61, 1, 1, 136],
    [80, 62, 2, 1, 51],
    [80, 64, 2, 9, 136],
    [80, 66, 1, 1, 68],
    [80, 67, 1, 1, 51],
    [80, 68, 1, 1, 119],
    [80, 69, 1, 6, 153],
    [80, 70, 1, 1, 85],
    [80, 71, 1, 1, 34],
    [80, 72, 1, 1, 85],
    [80, 73, 1, 1, 136],
    [80, 74, 1, 1, 102],
    [80, 75, 1, 1, 34],
    [80, 76, 1, 1, 68],
    [80, 77, 1, 8, 136],
    [80, 78, 1, 1, 119],
    [80, 79, 2, 1, 51],
    [80, 81, 1, 2, 119],
    [80, 82, 1, 2, 136],
    [80, 83, 1, 1, 68],
    [80, 84, 1, 1, 34],
    [80, 85, 1, 1, 102],
    [80, 86, 1, 6, 136],
    [80, 87, 1, 1, 85],
    [80, 88, 1, 1, 34],
    [80, 89, 1, 1, 85],
    [80, 90, 1, 4, 136],
    [80, 91, 1, 1, 102],
    [80, 92, 1, 1, 34],
    [80, 93, 1, 1, 51],
    [80, 94, 2, 1, 102],
    [80, 96, 2, 1, 51],
    [80, 98, 1, 1, 102],
    [80, 99, 1, 4, 119],
    [80, 100, 1, 1, 68],
    [80, 101, 1, 1, 17],
    [80, 102, 1, 1, 85],
    [80, 103, 1, 4, 119],
    [80, 104, 1, 1, 85],
    [80, 105, 1, 1, 34],
    [80, 106, 1, 1, 51],
    [80, 107, 1, 1, 102],
    [80, 108, 1, 1, 85],
    [80, 109, 1, 1, 34],
    [80, 110, 1, 1, 51],
    [80, 111, 2, 1, 102],
    [80, 113, 1, 1, 51],
    [80, 114, 1, 1, 34],
    [80, 115, 1, 1, 85],
    [80, 116, 1, 6, 102],
    [80, 117, 1, 1, 68],
    [80, 118, 1, 1, 17],
    [80, 119, 1, 1, 68],
    [80, 120, 1, 7, 102],
    [80, 121, 1, 1, 68],
    [80, 122, 1, 1, 17],
    [80, 123, 1, 1, 51],
    [80, 124, 1, 4, 102],
    [80, 125, 1, 1, 85],
    [80, 126, 1, 1, 51],
    [80, 127, 1, 1, 34],
    [80, 130, 1, 1, 51],
    [80, 131, 1, 1, 17],
    [80, 132, 1, 2, 68],
    [80, 133, 1, 3, 85],
    [80, 134, 1, 1, 68],
    [80, 135, 1, 1, 17],
    [80, 136, 1, 5, 51],
    [80, 137, 1, 1, 85],
    [80, 138, 1, 1, 68],
    [80, 139, 1, 1, 34],
    [80, 140, 1, 1, 51],
    [80, 141, 2, 1, 85],
    [80, 143, 1, 1, 51],
    [80, 144, 1, 1, 34],
    [80, 145, 1, 2, 68],
    [80, 146, 1, 2, 85],
    [80, 147, 1, 1, 51],
    [80, 148, 1, 1, 17],
    [80, 149, 1, 6, 51],
    [80, 150, 1, 7, 85],
    [80, 151, 1, 1, 51],
    [80, 152, 1, 1, 17],
    [80, 153, 1, 1, 51],
    [80, 154, 1, 1, 85],
    [80, 155, 1, 1, 68],
    [80, 156, 2, 1, 85],
    [80, 158, 1, 1, 68],
    [80, 159, 1, 1, 85],
    [81, 6, 1, 1, 51],
    [81, 7, 1, 5, 0],
    [81, 8, 1, 1, 85],
    [81, 10, 1, 5, 102],
    [81, 11, 1, 5, 0],
    [81, 12, 1, 5, 51],
    [81, 14, 1, 2, 153],
    [81, 15, 1, 1, 0],
    [81, 16, 1, 1, 17],
    [81, 17, 1, 5, 153],
    [81, 18, 1, 5, 170],
    [81, 19, 1, 1, 17],
    [81, 20, 1, 5, 0],
    [81, 21, 1, 5, 119],
    [81, 22, 1, 1, 204],
    [81, 23, 1, 1, 68],
    [81, 24, 1, 1, 0],
    [81, 25, 1, 1, 68],
    [81, 26, 1, 5, 187],
    [81, 27, 1, 1, 102],
    [81, 28, 1, 1, 0],
    [81, 29, 1, 5, 51],
    [81, 30, 1, 6, 170],
    [81, 31, 1, 6, 153],
    [81, 32, 2, 1, 17],
    [81, 34, 1, 1, 136],
    [81, 36, 1, 5, 51],
    [81, 37, 1, 1, 0],
    [81, 38, 1, 5, 102],
    [81, 40, 1, 1, 68],
    [81, 41, 1, 1, 0],
    [81, 42, 1, 5, 68],
    [81, 44, 1, 6, 119],
    [81, 45, 1, 1, 0],
    [81, 46, 1, 1, 17],
    [81, 49, 1, 1, 17],
    [81, 50, 1, 1, 0],
    [81, 51, 1, 5, 119],
    [81, 53, 1, 5, 51],
    [81, 54, 1, 1, 0],
    [81, 55, 1, 5, 85],
    [81, 57, 1, 1, 68],
    [81, 58, 1, 5, 0],
    [81, 59, 1, 5, 51],
    [81, 61, 1, 3, 119],
    [81, 62, 1, 1, 0],
    [81, 63, 1, 1, 17],
    [81, 66, 1, 1, 17],
    [81, 67, 1, 1, 0],
    [81, 68, 1, 5, 102],
    [81, 70, 1, 5, 51],
    [81, 71, 1, 5, 0],
    [81, 72, 1, 1, 51],
    [81, 73, 1, 5, 153],
    [81, 74, 1, 1, 68],
    [81, 75, 1, 5, 0],
    [81, 76, 1, 1, 17],
    [81, 78, 1, 6, 102],
    [81, 79, 2, 1, 0],
    [81, 83, 1, 1, 17],
    [81, 84, 1, 5, 0],
    [81, 85, 1, 4, 85],
    [81, 87, 1, 5, 51],
    [81, 88, 1, 5, 0],
    [81, 89, 1, 5, 51],
    [81, 91, 1, 1, 85],
    [81, 92, 1, 5, 0],
    [81, 93, 1, 1, 17],
    [81, 94, 1, 2, 119],
    [81, 95, 1, 2, 102],
    [81, 96, 2, 1, 0],
    [81, 98, 1, 2, 85],
    [81, 100, 1, 1, 17],
    [81, 101, 1, 5, 0],
    [81, 102, 1, 5, 68],
    [81, 104, 1, 5, 51],
    [81, 105, 1, 5, 0],
    [81, 106, 1, 5, 34],
    [81, 107, 1, 1, 119],
    [81, 108, 1, 5, 68],
    [81, 109, 1, 5, 0],
    [81, 110, 1, 5, 17],
    [81, 111, 1, 3, 102],
    [81, 112, 1, 3, 85],
    [81, 113, 1, 4, 17],
    [81, 114, 1, 4, 0],
    [81, 115, 1, 2, 68],
    [81, 117, 1, 2, 17],
    [81, 118, 1, 5, 0],
    [81, 119, 1, 5, 51],
    [81, 121, 1, 5, 51],
    [81, 122, 1, 5, 0],
    [81, 123, 1, 5, 17],
    [81, 125, 1, 6, 68],
    [81, 126, 2, 1, 0],
    [81, 130, 1, 5, 17],
    [81, 131, 1, 5, 0],
    [81, 134, 1, 5, 34],
    [81, 135, 1, 5, 0],
    [81, 137, 1, 2, 102],
    [81, 138, 1, 5, 51],
    [81, 139, 1, 5, 0],
    [81, 140, 1, 5, 17],
    [81, 141, 1, 6, 85],
    [81, 142, 1, 6, 68],
    [81, 143, 2, 5, 0],
    [81, 147, 1, 5, 17],
    [81, 148, 1, 5, 0],
    [81, 151, 1, 1, 34],
    [81, 152, 1, 5, 0],
    [81, 153, 1, 3, 34],
    [81, 154, 4, 1, 85],
    [81, 158, 2, 1, 68],
    [82, 0, 2, 1, 136],
    [82, 6, 1, 1, 68],
    [82, 8, 1, 1, 102],
    [82, 15, 2, 1, 17],
    [82, 19, 1, 3, 34],
    [82, 22, 1, 1, 187],
    [82, 23, 1, 2, 85],
    [82, 24, 1, 3, 17],
    [82, 25, 1, 4, 85],
    [82, 27, 1, 3, 119],
    [82, 28, 1, 3, 17],
    [82, 32, 1, 3, 17],
    [82, 33, 1, 3, 34],
    [82, 34, 1, 1, 153],
    [82, 37, 1, 4, 17],
    [82, 40, 1, 3, 85],
    [82, 41, 1, 3, 17],
    [82, 45, 1, 3, 17],
    [82, 46, 1, 3, 51],
    [82, 49, 2, 4, 17],
    [82, 54, 1, 3, 17],
    [82, 57, 1, 3, 85],
    [82, 62, 1, 1, 17],
    [82, 63, 1, 1, 34],
    [82, 66, 2, 3, 17],
    [82, 72, 1, 4, 68],
    [82, 74, 1, 3, 85],
    [82, 76, 1, 3, 51],
    [82, 79, 2, 3, 17],
    [82, 81, 2, 2, 119],
    [82, 83, 1, 1, 34],
    [82, 91, 1, 4, 68],
    [82, 93, 1, 3, 34],
    [82, 96, 2, 3, 17],
    [82, 100, 1, 3, 34],
    [82, 107, 1, 3, 102],
    [82, 126, 1, 3, 0],
    [82, 127, 1, 3, 17],
    [82, 132, 1, 2, 51],
    [82, 145, 2, 2, 85],
    [82, 151, 1, 1, 51],
    [82, 154, 2, 1, 85],
    [82, 156, 4, 1, 68],
    [83, 0, 1, 2, 119],
    [83, 1, 1, 2, 136],
    [83, 6, 1, 1, 51],
    [83, 8, 1, 1, 85],
    [83, 14, 1, 3, 136],
    [83, 15, 1, 3, 0],
    [83, 16, 1, 3, 17],
    [83, 22, 1, 1, 204],
    [83, 34, 1, 3, 136],
    [83, 62, 2, 1, 17],
    [83, 83, 1, 3, 17],
    [83, 94, 1, 1, 102],
    [83, 95, 1, 1, 85],
    [83, 98, 1, 1, 102],
    [83, 115, 1, 1, 85],
    [83, 117, 1, 2, 34],
    [83, 133, 1, 1, 102],
    [83, 137, 1, 3, 85],
    [83, 151, 1, 2, 34],
    [83, 154, 1, 4, 85],
    [83, 155, 1, 1, 68],
    [83, 156, 2, 1, 85],
    [83, 158, 2, 1, 68],
    [84, 6, 1, 1, 68],
    [84, 8, 1, 1, 102],
    [84, 22, 1, 2, 187],
    [84, 23, 1, 2, 68],
    [84, 47, 1, 2, 153],
    [84, 48, 1, 2, 136],
    [84, 61, 1, 2, 102],
    [84, 62, 1, 1, 17],
    [84, 63, 1, 1, 34],
    [84, 81, 1, 1, 102],
    [84, 82, 1, 1, 119],
    [84, 90, 1, 3, 119],
    [84, 94, 1, 3, 119],
    [84, 95, 1, 3, 102],
    [84, 98, 1, 2, 85],
    [84, 99, 1, 2, 102],
    [84, 103, 1, 1, 102],
    [84, 111, 2, 1, 85],
    [84, 115, 1, 2, 68],
    [84, 124, 1, 3, 85],
    [84, 132, 1, 3, 68],
    [84, 133, 1, 3, 85],
    [84, 145, 1, 3, 68],
    [84, 146, 1, 3, 85],
    [84, 153, 1, 1, 51],
    [84, 155, 3, 1, 68],
    [84, 158, 1, 1, 51],
    [84, 159, 1, 1, 68],
    [85, 0, 2, 1, 136],
    [85, 6, 1, 1, 51],
    [85, 8, 1, 1, 85],
    [85, 19, 1, 1, 17],
    [85, 24, 1, 1, 0],
    [85, 27, 1, 1, 102],
    [85, 28, 1, 1, 0],
    [85, 32, 2, 1, 17],
    [85, 40, 1, 1, 68],
    [85, 41, 1, 1, 0],
    [85, 45, 1, 1, 0],
    [85, 46, 1, 1, 34],
    [85, 54, 1, 1, 0],
    [85, 57, 1, 1, 68],
    [85, 62, 1, 1, 0],
    [85, 63, 1, 1, 17],
    [85, 66, 1, 1, 17],
    [85, 67, 1, 1, 0],
    [85, 74, 1, 1, 68],
    [85, 76, 1, 1, 34],
    [85, 79, 1, 1, 0],
    [85, 80, 1, 1, 17],
    [85, 81, 2, 2, 119],
    [85, 85, 1, 1, 68],
    [85, 93, 1, 1, 17],
    [85, 96, 2, 1, 0],
    [85, 100, 1, 1, 17],
    [85, 103, 1, 1, 119],
    [85, 107, 1, 1, 119],
    [85, 111, 1, 2, 102],
    [85, 112, 1, 2, 85],
    [85, 113, 2, 1, 0],
    [85, 117, 1, 1, 17],
    [85, 126, 2, 1, 0],
    [85, 136, 1, 1, 34],
    [85, 151, 1, 2, 51],
    [85, 153, 1, 1, 17],
    [85, 155, 1, 1, 68],
    [85, 156, 1, 1, 85],
    [85, 157, 3, 1, 68],
    [86, 0, 1, 2, 136],
    [86, 1, 1, 3, 153],
    [86, 6, 1, 1, 102],
    [86, 7, 1, 1, 17],
    [86, 8, 1, 1, 119],
    [86, 10, 1, 1, 136],
    [86, 11, 1, 1, 17],
    [86, 12, 1, 1, 85],
    [86, 14, 1, 1, 153],
    [86, 15, 2, 1, 51],
    [86, 17, 2, 3, 170],
    [86, 19, 1, 1, 68],
    [86, 20, 1, 1, 34],
    [86, 21, 1, 1, 136],
    [86, 22, 1, 1, 170],
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
