alexliesenfeld/dgx-spark-printables/spark-atom/images/gigabyte-top-ai-nano-projection.scad

/*
 * Demo-only pixel projection generated from gigabyte-top-ai-nano.jpg.
 * Rows are stored top-to-bottom; the module flips them so the photograph's
 * bottom edge maps to Y=0, the physical front of the device.
 * Adjacent equal-shade pixels are merged into rectangles for faster previews.
 */

gigabyte_top_ai_nano_projection_size = 160;
gigabyte_top_ai_nano_projection_rectangles = [
    [0, 0, 2, 1, 34],
    [0, 2, 2, 1, 68],
    [0, 4, 6, 1, 34],
    [0, 10, 140, 1, 51],
    [0, 150, 6, 1, 34],
    [0, 156, 1, 1, 85],
    [0, 157, 1, 1, 51],
    [0, 158, 1, 1, 34],
    [0, 159, 1, 1, 51],
    [1, 0, 2, 1, 68],
    [1, 2, 1, 1, 102],
    [1, 3, 1, 3, 85],
    [1, 4, 152, 3, 51],
    [1, 156, 2, 1, 85],
    [1, 158, 1, 2, 68],
    [1, 159, 1, 2, 85],
    [2, 0, 1, 2, 85],
    [2, 1, 1, 2, 68],
    [2, 2, 1, 1, 119],
    [2, 156, 1, 1, 85],
    [2, 157, 1, 1, 102],
    [3, 2, 1, 1, 102],
    [3, 156, 1, 2, 102],
    [3, 157, 3, 1, 85],
    [4, 0, 3, 1, 85],
    [4, 3, 1, 1, 119],
    [4, 4, 1, 1, 68],
    [4, 5, 150, 1, 51],
    [4, 155, 1, 1, 85],
    [4, 157, 1, 1, 68],
    [4, 158, 2, 1, 85],
    [5, 0, 5, 1, 85],
    [5, 5, 150, 1, 68],
    [5, 155, 3, 1, 85],
    [5, 158, 1, 1, 68],
    [5, 159, 1, 1, 85],
    [6, 0, 160, 1, 85],
    [7, 0, 80, 1, 85],
    [7, 80, 1, 1, 68],
    [7, 81, 79, 1, 85],
    [8, 0, 3, 19, 85],
    [8, 3, 1, 1, 68],
    [8, 4, 1, 1, 51],
    [8, 5, 47, 1, 68],
    [8, 52, 1, 1, 51],
    [8, 53, 1, 1, 68],
    [8, 54, 1, 1, 51],
    [8, 55, 22, 1, 68],
    [8, 77, 1, 1, 51],
    [8, 78, 20, 1, 68],
    [8, 98, 1, 1, 51],
    [8, 99, 57, 1, 68],
    [8, 156, 4, 1, 85],
    [9, 3, 1, 1, 51],
    [9, 4, 1, 1, 68],
    [9, 5, 5, 1, 85],
    [9, 10, 2, 1, 68],
    [9, 12, 4, 1, 85],
    [9, 16, 1, 1, 68],
    [9, 17, 6, 1, 85],
    [9, 23, 1, 1, 68],
    [9, 24, 3, 1, 85],
    [9, 27, 1, 1, 68],
    [9, 28, 8, 1, 85],
    [9, 36, 1, 1, 68],
    [9, 37, 1, 1, 85],
    [9, 38, 3, 1, 68],
    [9, 41, 3, 1, 85],
    [9, 44, 1, 1, 68],
    [9, 45, 2, 1, 85],
    [9, 47, 2, 1, 68],
    [9, 49, 2, 1, 85],
    [9, 51, 1, 1, 68],
    [9, 52, 1, 1, 85],
    [9, 53, 3, 1, 68],
    [9, 56, 13, 1, 85],
    [9, 69, 1, 1, 68],
    [9, 70, 11, 1, 85],
    [9, 81, 1, 1, 68],
    [9, 82, 5, 1, 85],
    [9, 87, 1, 1, 68],
    [9, 88, 10, 1, 85],
    [9, 98, 1, 1, 68],
    [9, 99, 21, 1, 85],
    [9, 120, 2, 1, 68],
    [9, 122, 25, 1, 85],
    [9, 147, 1, 1, 68],
    [9, 148, 8, 1, 85],
    [9, 156, 1, 1, 68],
    [9, 157, 3, 1, 85],
    [10, 3, 1, 24, 68],
    [10, 4, 22, 1, 85],
    [10, 26, 1, 1, 68],
    [10, 27, 6, 1, 85],
    [10, 33, 1, 1, 68],
    [10, 34, 25, 1, 85],
    [10, 59, 1, 1, 68],
    [10, 60, 13, 1, 85],
    [10, 73, 1, 1, 68],
    [10, 74, 18, 1, 85],
    [10, 92, 1, 1, 68],
    [10, 93, 67, 1, 85],
    [11, 4, 24, 1, 85],
    [11, 28, 1, 1, 68],
    [11, 29, 22, 1, 85],
    [11, 51, 1, 1, 68],
    [11, 52, 8, 1, 85],
    [11, 60, 1, 1, 68],
    [11, 61, 10, 1, 85],
    [11, 71, 1, 1, 68],
    [11, 72, 19, 1, 85],
    [11, 91, 2, 1, 68],
    [11, 93, 29, 1, 85],
    [11, 122, 1, 1, 68],
    [11, 123, 37, 1, 85],
    [12, 4, 31, 1, 85],
    [12, 35, 1, 1, 68],
    [12, 36, 2, 1, 85],
    [12, 38, 1, 1, 68],
    [12, 39, 15, 1, 85],
    [12, 54, 2, 1, 68],
    [12, 56, 5, 1, 85],
    [12, 61, 2, 1, 68],
    [12, 63, 10, 1, 85],
    [12, 73, 1, 1, 68],
    [12, 74, 2, 1, 85],
    [12, 76, 1, 2, 68],
    [12, 77, 2, 1, 85],
    [12, 79, 1, 1, 68],
    [12, 80, 9, 1, 85],
    [12, 89, 1, 1, 68],
    [12, 90, 31, 1, 85],
    [12, 121, 1, 1, 68],
    [12, 122, 34, 1, 85],
    [12, 156, 1, 1, 68],
    [12, 157, 1, 1, 85],
    [12, 158, 1, 1, 68],
    [12, 159, 1, 1, 85],
    [13, 4, 36, 1, 85],
    [13, 40, 2, 2, 68],
    [13, 42, 13, 1, 85],
    [13, 55, 1, 1, 68],
    [13, 56, 9, 1, 85],
    [13, 65, 2, 1, 68],
    [13, 67, 2, 1, 85],
    [13, 69, 1, 1, 68],
    [13, 70, 2, 1, 85],
    [13, 72, 1, 1, 68],
    [13, 73, 1, 1, 85],
    [13, 74, 1, 1, 68],
    [13, 75, 1, 1, 85],
    [13, 77, 5, 1, 85],
    [13, 82, 1, 1, 68],
    [13, 83, 4, 1, 85],
    [13, 87, 2, 1, 68],
    [13, 89, 1, 1, 85],
    [13, 90, 1, 1, 68],
    [13, 91, 10, 1, 85],
    [13, 101, 1, 1, 68],
    [13, 102, 15, 1, 85],
    [13, 117, 1, 2, 68],
    [13, 118, 2, 1, 85],
    [13, 120, 1, 1, 68],
    [13, 121, 36, 1, 85],
    [13, 157, 1, 1, 68],
    [13, 158, 2, 1, 85],
    [14, 4, 20, 1, 85],
    [14, 24, 1, 1, 68],
    [14, 25, 6, 1, 85],
    [14, 31, 2, 1, 68],
    [14, 33, 1, 1, 85],
    [14, 34, 1, 1, 68],
    [14, 35, 1, 1, 85],
    [14, 36, 1, 1, 68],
    [14, 37, 3, 1, 85],
    [14, 42, 1, 1, 85],
    [14, 43, 1, 1, 68],
    [14, 44, 2, 1, 85],
    [14, 46, 3, 1, 68],
    [14, 49, 6, 1, 85],
    [14, 55, 2, 1, 68],
    [14, 57, 1, 1, 85],
    [14, 58, 3, 1, 68],
    [14, 61, 2, 1, 85],
    [14, 63, 3, 1, 68],
    [14, 66, 2, 1, 85],
    [14, 68, 3, 1, 68],
    [14, 71, 1, 1, 85],
    [14, 72, 2, 1, 68],
    [14, 74, 4, 1, 85],
    [14, 78, 1, 1, 68],
    [14, 79, 1, 2, 85],
    [14, 80, 1, 2, 68],
    [14, 81, 2, 1, 85],
    [14, 83, 3, 1, 68],
    [14, 86, 2, 1, 85],
    [14, 88, 1, 1, 68],
    [14, 89, 3, 1, 85],
    [14, 92, 1, 1, 68],
    [14, 93, 10, 1, 85],
    [14, 103, 2, 1, 68],
    [14, 105, 4, 1, 85],
    [14, 109, 1, 1, 68],
    [14, 110, 1, 1, 85],
    [14, 111, 1, 1, 68],
    [14, 112, 5, 1, 85],
    [14, 118, 1, 1, 85],
    [14, 119, 1, 2, 68],
    [14, 120, 1, 1, 85],
    [14, 121, 1, 1, 68],
    [14, 122, 3, 1, 85],
    [14, 125, 1, 1, 68],
    [14, 126, 3, 1, 85],
    [14, 129, 1, 1, 68],
    [14, 130, 30, 1, 85],
    [15, 4, 23, 1, 85],
    [15, 27, 9, 1, 68],
    [15, 36, 1, 1, 85],
    [15, 37, 4, 1, 68],
    [15, 41, 2, 1, 85],
    [15, 43, 6, 1, 68],
    [15, 49, 3, 1, 85],
    [15, 52, 8, 1, 68],
    [15, 60, 2, 1, 85],
    [15, 62, 3, 1, 68],
    [15, 65, 1, 1, 85],
    [15, 66, 6, 1, 68],
    [15, 72, 3, 1, 85],
    [15, 75, 4, 1, 68],
    [15, 81, 1, 1, 85],
    [15, 82, 1, 1, 68],
    [15, 83, 1, 1, 85],
    [15, 84, 1, 1, 68],
    [15, 85, 2, 1, 85],
    [15, 87, 1, 1, 68],
    [15, 88, 1, 2, 85],
    [15, 89, 2, 1, 68],
    [15, 91, 1, 1, 85],
    [15, 92, 3, 1, 68],
    [15, 95, 2, 1, 85],
    [15, 97, 1, 1, 68],
    [15, 98, 1, 1, 85],
    [15, 99, 7, 1, 68],
    [15, 106, 1, 1, 85],
    [15, 107, 1, 1, 68],
    [15, 108, 1, 1, 85],
    [15, 109, 2, 1, 68],
    [15, 111, 8, 1, 85],
    [15, 120, 3, 1, 85],
    [15, 123, 4, 1, 68],
    [15, 127, 9, 1, 85],
    [15, 136, 1, 1, 68],
    [15, 137, 12, 1, 85],
    [15, 149, 1, 1, 68],
    [15, 150, 10, 1, 85],
    [16, 4, 10, 1, 85],
    [16, 14, 1, 1, 68],
    [16, 15, 5, 1, 85],
    [16, 20, 1, 1, 68],
    [16, 21, 3, 1, 85],
    [16, 24, 60, 1, 68],
    [16, 84, 1, 1, 85],
    [16, 85, 3, 1, 68],
    [16, 89, 10, 1, 68],
    [16, 99, 1, 1, 85],
    [16, 100, 7, 1, 68],
    [16, 107, 1, 2, 85],
    [16, 108, 2, 1, 68],
    [16, 110, 1, 1, 85],
    [16, 111, 6, 1, 68],
    [16, 117, 1, 1, 85],
    [16, 118, 7, 1, 68],
    [16, 125, 21, 1, 85],
    [16, 146, 1, 1, 68],
    [16, 147, 13, 1, 85],
    [17, 4, 15, 1, 85],
    [17, 19, 1, 1, 68],
    [17, 20, 2, 1, 85],
    [17, 22, 25, 1, 68],
    [17, 47, 1, 1, 85],
    [17, 48, 47, 1, 68],
    [17, 95, 1, 1, 85],
    [17, 96, 11, 1, 68],
    [17, 108, 20, 1, 68],
    [17, 128, 11, 2, 85],
    [17, 139, 1, 2, 68],
    [17, 140, 2, 1, 85],
    [17, 142, 1, 1, 68],
    [17, 143, 13, 1, 85],
    [17, 156, 1, 1, 68],
    [17, 157, 3, 1, 85],
    [18, 4, 13, 1, 85],
    [18, 17, 1, 1, 68],
    [18, 18, 1, 1, 85],
    [18, 19, 109, 1, 68],
    [18, 140, 16, 1, 85],
    [18, 156, 2, 1, 68],
    [18, 158, 2, 1, 85],
    [19, 4, 14, 1, 85],
    [19, 18, 110, 1, 68],
    [19, 128, 28, 1, 85],
    [19, 156, 1, 1, 68],
    [19, 157, 3, 1, 85],
    [20, 4, 3, 1, 85],
    [20, 7, 1, 1, 68],
    [20, 8, 6, 1, 85],
    [20, 14, 1, 1, 68],
    [20, 15, 3, 1, 85],
    [20, 18, 35, 1, 68],
    [20, 53, 1, 1, 51],
    [20, 54, 48, 1, 68],
    [20, 102, 2, 1, 51],
    [20, 104, 25, 1, 68],
    [20, 129, 27, 1, 85],
    [20, 156, 2, 2, 68],
    [20, 158, 2, 3, 85],
    [21, 4, 13, 1, 85],
    [21, 17, 14, 1, 68],
    [21, 31, 1, 1, 51],
    [21, 32, 1, 1, 68],
    [21, 33, 93, 1, 51],
    [21, 126, 4, 1, 68],
    [21, 130, 5, 1, 85],
    [21, 135, 3, 1, 102],
    [21, 138, 18, 1, 85],
    [22, 4, 2, 1, 85],
    [22, 6, 1, 1, 68],
    [22, 7, 8, 1, 85],
    [22, 15, 1, 1, 68],
    [22, 16, 1, 1, 85],
    [22, 17, 7, 1, 68],
    [22, 24, 1, 1, 85],
    [22, 25, 5, 1, 68],
    [22, 30, 97, 1, 51],
    [22, 127, 3, 1, 68],
    [22, 130, 4, 1, 85],
    [22, 134, 6, 1, 102],
    [22, 140, 17, 1, 85],
    [22, 157, 1, 1, 68],
    [23, 4, 8, 2, 85],
    [23, 12, 1, 2, 68],
    [23, 13, 1, 2, 85],
    [23, 14, 8, 1, 68],
    [23, 22, 3, 1, 85],
    [23, 25, 3, 1, 68],
    [23, 28, 4, 1, 51],
    [23, 32, 4, 1, 34],
    [23, 36, 2, 1, 51],
    [23, 38, 1, 1, 34],
    [23, 39, 8, 1, 51],
    [23, 47, 1, 1, 34],
    [23, 48, 2, 1, 51],
    [23, 50, 1, 1, 34],
    [23, 51, 1, 1, 51],
    [23, 52, 1, 1, 34],
    [23, 53, 3, 1, 51],
    [23, 56, 1, 1, 34],
    [23, 57, 16, 1, 51],
    [23, 73, 1, 1, 34],
    [23, 74, 12, 1, 51],
    [23, 86, 1, 1, 34],
    [23, 87, 1, 1, 51],
    [23, 88, 1, 1, 34],
    [23, 89, 3, 1, 51],
    [23, 92, 1, 1, 34],
    [23, 93, 12, 1, 51],
    [23, 105, 1, 1, 34],
    [23, 106, 22, 1, 51],
    [23, 128, 3, 1, 68],
    [23, 131, 2, 2, 85],
    [23, 133, 3, 3, 102],
    [23, 136, 1, 1, 119],
    [23, 137, 5, 1, 102],
    [23, 142, 14, 2, 85],
    [23, 156, 3, 1, 68],
    [23, 159, 1, 1, 85],
    [24, 14, 6, 2, 68],
    [24, 20, 5, 1, 85],
    [24, 25, 2, 1, 68],
    [24, 27, 5, 1, 51],
    [24, 32, 99, 1, 68],
    [24, 136, 4, 1, 119],
    [24, 140, 2, 1, 102],
    [24, 156, 1, 2, 68],
    [24, 157, 2, 1, 85],
    [24, 159, 1, 1, 102],
    [25, 4, 10, 1, 85],
    [25, 20, 3, 1, 85],
    [25, 23, 3, 1, 68],
    [25, 26, 2, 1, 51],
    [25, 28, 5, 1, 68],
    [25, 33, 94, 1, 51],
    [25, 127, 3, 1, 68],
    [25, 130, 3, 1, 85],
    [25, 136, 6, 1, 119],
    [25, 142, 1, 1, 102],
    [25, 143, 13, 1, 85],
    [25, 157, 3, 1, 85],
    [26, 4, 5, 2, 85],
    [26, 9, 1, 1, 68],
    [26, 10, 2, 1, 85],
    [26, 12, 7, 1, 68],
    [26, 19, 4, 1, 85],
    [26, 23, 6, 1, 68],
    [26, 29, 1, 1, 51],
    [26, 30, 100, 1, 34],
    [26, 130, 1, 1, 51],
    [26, 131, 1, 1, 68],
    [26, 132, 2, 1, 85],
    [26, 134, 2, 1, 102],
    [26, 136, 3, 1, 119],
    [26, 139, 1, 1, 136],
    [26, 140, 2, 1, 119],
    [26, 142, 2, 1, 102],
    [26, 144, 13, 1, 85],
    [26, 157, 1, 1, 68],
    [26, 158, 2, 3, 85],
    [27, 0, 1, 1, 68],
    [27, 1, 2, 1, 85],
    [27, 9, 9, 1, 68],
    [27, 18, 3, 1, 85],
    [27, 21, 4, 2, 68],
    [27, 25, 1, 1, 85],
    [27, 26, 1, 1, 68],
    [27, 27, 105, 1, 34],
    [27, 132, 1, 1, 51],
    [27, 133, 1, 1, 68],
    [27, 134, 1, 1, 85],
    [27, 135, 1, 1, 102],
    [27, 136, 2, 2, 119],
    [27, 138, 4, 1, 136],
    [27, 142, 1, 1, 119],
    [27, 143, 1, 1, 102],
    [27, 144, 12, 1, 85],
    [27, 156, 2, 1, 68],
    [28, 0, 3, 4, 85],
    [28, 4, 7, 1, 85],
    [28, 11, 6, 2, 68],
    [28, 17, 4, 1, 85],
    [28, 25, 1, 1, 51],
    [28, 26, 108, 1, 34],
    [28, 134, 1, 1, 51],
    [28, 135, 1, 1, 85],
    [28, 138, 5, 1, 136],
    [28, 143, 1, 1, 119],
    [28, 144, 2, 2, 102],
    [28, 146, 11, 1, 85],
    [28, 157, 1, 1, 68],
    [29, 4, 5, 2, 85],
    [29, 9, 1, 1, 68],
    [29, 10, 1, 1, 85],
    [29, 17, 2, 1, 85],
    [29, 19, 5, 1, 68],
    [29, 24, 111, 1, 34],
    [29, 135, 1, 1, 51],
    [29, 136, 1, 1, 85],
    [29, 137, 1, 1, 119],
    [29, 138, 3, 2, 136],
    [29, 141, 1, 1, 153],
    [29, 142, 2, 1, 136],
    [29, 146, 10, 1, 85],
    [29, 156, 1, 3, 68],
    [29, 157, 3, 3, 85],
    [30, 9, 8, 1, 68],
    [30, 17, 1, 1, 85],
    [30, 18, 4, 1, 68],
    [30, 22, 1, 1, 85],
    [30, 23, 1, 1, 51],
    [30, 24, 112, 1, 34],
    [30, 136, 1, 1, 51],
    [30, 137, 1, 1, 85],
    [30, 141, 2, 1, 153],
    [30, 143, 1, 1, 136],
    [30, 144, 1, 1, 119],
    [30, 145, 2, 2, 102],
    [30, 147, 9, 2, 85],
    [31, 4, 7, 1, 85],
    [31, 11, 9, 1, 68],
    [31, 20, 1, 1, 51],
    [31, 21, 1, 1, 68],
    [31, 22, 1, 1, 51],
    [31, 23, 114, 1, 34],
    [31, 137, 1, 1, 51],
    [31, 138, 1, 1, 119],
    [31, 139, 2, 2, 136],
    [31, 141, 3, 2, 153],
    [31, 144, 1, 2, 136],
    [32, 0, 1, 1, 68],
    [32, 1, 2, 1, 85],
    [32, 4, 5, 1, 85],
    [32, 9, 10, 1, 68],
    [32, 19, 1, 1, 51],
    [32, 20, 2, 1, 68],
    [32, 22, 116, 2, 34],
    [32, 138, 1, 1, 85],
    [32, 145, 1, 1, 119],
    [32, 146, 1, 1, 102],
    [32, 147, 10, 1, 85],
    [32, 157, 1, 2, 68],
    [32, 158, 2, 2, 85],
    [33, 0, 3, 1, 85],
    [33, 4, 4, 1, 85],
    [33, 8, 1, 1, 68],
    [33, 9, 1, 1, 85],
    [33, 10, 8, 2, 68],
    [33, 18, 2, 2, 51],
    [33, 20, 1, 2, 68],
    [33, 21, 1, 1, 51],
    [33, 138, 1, 1, 51],
    [33, 139, 1, 1, 119],
    [33, 140, 5, 1, 153],
    [33, 145, 1, 6, 136],
    [33, 146, 2, 1, 102],
    [33, 148, 9, 1, 85],
    [34, 0, 2, 1, 85],
    [34, 2, 2, 1, 68],
    [34, 4, 6, 2, 85],
    [34, 21, 118, 1, 34],
    [34, 139, 1, 1, 85],
    [34, 140, 1, 2, 136],
    [34, 141, 4, 4, 153],
    [34, 146, 3, 1, 102],
    [34, 149, 7, 1, 85],
    [34, 156, 1, 1, 68],
    [34, 157, 3, 1, 85],
    [35, 0, 3, 3, 85],
    [35, 3, 1, 55, 68],
    [35, 10, 3, 1, 68],
    [35, 13, 1, 1, 85],
    [35, 14, 4, 1, 68],
    [35, 18, 1, 2, 51],
    [35, 19, 2, 1, 68],
    [35, 21, 9, 1, 34],
    [35, 30, 1, 1, 17],
    [35, 31, 98, 1, 34],
    [35, 129, 1, 1, 17],
    [35, 130, 9, 1, 34],
    [35, 139, 1, 1, 68],
    [35, 146, 1, 89, 119],
    [35, 147, 1, 7, 102],
    [35, 148, 8, 5, 85],
    [35, 156, 2, 5, 68],
    [35, 158, 2, 5, 85],
    [36, 4, 4, 1, 85],
    [36, 8, 1, 1, 68],
    [36, 9, 2, 1, 85],
    [36, 11, 7, 1, 68],
    [36, 19, 1, 1, 68],
    [36, 20, 1, 2, 51],
    [36, 21, 8, 1, 34],
    [36, 29, 1, 1, 17],
    [36, 30, 98, 1, 34],
    [36, 128, 1, 1, 51],
    [36, 129, 1, 1, 34],
    [36, 130, 1, 2, 17],
    [36, 131, 8, 2, 34],
    [36, 139, 1, 3, 51],
    [36, 140, 1, 1, 119],
    [37, 4, 6, 1, 85],
    [37, 10, 2, 1, 68],
    [37, 12, 3, 1, 85],
    [37, 15, 5, 1, 68],
    [37, 21, 7, 1, 34],
    [37, 28, 2, 1, 17],
    [37, 30, 99, 1, 34],
    [37, 129, 1, 3, 51],
    [37, 140, 1, 3, 102],
    [38, 0, 1, 1, 68],
    [38, 1, 2, 1, 85],
    [38, 4, 7, 1, 85],
    [38, 11, 1, 1, 68],
    [38, 12, 4, 1, 85],
    [38, 16, 4, 2, 68],
    [38, 20, 8, 2, 34],
    [38, 28, 1, 1, 17],
    [38, 29, 100, 1, 34],
    [38, 130, 2, 2, 17],
    [38, 132, 7, 1, 34],
    [38, 141, 2, 2, 153],
    [38, 143, 1, 2, 170],
    [38, 144, 1, 1, 153],
    [39, 0, 3, 16, 85],
    [39, 4, 5, 1, 85],
    [39, 9, 4, 1, 68],
    [39, 13, 3, 1, 85],
    [39, 28, 2, 1, 17],
    [39, 30, 1, 1, 51],
    [39, 31, 98, 1, 34],
    [39, 132, 8, 1, 34],
    [39, 144, 2, 1, 153],
    [40, 4, 6, 2, 85],
    [40, 10, 1, 2, 68],
    [40, 11, 8, 2, 85],
    [40, 19, 1, 5, 68],
    [40, 20, 9, 2, 34],
    [40, 29, 1, 1, 17],
    [40, 30, 1, 1, 34],
    [40, 31, 1, 1, 51],
    [40, 32, 96, 1, 34],
    [40, 128, 1, 1, 51],
    [40, 129, 1, 1, 34],
    [40, 130, 1, 1, 17],
    [40, 131, 9, 1, 34],
    [40, 140, 1, 1, 85],
    [40, 141, 4, 1, 153],
    [40, 145, 1, 1, 136],
    [40, 148, 12, 2, 85],
    [41, 29, 2, 1, 17],
    [41, 31, 2, 1, 34],
    [41, 33, 2, 1, 51],
    [41, 35, 3, 1, 34],
    [41, 38, 1, 1, 51],
    [41, 39, 2, 1, 34],
    [41, 41, 4, 1, 51],
    [41, 45, 1, 1, 34],
    [41, 46, 10, 1, 51],
    [41, 56, 1, 1, 34],
    [41, 57, 1, 1, 51],
    [41, 58, 1, 1, 34],
    [41, 59, 4, 1, 51],
    [41, 63, 1, 1, 34],
    [41, 64, 6, 1, 51],
    [41, 70, 4, 1, 34],
    [41, 74, 1, 1, 51],
    [41, 75, 1, 1, 34],
    [41, 76, 3, 1, 51],
    [41, 79, 1, 1, 34],
    [41, 80, 11, 1, 51],
    [41, 91, 1, 1, 34],
    [41, 92, 1, 1, 51],
    [41, 93, 3, 1, 34],
    [41, 96, 1, 1, 51],
    [41, 97, 1, 1, 34],
    [41, 98, 8, 1, 51],
    [41, 106, 1, 1, 34],
    [41, 107, 4, 1, 51],
    [41, 111, 1, 1, 34],
    [41, 112, 5, 1, 51],
    [41, 117, 2, 1, 34],
    [41, 119, 4, 1, 51],
    [41, 123, 1, 1, 34],
    [41, 124, 2, 1, 51],
    [41, 126, 1, 1, 34],
    [41, 127, 1, 1, 51],
    [41, 128, 1, 1, 34],
    [41, 129, 1, 1, 17],
    [41, 130, 10, 1, 34],
    [41, 140, 1, 3, 102],
    [41, 141, 5, 1, 153],
    [42, 4, 13, 1, 85],
    [42, 17, 1, 1, 68],
    [42, 18, 1, 1, 85],
    [42, 20, 11, 1, 34],
    [42, 31, 1, 1, 17],
    [42, 32, 96, 1, 34],
    [42, 128, 1, 1, 17],
    [42, 129, 11, 1, 34],
    [42, 141, 4, 5, 153],
    [42, 145, 1, 5, 136],
    [42, 147, 2, 4, 102],
    [42, 149, 7, 1, 85],
    [42, 156, 1, 1, 68],
    [42, 157, 3, 1, 85],
    [43, 4, 2, 1, 85],
    [43, 6, 1, 1, 68],
    [43, 7, 2, 1, 85],
    [43, 9, 4, 1, 68],
    [43, 13, 6, 1, 85],
    [43, 20, 120, 25, 34],
    [43, 149, 8, 1, 85],
    [43, 157, 1, 1, 68],
    [43, 158, 2, 1, 85],
    [44, 4, 4, 1, 85],
    [44, 8, 1, 1, 68],
    [44, 9, 1, 1, 85],
    [44, 10, 2, 1, 68],
    [44, 12, 7, 1, 85],
    [44, 140, 1, 1, 85],
    [44, 149, 11, 2, 85],
    [45, 4, 3, 2, 85],
    [45, 7, 1, 1, 68],
    [45, 8, 2, 1, 85],
    [45, 10, 1, 1, 68],
    [45, 11, 6, 1, 85],
    [45, 17, 3, 1, 68],
    [45, 140, 1, 2, 102],
    [46, 7, 3, 1, 68],
    [46, 10, 1, 1, 85],
    [46, 11, 1, 1, 68],
    [46, 12, 7, 1, 85],
    [46, 19, 1, 1, 68],
    [46, 147, 1, 1, 102],
    [46, 148, 9, 1, 85],
    [46, 157, 1, 2, 68],
    [46, 158, 2, 5, 85],
    [47, 4, 14, 1, 85],
    [47, 18, 2, 1, 68],
    [47, 140, 1, 1, 85],
    [47, 141, 5, 2, 153],
    [47, 147, 2, 5, 102],
    [47, 149, 8, 1, 85],
    [48, 4, 3, 1, 85],
    [48, 7, 1, 1, 68],
    [48, 8, 2, 1, 85],
    [48, 10, 1, 1, 68],
    [48, 11, 6, 1, 85],
    [48, 17, 3, 1, 68],
    [48, 140, 1, 3, 102],
    [48, 149, 7, 4, 85],
    [48, 156, 2, 3, 68],
    [49, 4, 4, 1, 85],
    [49, 8, 1, 1, 68],
    [49, 9, 10, 1, 85],
    [49, 19, 1, 1, 68],
    [49, 141, 4, 3, 153],
    [49, 145, 1, 3, 136],
    [50, 4, 14, 1, 85],
    [50, 18, 2, 1, 68],
    [51, 4, 5, 1, 85],
    [51, 9, 1, 1, 68],
    [51, 10, 7, 1, 85],
    [51, 17, 3, 1, 68],
    [51, 140, 1, 2, 85],
    [51, 156, 1, 1, 68],
    [51, 157, 3, 1, 85],
    [52, 4, 6, 1, 85],
    [52, 10, 2, 1, 68],
    [52, 12, 7, 1, 85],
    [52, 19, 1, 1, 68],
    [52, 141, 5, 1, 153],
    [52, 147, 1, 1, 102],
    [52, 148, 8, 1, 85],
    [52, 156, 2, 1, 68],
    [52, 158, 2, 2, 85],
    [53, 4, 3, 1, 85],
    [53, 7, 3, 1, 68],
    [53, 10, 1, 1, 85],
    [53, 11, 1, 1, 68],
    [53, 12, 6, 1, 85],
    [53, 18, 2, 2, 68],
    [53, 140, 1, 1, 102],
    [53, 141, 4, 3, 153],
    [53, 145, 1, 3, 136],
    [53, 147, 2, 5, 102],
    [53, 149, 8, 1, 85],
    [53, 157, 1, 1, 68],
    [54, 4, 4, 3, 85],
    [54, 8, 3, 1, 68],
    [54, 11, 7, 1, 85],
    [54, 140, 1, 1, 85],
    [54, 149, 7, 2, 85],
    [54, 156, 1, 2, 68],
    [54, 157, 3, 2, 85],
    [55, 0, 1, 1, 68],
    [55, 1, 2, 1, 85],
    [55, 8, 2, 1, 68],
    [55, 10, 7, 1, 85],
    [55, 17, 1, 1, 68],
    [55, 18, 1, 1, 85],
    [55, 19, 1, 2, 68],
    [55, 140, 1, 2, 102],
    [56, 0, 3, 34, 85],
    [56, 8, 1, 1, 68],
    [56, 9, 10, 1, 85],
    [56, 141, 5, 1, 153],
    [56, 149, 8, 1, 85],
    [56, 157, 1, 1, 68],
    [56, 158, 2, 2, 85],
    [57, 4, 5, 2, 85],
    [57, 9, 2, 2, 68],
    [57, 11, 7, 1, 85],
    [57, 18, 2, 1, 68],
    [57, 140, 1, 1, 85],
    [57, 141, 4, 7, 153],
    [57, 145, 1, 7, 136],
    [57, 149, 7, 1, 85],
    [57, 156, 2, 1, 68],
    [58, 11, 8, 1, 85],
    [58, 19, 1, 2, 68],
    [58, 140, 1, 4, 102],
    [58, 147, 1, 7, 102],
    [58, 148, 8, 7, 85],
    [58, 156, 1, 2, 68],
    [58, 157, 3, 2, 85],
    [59, 4, 3, 1, 85],
    [59, 7, 1, 1, 68],
    [59, 8, 2, 1, 85],
    [59, 10, 2, 1, 68],
    [59, 12, 7, 1, 85],
    [60, 4, 8, 1, 85],
    [60, 12, 1, 1, 68],
    [60, 13, 5, 1, 85],
    [60, 18, 2, 1, 68],
    [60, 156, 2, 1, 68],
    [60, 158, 2, 1, 85],
    [61, 4, 4, 2, 85],
    [61, 8, 1, 2, 68],
    [61, 9, 8, 1, 85],
    [61, 17, 3, 1, 68],
    [61, 156, 1, 1, 68],
    [61, 157, 3, 1, 85],
    [62, 9, 10, 1, 85],
    [62, 19, 1, 2, 68],
    [62, 140, 1, 2, 85],
    [62, 156, 2, 1, 68],
    [62, 158, 2, 1, 85],
    [63, 4, 6, 2, 85],
    [63, 10, 1, 2, 68],
    [63, 11, 8, 1, 85],
    [63, 156, 1, 1, 68],
    [63, 157, 3, 1, 85],
    [64, 11, 7, 1, 85],
    [64, 18, 2, 2, 68],
    [64, 140, 1, 5, 102],
    [64, 141, 5, 1, 153],
    [64, 156, 2, 1, 68],
    [64, 158, 2, 1, 85],
    [65, 4, 14, 1, 85],
    [65, 141, 4, 5, 153],
    [65, 145, 1, 5, 136],
    [65, 147, 2, 2, 102],
    [65, 149, 7, 2, 85],
    [65, 156, 1, 1, 68],
    [65, 157, 3, 1, 85],
    [66, 4, 4, 1, 85],
    [66, 8, 1, 1, 68],
    [66, 9, 10, 1, 85],
    [66, 19, 1, 5, 68],
    [66, 156, 2, 2, 68],
    [66, 158, 2, 2, 85],
    [67, 4, 1, 3, 85],
    [67, 5, 1, 3, 68],
    [67, 6, 3, 1, 85],
    [67, 9, 2, 1, 68],
    [67, 11, 6, 1, 85],
    [67, 17, 1, 1, 68],
    [67, 18, 1, 1, 85],
    [67, 147, 1, 1, 102],
    [67, 148, 8, 1, 85],
    [68, 6, 4, 1, 85],
    [68, 10, 3, 1, 68],
    [68, 13, 6, 1, 85],
    [68, 20, 59, 3, 34],
    [68, 79, 2, 3, 51],
    [68, 81, 59, 4, 34],
    [68, 147, 2, 2, 102],
    [68, 149, 11, 1, 85],
    [69, 6, 3, 1, 85],
    [69, 9, 3, 1, 68],
    [69, 12, 7, 1, 85],
    [69, 140, 1, 2, 85],
    [69, 149, 7, 1, 85],
    [69, 156, 1, 1, 68],
    [69, 157, 3, 1, 85],
    [70, 4, 4, 2, 85],
    [70, 8, 1, 2, 68],
    [70, 9, 1, 2, 85],
    [70, 10, 1, 2, 68],
    [70, 11, 8, 1, 85],
    [70, 141, 5, 1, 153],
    [70, 147, 1, 1, 102],
    [70, 148, 8, 1, 85],
    [70, 156, 2, 2, 68],
    [70, 158, 2, 2, 85],
    [71, 11, 7, 1, 85],
    [71, 18, 2, 1, 68],
    [71, 20, 58, 1, 34],
    [71, 78, 3, 1, 51],
    [71, 140, 1, 4, 102],
    [71, 141, 4, 1, 153],
    [71, 145, 1, 1, 136],
    [71, 147, 2, 4, 102],
    [71, 149, 7, 4, 85],
    [72, 4, 2, 2, 85],
    [72, 6, 2, 1, 68],
    [72, 8, 2, 1, 85],
    [72, 10, 2, 2, 68],
    [72, 12, 7, 2, 85],
    [72, 19, 1, 49, 68],
    [72, 20, 56, 1, 34],
    [72, 76, 8, 1, 51],
    [72, 84, 56, 1, 34],
    [72, 141, 5, 1, 153],
    [72, 156, 1, 3, 68],
    [72, 157, 3, 3, 85],
    [73, 6, 1, 1, 68],
    [73, 7, 3, 1, 85],
    [73, 20, 54, 1, 34],
    [73, 74, 11, 1, 51],
    [73, 85, 55, 1, 34],
    [73, 141, 4, 2, 153],
    [73, 145, 1, 2, 136],
    [74, 4, 4, 2, 85],
    [74, 8, 1, 2, 68],
    [74, 9, 1, 1, 85],
    [74, 10, 1, 1, 68],
    [74, 11, 8, 1, 85],
    [74, 20, 53, 2, 34],
    [74, 73, 3, 1, 51],
    [74, 76, 3, 1, 34],
    [74, 79, 2, 3, 51],
    [74, 81, 2, 1, 34],
    [74, 83, 3, 1, 51],
    [74, 86, 54, 1, 34],
    [75, 9, 2, 1, 85],
    [75, 11, 1, 1, 68],
    [75, 12, 7, 3, 85],
    [75, 73, 2, 1, 51],
    [75, 75, 4, 1, 34],
    [75, 81, 4, 2, 34],
    [75, 85, 2, 2, 51],
    [75, 87, 53, 2, 34],
    [75, 140, 1, 2, 85],
    [75, 141, 5, 1, 153],
    [75, 147, 1, 4, 102],
    [75, 148, 8, 3, 85],
    [75, 156, 2, 1, 68],
    [75, 158, 2, 1, 85],
    [76, 4, 5, 1, 85],
    [76, 9, 3, 1, 68],
    [76, 20, 52, 6, 34],
    [76, 72, 2, 6, 51],
    [76, 74, 5, 1, 34],
    [76, 141, 2, 1, 153],
    [76, 143, 1, 1, 170],
    [76, 144, 1, 1, 153],
    [76, 145, 1, 6, 136],
    [76, 156, 1, 1, 68],
    [76, 157, 3, 1, 85],
    [77, 4, 7, 1, 85],
    [77, 11, 1, 1, 68],
    [77, 74, 12, 5, 34],
    [77, 86, 2, 5, 51],
    [77, 88, 52, 5, 34],
    [77, 140, 1, 8, 102],
    [77, 141, 4, 5, 153],
    [77, 156, 2, 1, 68],
    [77, 158, 2, 1, 85],
    [78, 4, 4, 1, 85],
    [78, 8, 1, 1, 68],
    [78, 9, 1, 1, 85],
    [78, 10, 1, 1, 68],
    [78, 11, 8, 2, 85],
    [78, 148, 12, 1, 85],
    [79, 4, 5, 1, 85],
    [79, 9, 2, 1, 68],
    [79, 147, 2, 1, 102],
    [79, 149, 7, 1, 85],
    [79, 156, 1, 1, 68],
    [79, 157, 3, 1, 85],
    [80, 4, 4, 1, 85],
    [80, 8, 1, 1, 68],
    [80, 9, 10, 1, 85],
    [80, 147, 1, 4, 102],
    [80, 148, 8, 2, 85],
    [80, 156, 2, 2, 68],
    [80, 158, 2, 2, 85],
    [81, 4, 5, 1, 85],
    [81, 9, 2, 1, 68],
    [81, 11, 8, 1, 85],
    [82, 4, 3, 1, 85],
    [82, 7, 1, 1, 68],
    [82, 8, 11, 1, 85],
    [82, 20, 53, 2, 34],
    [82, 73, 2, 1, 51],
    [82, 75, 10, 1, 34],
    [82, 85, 2, 1, 51],
    [82, 87, 53, 2, 34],
    [82, 141, 5, 1, 153],
    [82, 148, 12, 1, 85],
    [83, 4, 5, 1, 85],
    [83, 9, 1, 1, 68],
    [83, 10, 1, 1, 85],
    [83, 11, 1, 1, 68],
    [83, 12, 7, 2, 85],
    [83, 73, 3, 1, 51],
    [83, 76, 8, 1, 34],
    [83, 84, 3, 1, 51],
    [83, 141, 4, 2, 153],
    [83, 145, 1, 2, 136],
    [83, 148, 8, 1, 85],
    [83, 156, 1, 2, 68],
    [83, 157, 3, 2, 85],
    [84, 4, 3, 1, 85],
    [84, 7, 5, 1, 68],
    [84, 20, 54, 1, 34],
    [84, 74, 3, 1, 51],
    [84, 77, 6, 1, 34],
    [84, 83, 3, 1, 51],
    [84, 86, 54, 1, 34],
    [84, 147, 2, 1, 102],
    [84, 149, 7, 1, 85],
    [85, 4, 6, 1, 85],
    [85, 10, 1, 1, 68],
    [85, 11, 8, 1, 85],
    [85, 20, 55, 1, 34],
    [85, 75, 10, 1, 51],
    [85, 85, 55, 1, 34],
    [85, 140, 1, 2, 85],
    [85, 141, 5, 2, 153],
    [85, 147, 1, 1, 102],
    [85, 148, 12, 1, 85],
    [86, 4, 2, 1, 85],
    [86, 6, 1, 1, 68],
    [86, 7, 12, 1, 85],
    [86, 20, 57, 1, 34],
    [86, 77, 6, 1, 51],
    [86, 83, 57, 1, 34],
    [86, 147, 2, 2, 102],
    [86, 149, 7, 2, 85],
    [86, 156, 1, 1, 68],
    [86, 157, 3, 1, 85],
    [87, 4, 4, 1, 85],
    [87, 8, 1, 1, 68],
    [87, 9, 10, 1, 85],
    [87, 20, 120, 30, 34],
    [87, 140, 1, 1, 102],
    [87, 141, 4, 10, 153],
    [87, 145, 1, 10, 136],
    [87, 156, 2, 1, 68],
    [87, 158, 2, 1, 85],
    [88, 4, 6, 1, 85],
    [88, 10, 1, 1, 68],
    [88, 11, 8, 1, 85],
    [88, 140, 1, 1, 85],
    [88, 147, 1, 2, 102],
    [88, 148, 12, 1, 85],
    [89, 4, 1, 1, 85],
    [89, 5, 1, 1, 68],
    [89, 6, 3, 1, 85],
    [89, 9, 1, 2, 68],
    [89, 10, 9, 1, 85],
    [89, 140, 1, 13, 102],
    [89, 148, 9, 1, 85],
    [89, 157, 1, 1, 68],
    [89, 158, 2, 1, 85],
    [90, 0, 2, 1, 85],
    [90, 2, 2, 1, 68],
    [90, 4, 5, 1, 85],
    [90, 10, 1, 1, 85],
    [90, 11, 1, 1, 68],
    [90, 12, 7, 1, 85],
    [90, 147, 2, 1, 102],
    [90, 149, 7, 1, 85],
    [90, 156, 1, 1, 68],
    [90, 157, 3, 1, 85],
    [91, 0, 3, 8, 85],
    [91, 3, 1, 8, 68],
    [91, 4, 2, 1, 85],
    [91, 6, 1, 1, 68],
    [91, 7, 12, 1, 85],
    [91, 147, 1, 2, 102],
    [91, 148, 9, 1, 85],
    [91, 157, 1, 1, 68],
    [91, 158, 2, 2, 85],
    [92, 4, 3, 1, 85],
    [92, 7, 1, 1, 68],
    [92, 8, 2, 1, 85],
    [92, 10, 1, 1, 68],
    [92, 11, 8, 2, 85],
    [92, 148, 8, 1, 85],
    [92, 156, 2, 1, 68],
    [93, 4, 5, 1, 85],
    [93, 9, 2, 1, 68],
    [93, 147, 2, 1, 102],
    [93, 149, 11, 1, 85],
    [94, 4, 4, 1, 85],
    [94, 8, 1, 1, 68],
    [94, 9, 2, 1, 85],
    [94, 11, 1, 1, 68],
    [94, 12, 7, 1, 85],
    [94, 147, 1, 6, 102],
    [94, 148, 8, 5, 85],
    [94, 156, 1, 2, 68],
    [94, 157, 3, 2, 85],
    [95, 4, 5, 2, 85],
    [95, 9, 1, 2, 68],
    [95, 10, 9, 2, 85],
    [96, 156, 2, 3, 68],
    [96, 158, 2, 1, 85],
    [97, 4, 15, 1, 85],
    [97, 141, 5, 1, 153],
    [97, 158, 1, 1, 85],
    [97, 159, 1, 1, 102],
    [98, 4, 5, 1, 85],
    [98, 9, 1, 1, 68],
    [98, 10, 9, 1, 85],
    [98, 141, 4, 2, 153],
    [98, 145, 1, 8, 136],
    [98, 158, 2, 1, 85],
    [99, 0, 2, 1, 85],
    [99, 2, 2, 1, 68],
    [99, 4, 6, 3, 85],
    [99, 10, 1, 1, 68],
    [99, 11, 8, 1, 85],
    [99, 148, 12, 1, 85],
    [100, 0, 3, 23, 85],
    [100, 3, 1, 23, 68],
    [100, 10, 2, 2, 68],
    [100, 12, 7, 3, 85],
    [100, 141, 2, 1, 153],
    [100, 143, 1, 1, 170],
    [100, 144, 1, 1, 153],
    [100, 147, 2, 1, 102],
    [100, 149, 7, 1, 85],
    [100, 156, 2, 2, 68],
    [100, 158, 2, 5, 85],
    [101, 141, 4, 5, 153],
    [101, 147, 1, 1, 102],
    [101, 148, 8, 1, 85],
    [102, 4, 3, 1, 85],
    [102, 7, 1, 1, 68],
    [102, 8, 3, 1, 85],
    [102, 11, 1, 1, 68],
    [102, 140, 1, 2, 85],
    [102, 147, 2, 1, 102],
    [102, 149, 8, 1, 85],
    [102, 157, 1, 1, 68],
    [103, 4, 15, 2, 85],
    [103, 147, 1, 6, 102],
    [103, 148, 8, 6, 85],
    [103, 156, 2, 2, 68],
    [104, 140, 1, 3, 102],
    [105, 4, 2, 1, 85],
    [105, 6, 1, 1, 68],
    [105, 7, 12, 1, 85],
    [105, 156, 1, 2, 68],
    [105, 157, 3, 2, 85],
    [106, 4, 4, 1, 85],
    [106, 8, 1, 1, 68],
    [106, 9, 10, 1, 85],
    [106, 141, 5, 2, 153],
    [107, 4, 15, 1, 85],
    [107, 140, 1, 1, 85],
    [107, 156, 2, 3, 68],
    [107, 158, 2, 4, 85],
    [108, 4, 6, 1, 85],
    [108, 10, 2, 1, 68],
    [108, 12, 7, 1, 85],
    [108, 140, 1, 3, 102],
    [108, 141, 4, 13, 153],
    [108, 145, 1, 14, 136],
    [109, 4, 5, 1, 85],
    [109, 9, 2, 1, 68],
    [109, 11, 8, 1, 85],
    [109, 147, 2, 2, 102],
    [109, 149, 7, 1, 85],
    [110, 4, 15, 1, 85],
    [110, 149, 8, 1, 85],
    [110, 157, 1, 1, 68],
    [111, 4, 6, 1, 85],
    [111, 10, 1, 1, 68],
    [111, 11, 8, 1, 85],
    [111, 140, 1, 1, 85],
    [111, 147, 1, 4, 102],
    [111, 148, 8, 3, 85],
    [111, 156, 1, 3, 68],
    [111, 157, 3, 3, 85],
    [112, 4, 1, 1, 85],
    [112, 5, 1, 1, 68],
    [112, 6, 13, 1, 85],
    [112, 140, 1, 4, 102],
    [113, 4, 4, 1, 85],
    [113, 8, 1, 1, 68],
    [113, 9, 10, 1, 85],
    [114, 4, 15, 3, 85],
    [114, 148, 9, 1, 85],
    [114, 157, 1, 1, 68],
    [114, 158, 2, 1, 85],
    [115, 147, 2, 1, 102],
    [115, 149, 7, 1, 85],
    [115, 156, 1, 1, 68],
    [115, 157, 3, 1, 85],
    [116, 140, 1, 1, 85],
    [116, 147, 1, 8, 102],
    [116, 148, 12, 4, 85],
    [117, 4, 4, 1, 85],
    [117, 8, 1, 1, 68],
    [117, 9, 10, 1, 85],
    [117, 20, 108, 1, 34],
    [117, 128, 2, 1, 17],
    [117, 130, 10, 1, 34],
    [117, 140, 1, 5, 102],
    [118, 4, 1, 1, 85],
    [118, 5, 1, 1, 68],
    [118, 6, 13, 1, 85],
    [118, 20, 9, 2, 34],
    [118, 29, 1, 2, 17],
    [118, 30, 99, 1, 34],
    [118, 129, 2, 1, 17],
    [118, 131, 9, 2, 34],
    [119, 4, 15, 2, 85],
    [119, 30, 98, 1, 34],
    [119, 128, 1, 1, 51],
    [119, 129, 1, 1, 34],
    [119, 130, 1, 1, 17],
    [120, 20, 8, 2, 34],
    [120, 28, 1, 2, 17],
    [120, 29, 100, 2, 34],
    [120, 129, 1, 2, 51],
    [120, 130, 2, 2, 17],
    [120, 132, 8, 1, 34],
    [120, 148, 8, 2, 85],
    [120, 156, 2, 2, 68],
    [120, 158, 2, 2, 85],
    [121, 4, 1, 1, 85],
    [121, 5, 1, 1, 68],
    [121, 6, 8, 1, 85],
    [121, 14, 2, 1, 102],
    [121, 16, 4, 1, 85],
    [121, 132, 7, 1, 34],
    [121, 139, 1, 2, 51],
    [121, 141, 1, 1, 136],
    [121, 142, 3, 1, 153],
    [122, 4, 10, 5, 85],
    [122, 14, 5, 2, 102],
    [122, 19, 1, 2, 85],
    [122, 20, 1, 2, 51],
    [122, 21, 7, 1, 34],
    [122, 28, 2, 1, 17],
    [122, 30, 1, 1, 51],
    [122, 31, 97, 1, 34],
    [122, 128, 2, 1, 51],
    [122, 130, 1, 2, 17],
    [122, 131, 8, 2, 34],
    [122, 140, 1, 2, 119],
    [122, 141, 5, 2, 136],
    [122, 148, 12, 1, 85],
    [123, 0, 2, 1, 85],
    [123, 2, 2, 1, 68],
    [123, 21, 8, 1, 34],
    [123, 29, 1, 1, 17],
    [123, 30, 1, 1, 34],
    [123, 31, 95, 1, 51],
    [123, 126, 1, 1, 34],
    [123, 127, 2, 1, 51],
    [123, 129, 1, 1, 34],
    [123, 139, 1, 1, 68],
    [123, 148, 8, 1, 85],
    [123, 156, 2, 1, 68],
    [123, 158, 2, 2, 85],
    [124, 0, 3, 4, 85],
    [124, 3, 1, 4, 68],
    [124, 14, 6, 1, 102],
    [124, 20, 1, 1, 68],
    [124, 21, 9, 1, 34],
    [124, 30, 1, 1, 17],
    [124, 31, 98, 1, 34],
    [124, 129, 1, 1, 17],
    [124, 130, 9, 1, 34],
    [124, 139, 1, 3, 85],
    [124, 140, 2, 1, 119],
    [124, 142, 3, 1, 136],
    [124, 145, 1, 1, 119],
    [124, 146, 1, 2, 102],
    [124, 147, 10, 1, 85],
    [124, 157, 1, 1, 68],
    [125, 14, 1, 3, 102],
    [125, 15, 4, 1, 119],
    [125, 19, 1, 1, 102],
    [125, 20, 1, 1, 85],
    [125, 21, 117, 1, 34],
    [125, 138, 1, 1, 51],
    [125, 140, 1, 1, 102],
    [125, 141, 2, 1, 119],
    [125, 143, 1, 1, 136],
    [125, 144, 2, 1, 119],
    [125, 147, 13, 2, 85],
    [126, 15, 5, 1, 119],
    [126, 20, 1, 1, 102],
    [126, 21, 1, 1, 51],
    [126, 22, 116, 1, 34],
    [126, 138, 1, 1, 68],
    [126, 140, 2, 1, 102],
    [126, 142, 3, 1, 119],
    [126, 145, 2, 1, 102],
    [127, 4, 5, 2, 85],
    [127, 9, 1, 2, 68],
    [127, 10, 4, 2, 85],
    [127, 15, 6, 1, 119],
    [127, 21, 1, 1, 68],
    [127, 22, 115, 1, 34],
    [127, 137, 1, 1, 51],
    [127, 138, 3, 1, 85],
    [127, 141, 2, 1, 102],
    [127, 143, 1, 1, 119],
    [127, 144, 2, 1, 102],
    [127, 146, 14, 2, 85],
    [128, 0, 2, 1, 85],
    [128, 2, 2, 1, 68],
    [128, 14, 2, 2, 102],
    [128, 16, 1, 3, 119],
    [128, 17, 2, 1, 136],
    [128, 19, 2, 1, 119],
    [128, 21, 1, 1, 102],
    [128, 22, 1, 1, 51],
    [128, 23, 114, 1, 34],
    [128, 137, 2, 1, 68],
    [128, 139, 2, 1, 85],
    [128, 141, 5, 1, 102],
    [129, 0, 3, 21, 85],
    [129, 3, 1, 21, 68],
    [129, 4, 10, 1, 85],
    [129, 17, 5, 1, 136],
    [129, 22, 1, 1, 85],
    [129, 23, 1, 1, 51],
    [129, 24, 112, 1, 34],
    [129, 136, 1, 1, 68],
    [129, 137, 1, 1, 85],
    [129, 138, 2, 1, 68],
    [129, 140, 3, 1, 85],
    [129, 143, 2, 1, 102],
    [129, 145, 15, 1, 85],
    [130, 4, 11, 2, 85],
    [130, 15, 1, 1, 102],
    [130, 17, 6, 1, 136],
    [130, 23, 1, 1, 85],
    [130, 24, 1, 1, 51],
    [130, 25, 110, 1, 34],
    [130, 135, 1, 1, 68],
    [130, 136, 1, 1, 85],
    [130, 137, 4, 1, 68],
    [130, 141, 15, 1, 85],
    [130, 156, 1, 1, 68],
    [130, 157, 3, 1, 85],
    [131, 15, 2, 1, 102],
    [131, 17, 1, 2, 119],
    [131, 18, 2, 2, 136],
    [131, 20, 1, 1, 153],
    [131, 21, 3, 1, 136],
    [131, 24, 1, 1, 85],
    [131, 25, 1, 1, 51],
    [131, 26, 108, 1, 34],
    [131, 134, 1, 1, 68],
    [131, 135, 1, 1, 85],
    [131, 136, 5, 1, 68],
    [131, 141, 19, 1, 85],
    [132, 4, 12, 1, 85],
    [132, 16, 1, 1, 102],
    [132, 20, 4, 1, 153],
    [132, 24, 1, 1, 136],
    [132, 25, 1, 1, 102],
    [132, 26, 1, 1, 68],
    [132, 27, 1, 1, 51],
    [132, 28, 104, 1, 34],
    [132, 132, 1, 1, 68],
    [132, 133, 1, 1, 85],
    [132, 134, 7, 1, 68],
    [132, 141, 15, 2, 85],
    [132, 156, 1, 1, 68],
    [132, 157, 3, 1, 85],
    [133, 4, 1, 1, 85],
    [133, 5, 1, 1, 68],
    [133, 6, 10, 1, 85],
    [133, 16, 2, 1, 102],
    [133, 18, 1, 1, 119],
    [133, 19, 1, 1, 136],
    [133, 20, 6, 1, 153],
    [133, 26, 1, 1, 136],
    [133, 27, 1, 1, 102],
    [133, 28, 1, 1, 68],
    [133, 29, 1, 1, 51],
    [133, 30, 99, 1, 34],
    [133, 129, 1, 1, 51],
    [133, 130, 1, 1, 68],
    [133, 131, 1, 1, 85],
    [133, 132, 5, 1, 68],
    [133, 137, 1, 1, 51],
    [133, 138, 3, 1, 68],
    [133, 156, 2, 1, 68],
    [133, 158, 2, 1, 85],
    [134, 4, 13, 1, 85],
    [134, 17, 2, 1, 102],
    [134, 19, 1, 1, 119],
    [134, 20, 1, 1, 136],
    [134, 21, 7, 1, 153],
    [134, 28, 1, 1, 136],
    [134, 29, 1, 1, 119],
    [134, 30, 2, 1, 85],
    [134, 32, 95, 1, 68],
    [134, 127, 2, 1, 85],
    [134, 129, 2, 1, 68],
    [134, 131, 5, 1, 51],
    [134, 136, 2, 1, 68],
    [134, 138, 1, 1, 51],
    [134, 139, 2, 1, 68],
    [134, 141, 19, 1, 85],
    [135, 4, 14, 1, 85],
    [135, 18, 1, 1, 102],
    [135, 19, 2, 1, 119],
    [135, 21, 1, 1, 136],
    [135, 22, 8, 1, 153],
    [135, 30, 2, 2, 136],
    [135, 32, 1, 1, 119],
    [135, 33, 32, 1, 102],
    [135, 65, 1, 1, 85],
    [135, 66, 4, 1, 102],
    [135, 70, 1, 1, 85],
    [135, 71, 14, 1, 102],
    [135, 85, 1, 1, 85],
    [135, 86, 1, 1, 102],
    [135, 87, 1, 1, 85],
    [135, 88, 2, 1, 102],
    [135, 90, 1, 1, 85],
    [135, 91, 4, 1, 102],
    [135, 95, 1, 1, 85],
    [135, 96, 2, 1, 102],
    [135, 98, 3, 1, 85],
    [135, 101, 3, 1, 102],
    [135, 104, 1, 1, 85],
    [135, 105, 3, 1, 102],
    [135, 108, 2, 1, 85],
    [135, 110, 1, 1, 102],
    [135, 111, 2, 1, 85],
    [135, 113, 1, 1, 102],
    [135, 114, 3, 1, 85],
    [135, 117, 2, 1, 102],
    [135, 119, 4, 1, 85],
    [135, 123, 2, 1, 102],
    [135, 125, 2, 1, 85],
    [135, 127, 2, 1, 68],
    [135, 129, 8, 1, 51],
    [135, 137, 3, 1, 68],
    [135, 140, 17, 1, 85],
    [135, 157, 1, 1, 68],
    [135, 158, 2, 2, 85],
    [136, 4, 15, 2, 85],
    [136, 19, 2, 1, 102],
    [136, 21, 1, 1, 119],
    [136, 22, 1, 1, 136],
    [136, 23, 7, 1, 153],
    [136, 32, 3, 1, 119],
    [136, 35, 90, 1, 102],
    [136, 125, 3, 1, 85],
    [136, 128, 3, 1, 68],
    [136, 131, 6, 1, 51],
    [136, 137, 2, 1, 68],
    [136, 139, 17, 1, 85],
    [136, 156, 2, 1, 68],
    [137, 19, 3, 1, 102],
    [137, 22, 1, 1, 119],
    [137, 23, 2, 1, 136],
    [137, 25, 6, 1, 153],
    [137, 31, 2, 1, 136],
    [137, 33, 4, 1, 119],
    [137, 37, 2, 1, 102],
    [137, 39, 8, 1, 119],
    [137, 47, 1, 1, 102],
    [137, 48, 1, 1, 119],
    [137, 49, 2, 1, 102],
    [137, 51, 1, 1, 119],
    [137, 52, 2, 1, 102],
    [137, 54, 2, 1, 119],
    [137, 56, 1, 1, 102],
    [137, 57, 3, 1, 119],
    [137, 60, 1, 1, 102],
    [137, 61, 1, 1, 119],
    [137, 62, 1, 1, 102],
    [137, 63, 1, 1, 119],
    [137, 64, 3, 1, 102],
    [137, 67, 1, 1, 119],
    [137, 68, 5, 1, 102],
    [137, 73, 4, 1, 119],
    [137, 77, 1, 1, 102],
    [137, 78, 1, 1, 119],
    [137, 79, 2, 1, 102],
    [137, 81, 1, 1, 119],
    [137, 82, 10, 1, 102],
    [137, 92, 2, 1, 119],
    [137, 94, 3, 1, 102],
    [137, 97, 1, 1, 119],
    [137, 98, 2, 1, 102],
    [137, 100, 1, 1, 119],
    [137, 101, 26, 1, 102],
    [137, 127, 1, 1, 85],
    [137, 128, 1, 1, 68],
    [137, 129, 1, 1, 85],
    [137, 130, 2, 1, 68],
    [137, 132, 1, 1, 51],
    [137, 133, 1, 1, 68],
    [137, 134, 1, 1, 51],
    [137, 135, 2, 1, 68],
    [137, 137, 23, 1, 85],
    [138, 4, 17, 1, 85],
    [138, 21, 2, 1, 102],
    [138, 23, 2, 1, 119],
    [138, 25, 8, 1, 136],
    [138, 33, 37, 1, 119],
    [138, 70, 1, 1, 102],
    [138, 71, 15, 1, 119],
    [138, 86, 1, 1, 102],
    [138, 87, 6, 1, 119],
    [138, 93, 1, 1, 102],
    [138, 94, 1, 2, 119],
    [138, 95, 2, 1, 102],
    [138, 97, 2, 1, 119],
    [138, 99, 1, 1, 102],
    [138, 100, 2, 1, 119],
    [138, 102, 3, 1, 102],
    [138, 105, 3, 1, 119],
    [138, 108, 1, 1, 102],
    [138, 109, 2, 1, 119],
    [138, 111, 3, 1, 102],
    [138, 114, 2, 1, 119],
    [138, 116, 2, 1, 102],
    [138, 118, 5, 1, 119],
    [138, 123, 4, 1, 102],
    [138, 127, 4, 1, 85],
    [138, 131, 5, 1, 68],
    [138, 136, 20, 1, 85],
    [138, 156, 1, 2, 68],
    [138, 157, 3, 2, 85],
    [139, 4, 19, 1, 85],
    [139, 23, 3, 1, 102],
    [139, 26, 3, 1, 119],
    [139, 29, 4, 1, 136],
    [139, 33, 10, 1, 119],
    [139, 43, 1, 1, 102],
    [139, 44, 7, 1, 119],
    [139, 51, 1, 1, 102],
    [139, 52, 2, 1, 119],
    [139, 54, 1, 1, 102],
    [139, 55, 7, 1, 119],
    [139, 62, 2, 1, 102],
    [139, 64, 4, 1, 119],
    [139, 68, 3, 1, 102],
    [139, 71, 11, 1, 119],
    [139, 82, 1, 1, 102],
    [139, 83, 1, 1, 119],
    [139, 84, 4, 1, 102],
    [139, 88, 4, 1, 119],
    [139, 92, 2, 1, 102],
    [139, 95, 8, 1, 102],
    [139, 103, 1, 1, 119],
    [139, 104, 5, 1, 102],
    [139, 109, 1, 1, 119],
    [139, 110, 12, 1, 102],
    [139, 122, 2, 1, 119],
    [139, 124, 4, 1, 102],
    [139, 128, 28, 1, 85],
    [140, 4, 20, 1, 85],
    [140, 24, 7, 1, 102],
    [140, 31, 4, 1, 119],
    [140, 35, 6, 1, 102],
    [140, 41, 1, 1, 119],
    [140, 42, 2, 1, 102],
    [140, 44, 1, 1, 119],
    [140, 45, 81, 1, 102],
    [140, 126, 1, 1, 85],
    [140, 127, 1, 1, 102],
    [140, 128, 31, 1, 85],
    [140, 159, 1, 1, 102],
    [141, 4, 23, 1, 85],
    [141, 27, 1, 1, 102],
    [141, 28, 1, 1, 85],
    [141, 29, 6, 1, 102],
    [141, 35, 2, 1, 85],
    [141, 37, 6, 1, 102],
    [141, 43, 2, 1, 85],
    [141, 45, 2, 1, 102],
    [141, 47, 1, 1, 85],
    [141, 48, 8, 1, 102],
    [141, 56, 7, 1, 85],
    [141, 63, 2, 1, 102],
    [141, 65, 3, 1, 85],
    [141, 68, 1, 1, 102],
    [141, 69, 4, 1, 85],
    [141, 73, 4, 1, 102],
    [141, 77, 2, 1, 85],
    [141, 79, 3, 1, 102],
    [141, 82, 6, 1, 85],
    [141, 88, 2, 1, 102],
    [141, 90, 4, 1, 85],
    [141, 94, 1, 1, 102],
    [141, 95, 2, 1, 85],
    [141, 97, 1, 1, 102],
    [141, 98, 8, 1, 85],
    [141, 106, 2, 1, 102],
    [141, 108, 1, 1, 85],
    [141, 109, 1, 1, 102],
    [141, 110, 1, 1, 85],
    [141, 111, 2, 1, 102],
    [141, 113, 6, 1, 85],
    [141, 119, 1, 2, 102],
    [141, 120, 1, 1, 85],
    [141, 121, 4, 1, 102],
    [141, 125, 31, 1, 85],
    [141, 156, 1, 1, 68],
    [141, 157, 3, 1, 85],
    [142, 4, 24, 1, 85],
    [142, 28, 17, 1, 102],
    [142, 45, 2, 1, 85],
    [142, 47, 5, 1, 102],
    [142, 52, 2, 1, 85],
    [142, 54, 1, 1, 102],
    [142, 55, 1, 1, 85],
    [142, 56, 1, 1, 102],
    [142, 57, 2, 1, 85],
    [142, 59, 2, 1, 102],
    [142, 61, 1, 1, 85],
    [142, 62, 2, 1, 102],
    [142, 64, 2, 1, 85],
    [142, 66, 5, 1, 102],
    [142, 71, 1, 1, 85],
    [142, 72, 1, 1, 102],
    [142, 73, 1, 1, 85],
    [142, 74, 3, 1, 102],
    [142, 77, 1, 1, 85],
    [142, 78, 2, 1, 102],
    [142, 80, 1, 1, 85],
    [142, 81, 1, 1, 102],
    [142, 82, 2, 1, 85],
    [142, 84, 1, 1, 102],
    [142, 85, 4, 1, 85],
    [142, 89, 2, 1, 102],
    [142, 91, 2, 1, 85],
    [142, 93, 1, 1, 102],
    [142, 94, 2, 1, 85],
    [142, 96, 2, 1, 102],
    [142, 98, 6, 1, 85],
    [142, 104, 2, 1, 102],
    [142, 106, 2, 1, 85],
    [142, 108, 1, 1, 102],
    [142, 109, 3, 1, 85],
    [142, 112, 1, 1, 102],
    [142, 113, 3, 1, 85],
    [142, 116, 1, 1, 102],
    [142, 117, 2, 1, 85],
    [142, 120, 2, 1, 85],
    [142, 122, 1, 1, 102],
    [142, 123, 1, 1, 85],
    [142, 124, 1, 1, 102],
    [142, 125, 35, 1, 85],
    [143, 4, 5, 1, 85],
    [143, 9, 1, 1, 51],
    [143, 10, 1, 1, 34],
    [143, 11, 9, 1, 51],
    [143, 20, 5, 1, 34],
    [143, 25, 59, 1, 51],
    [143, 84, 4, 1, 68],
    [143, 88, 44, 1, 51],
    [143, 132, 18, 1, 34],
    [143, 150, 1, 1, 68],
    [143, 151, 5, 2, 85],
    [143, 156, 1, 2, 68],
    [143, 157, 3, 2, 85],
    [144, 4, 4, 3, 85],
    [144, 8, 1, 3, 68],
    [144, 9, 5, 1, 17],
    [144, 14, 3, 1, 34],
    [144, 17, 68, 1, 17],
    [144, 85, 2, 1, 34],
    [144, 87, 62, 1, 17],
    [144, 149, 1, 1, 0],
    [144, 150, 1, 1, 17],
    [145, 9, 9, 1, 17],
    [145, 18, 2, 1, 34],
    [145, 20, 62, 1, 17],
    [145, 82, 2, 1, 34],
    [145, 84, 4, 1, 17],
    [145, 88, 3, 1, 34],
    [145, 91, 60, 1, 17],
    [145, 151, 1, 1, 51],
    [145, 152, 8, 2, 85],
    [146, 9, 140, 1, 34],
    [146, 149, 2, 1, 17],
    [146, 151, 1, 1, 68],
    [147, 4, 5, 1, 85],
    [147, 9, 1, 1, 51],
    [147, 10, 140, 1, 34],
    [147, 150, 1, 1, 51],
    [147, 151, 9, 1, 85],
    [148, 4, 6, 1, 85],
    [148, 10, 17, 1, 68],
    [148, 27, 1, 1, 85],
    [148, 28, 13, 1, 68],
    [148, 41, 1, 1, 85],
    [148, 42, 19, 1, 68],
    [148, 61, 1, 1, 85],
    [148, 62, 27, 1, 68],
    [148, 89, 1, 1, 85],
    [148, 90, 19, 1, 68],
    [148, 109, 1, 1, 85],
    [148, 110, 12, 1, 68],
    [148, 122, 1, 1, 85],
    [148, 123, 6, 1, 68],
    [148, 129, 1, 1, 85],
    [148, 130, 2, 1, 68],
    [148, 132, 1, 1, 85],
    [148, 133, 3, 1, 68],
    [148, 136, 1, 1, 85],
    [148, 137, 1, 1, 68],
    [148, 138, 2, 1, 85],
    [148, 140, 1, 1, 68],
    [148, 141, 2, 1, 85],
    [148, 143, 1, 1, 68],
    [148, 144, 1, 1, 85],
    [148, 145, 3, 1, 68],
    [148, 148, 12, 1, 85],
    [149, 4, 152, 1, 85],
    [149, 156, 2, 1, 68],
    [149, 158, 2, 1, 85],
    [150, 0, 5, 1, 85],
    [150, 5, 3, 1, 68],
    [150, 8, 1, 1, 85],
    [150, 9, 4, 1, 68],
    [150, 13, 3, 1, 85],
    [150, 16, 2, 1, 68],
    [150, 18, 1, 1, 85],
    [150, 19, 3, 1, 68],
    [150, 22, 3, 1, 85],
    [150, 25, 1, 1, 68],
    [150, 26, 1, 1, 85],
    [150, 27, 4, 1, 68],
    [150, 31, 1, 1, 85],
    [150, 32, 4, 1, 68],
    [150, 36, 3, 1, 85],
    [150, 39, 2, 1, 68],
    [150, 41, 4, 1, 85],
    [150, 45, 3, 1, 68],
    [150, 48, 1, 1, 85],
    [150, 49, 3, 1, 68],
    [150, 52, 2, 1, 85],
    [150, 54, 2, 1, 68],
    [150, 56, 2, 1, 85],
    [150, 58, 1, 1, 68],
    [150, 59, 2, 1, 85],
    [150, 61, 3, 1, 68],
    [150, 64, 1, 1, 85],
    [150, 65, 5, 1, 68],
    [150, 70, 3, 1, 85],
    [150, 73, 3, 1, 68],
    [150, 76, 1, 1, 85],
    [150, 77, 1, 1, 68],
    [150, 78, 1, 1, 85],
    [150, 79, 3, 1, 68],
    [150, 82, 1, 1, 85],
    [150, 83, 2, 1, 68],
    [150, 85, 1, 1, 85],
    [150, 86, 1, 1, 68],
    [150, 87, 2, 1, 85],
    [150, 89, 1, 1, 68],
    [150, 90, 1, 1, 85],
    [150, 91, 2, 1, 68],
    [150, 93, 2, 1, 85],
    [150, 95, 1, 1, 68],
    [150, 96, 1, 1, 85],
    [150, 97, 4, 1, 68],
    [150, 101, 5, 1, 85],
    [150, 106, 1, 1, 68],
    [150, 107, 6, 1, 85],
    [150, 113, 2, 1, 68],
    [150, 115, 2, 1, 85],
    [150, 117, 1, 1, 68],
    [150, 118, 4, 1, 85],
    [150, 122, 1, 1, 68],
    [150, 123, 3, 1, 85],
    [150, 126, 2, 1, 68],
    [150, 128, 3, 1, 85],
    [150, 131, 2, 1, 68],
    [150, 133, 1, 1, 85],
    [150, 134, 2, 1, 68],
    [150, 136, 2, 1, 85],
    [150, 138, 2, 1, 68],
    [150, 140, 1, 1, 85],
    [150, 141, 2, 1, 68],
    [150, 143, 8, 1, 85],
    [150, 151, 3, 1, 68],
    [150, 154, 1, 1, 85],
    [150, 155, 1, 1, 68],
    [150, 156, 1, 1, 51],
    [150, 157, 3, 1, 85],
    [151, 0, 4, 1, 85],
    [151, 4, 152, 1, 68],
    [151, 156, 4, 1, 85],
    [152, 0, 160, 2, 85],
    [154, 0, 5, 1, 85],
    [154, 5, 35, 1, 68],
    [154, 40, 1, 1, 51],
    [154, 41, 100, 1, 68],
    [154, 141, 3, 1, 85],
    [154, 144, 11, 1, 68],
    [154, 155, 1, 1, 102],
    [154, 156, 3, 1, 85],
    [154, 159, 1, 1, 102],
    [155, 0, 3, 1, 85],
    [155, 3, 1, 1, 119],
    [155, 4, 1, 1, 68],
    [155, 5, 123, 1, 51],
    [155, 128, 1, 1, 68],
    [155, 129, 1, 1, 85],
    [155, 130, 10, 1, 68],
    [155, 140, 2, 1, 85],
    [155, 142, 2, 1, 68],
    [155, 144, 1, 1, 85],
    [155, 145, 1, 1, 68],
    [155, 146, 1, 1, 51],
    [155, 147, 1, 1, 68],
    [155, 148, 1, 1, 51],
    [155, 149, 6, 1, 68],
    [155, 155, 1, 1, 85],
    [155, 156, 1, 1, 136],
    [155, 157, 1, 2, 102],
    [155, 158, 2, 2, 85],
    [156, 0, 1, 2, 85],
    [156, 1, 1, 2, 68],
    [156, 2, 1, 2, 102],
    [156, 3, 1, 3, 85],
    [156, 4, 1, 3, 51],
    [156, 5, 122, 1, 68],
    [156, 127, 1, 2, 51],
    [156, 128, 3, 2, 68],
    [156, 131, 2, 1, 85],
    [156, 133, 1, 1, 68],
    [156, 134, 1, 1, 51],
    [156, 135, 3, 1, 85],
    [156, 138, 2, 1, 68],
    [156, 140, 9, 1, 85],
    [156, 149, 3, 1, 68],
    [156, 152, 1, 2, 85],
    [156, 153, 1, 1, 68],
    [156, 154, 1, 1, 85],
    [156, 155, 1, 1, 68],
    [156, 156, 1, 1, 119],
    [157, 5, 3, 1, 68],
    [157, 8, 6, 1, 51],
    [157, 14, 2, 1, 68],
    [157, 16, 1, 1, 51],
    [157, 17, 3, 1, 68],
    [157, 20, 4, 1, 51],
    [157, 24, 1, 1, 68],
    [157, 25, 2, 1, 51],
    [157, 27, 2, 1, 68],
    [157, 29, 1, 1, 51],
    [157, 30, 4, 1, 68],
    [157, 34, 3, 1, 51],
    [157, 37, 1, 1, 68],
    [157, 38, 3, 1, 51],
    [157, 41, 6, 1, 68],
    [157, 47, 1, 1, 51],
    [157, 48, 10, 1, 68],
    [157, 58, 2, 1, 51],
    [157, 60, 3, 1, 68],
    [157, 63, 1, 1, 51],
    [157, 64, 8, 1, 68],
    [157, 72, 2, 1, 51],
    [157, 74, 10, 1, 68],
    [157, 84, 1, 1, 51],
    [157, 85, 4, 1, 68],
    [157, 89, 1, 1, 51],
    [157, 90, 37, 1, 68],
    [157, 131, 1, 1, 85],
    [157, 132, 1, 1, 68],
    [157, 133, 2, 1, 85],
    [157, 135, 2, 1, 68],
    [157, 137, 1, 1, 85],
    [157, 138, 1, 1, 68],
    [157, 139, 1, 2, 51],
    [157, 140, 5, 1, 85],
    [157, 145, 5, 1, 68],
    [157, 150, 1, 1, 85],
    [157, 151, 1, 1, 68],
    [157, 153, 3, 1, 68],
    [157, 156, 2, 1, 102],
    [157, 158, 1, 1, 68],
    [157, 159, 1, 2, 85],
    [158, 0, 1, 1, 119],
    [158, 1, 2, 1, 102],
    [158, 5, 1, 1, 68],
    [158, 6, 1, 1, 51],
    [158, 7, 6, 1, 68],
    [158, 13, 2, 1, 51],
    [158, 15, 6, 1, 68],
    [158, 21, 2, 1, 51],
    [158, 23, 1, 1, 68],
    [158, 24, 11, 1, 51],
    [158, 35, 3, 1, 68],
    [158, 38, 2, 1, 51],
    [158, 40, 1, 1, 68],
    [158, 41, 3, 1, 51],
    [158, 44, 1, 1, 68],
    [158, 45, 5, 1, 51],
    [158, 50, 3, 1, 68],
    [158, 53, 15, 1, 51],
    [158, 68, 1, 1, 68],
    [158, 69, 3, 1, 51],
    [158, 72, 1, 1, 68],
    [158, 73, 10, 1, 51],
    [158, 83, 1, 1, 68],
    [158, 84, 8, 1, 51],
    [158, 92, 2, 1, 68],
    [158, 94, 35, 1, 51],
    [158, 129, 3, 1, 68],
    [158, 132, 1, 1, 51],
    [158, 133, 3, 1, 68],
    [158, 136, 1, 1, 51],
    [158, 137, 2, 1, 68],
    [158, 140, 1, 1, 68],
    [158, 141, 3, 1, 85],
    [158, 144, 1, 1, 68],
    [158, 145, 5, 1, 51],
    [158, 150, 2, 1, 68],
    [158, 152, 1, 1, 51],
    [158, 153, 2, 1, 68],
    [158, 155, 1, 1, 51],
    [158, 156, 1, 1, 102],
    [158, 157, 1, 1, 119],
    [158, 158, 1, 1, 102],
    [159, 0, 1, 1, 102],
    [159, 1, 1, 1, 85],
    [159, 2, 2, 1, 102],
    [159, 4, 138, 1, 68],
    [159, 142, 1, 1, 85],
    [159, 143, 13, 1, 68],
    [159, 156, 1, 1, 119],
    [159, 157, 1, 1, 102],
    [159, 158, 2, 1, 85]
];

module gigabyte_top_ai_nano_bottom_projection(width = 150, depth = 150, thickness = 0.05) {
    pixel_x = width / gigabyte_top_ai_nano_projection_size;
    pixel_y = depth / gigabyte_top_ai_nano_projection_size;

    for (rect = gigabyte_top_ai_nano_projection_rectangles) {
        shade = rect[4] / 255;
        color([shade, shade, shade])
            translate([rect[1] * pixel_x,
                       (gigabyte_top_ai_nano_projection_size - rect[0] - rect[3]) * pixel_y,
                       -thickness])
                cube([rect[2] * pixel_x + 0.01,
                      rect[3] * pixel_y + 0.01,
                      thickness]);
    }
}
