alexliesenfeld/dgx-spark-printables/spark-atom/images/lenovo-bottom-projection.scad

/*
 * Demo-only pixel projection generated from lenovo.png.
 * Rows are stored top-to-bottom; the module flips them so the photograph's
 * bottom edge maps to Y=0, the physical front of the device.
 * Adjacent equal-shade pixels are merged into rectangles for faster previews.
 */

lenovo_projection_size = 160;
lenovo_projection_rectangles = [
    [0, 0, 160, 7, 0],
    [7, 0, 15, 1, 119],
    [7, 15, 1, 1, 68],
    [7, 16, 1, 1, 51],
    [7, 17, 2, 1, 34],
    [7, 19, 1, 1, 51],
    [7, 20, 115, 1, 119],
    [7, 135, 24, 1, 68],
    [7, 159, 1, 1, 0],
    [8, 0, 1, 1, 136],
    [8, 1, 2, 1, 153],
    [8, 3, 1, 1, 102],
    [8, 4, 16, 1, 85],
    [8, 20, 100, 1, 102],
    [8, 120, 2, 1, 85],
    [8, 122, 1, 1, 102],
    [8, 123, 5, 1, 85],
    [8, 128, 1, 1, 102],
    [8, 129, 27, 1, 85],
    [8, 156, 1, 1, 119],
    [8, 157, 2, 1, 136],
    [8, 159, 1, 1, 68],
    [9, 0, 3, 1, 102],
    [9, 3, 1, 1, 68],
    [9, 4, 14, 1, 51],
    [9, 18, 1, 1, 68],
    [9, 19, 7, 1, 51],
    [9, 26, 105, 1, 68],
    [9, 131, 25, 1, 51],
    [9, 156, 3, 1, 102],
    [9, 159, 1, 1, 51],
    [10, 0, 3, 2, 85],
    [10, 3, 153, 2, 51],
    [10, 156, 3, 2, 85],
    [10, 159, 1, 140, 34],
    [12, 0, 4, 1, 85],
    [12, 4, 1, 1, 68],
    [12, 5, 2, 1, 51],
    [12, 7, 10, 1, 68],
    [12, 17, 1, 1, 51],
    [12, 18, 1, 1, 68],
    [12, 19, 136, 1, 51],
    [12, 155, 4, 1, 85],
    [13, 0, 18, 1, 85],
    [13, 18, 1, 1, 102],
    [13, 19, 140, 1, 85],
    [14, 0, 159, 1, 85],
    [15, 0, 99, 1, 85],
    [15, 99, 41, 1, 68],
    [15, 140, 18, 1, 85],
    [15, 158, 1, 11, 68],
    [16, 0, 155, 6, 85],
    [16, 155, 1, 10, 68],
    [16, 156, 2, 10, 85],
    [22, 0, 135, 1, 85],
    [22, 135, 5, 1, 68],
    [22, 140, 15, 1, 85],
    [23, 0, 33, 1, 85],
    [23, 33, 40, 1, 102],
    [23, 73, 62, 1, 85],
    [23, 135, 6, 1, 68],
    [23, 141, 14, 1, 85],
    [24, 0, 25, 1, 85],
    [24, 25, 85, 1, 102],
    [24, 110, 25, 1, 85],
    [24, 135, 10, 1, 68],
    [24, 145, 10, 1, 85],
    [25, 0, 23, 1, 85],
    [25, 23, 105, 1, 102],
    [25, 128, 6, 1, 85],
    [25, 134, 9, 1, 68],
    [25, 143, 12, 1, 85],
    [26, 0, 21, 1, 85],
    [26, 21, 8, 1, 102],
    [26, 29, 97, 1, 119],
    [26, 126, 4, 1, 102],
    [26, 130, 4, 1, 85],
    [26, 134, 10, 1, 68],
    [26, 144, 7, 1, 85],
    [26, 151, 3, 2, 68],
    [26, 154, 1, 18, 85],
    [26, 155, 4, 14, 68],
    [27, 0, 18, 1, 85],
    [27, 18, 9, 1, 102],
    [27, 27, 4, 1, 119],
    [27, 31, 83, 1, 136],
    [27, 114, 15, 1, 119],
    [27, 129, 3, 1, 102],
    [27, 132, 4, 1, 85],
    [27, 136, 9, 1, 68],
    [27, 145, 6, 1, 85],
    [28, 0, 17, 1, 85],
    [28, 17, 9, 1, 102],
    [28, 26, 4, 1, 119],
    [28, 30, 96, 1, 136],
    [28, 126, 4, 1, 119],
    [28, 130, 3, 1, 102],
    [28, 133, 3, 3, 85],
    [28, 136, 11, 1, 68],
    [28, 147, 3, 1, 85],
    [28, 150, 4, 1, 68],
    [29, 0, 16, 1, 85],
    [29, 16, 9, 1, 102],
    [29, 25, 4, 1, 119],
    [29, 29, 97, 1, 136],
    [29, 126, 5, 1, 119],
    [29, 131, 2, 1, 102],
    [29, 136, 18, 3, 68],
    [30, 0, 15, 2, 85],
    [30, 15, 10, 2, 102],
    [30, 25, 5, 1, 119],
    [30, 30, 3, 1, 102],
    [30, 33, 95, 1, 85],
    [30, 128, 5, 1, 102],
    [31, 25, 1, 1, 119],
    [31, 26, 2, 1, 102],
    [31, 28, 1, 1, 85],
    [31, 29, 2, 1, 68],
    [31, 31, 8, 1, 51],
    [31, 39, 88, 1, 34],
    [31, 127, 2, 1, 51],
    [31, 129, 2, 1, 68],
    [31, 131, 5, 1, 85],
    [32, 0, 14, 1, 85],
    [32, 14, 12, 1, 102],
    [32, 26, 1, 1, 85],
    [32, 27, 2, 1, 51],
    [32, 29, 102, 1, 34],
    [32, 131, 1, 1, 51],
    [32, 132, 1, 1, 68],
    [32, 133, 2, 1, 85],
    [32, 135, 4, 1, 68],
    [32, 139, 4, 1, 51],
    [32, 143, 11, 1, 68],
    [33, 0, 13, 3, 85],
    [33, 13, 11, 1, 102],
    [33, 24, 1, 1, 85],
    [33, 25, 1, 1, 68],
    [33, 26, 1, 1, 51],
    [33, 27, 106, 1, 34],
    [33, 133, 1, 1, 51],
    [33, 134, 4, 1, 68],
    [33, 138, 6, 1, 51],
    [33, 144, 10, 1, 68],
    [34, 13, 10, 1, 102],
    [34, 23, 1, 1, 85],
    [34, 24, 1, 1, 51],
    [34, 25, 110, 1, 34],
    [34, 135, 2, 1, 68],
    [34, 137, 8, 1, 51],
    [34, 145, 9, 2, 68],
    [35, 13, 3, 1, 102],
    [35, 16, 1, 1, 119],
    [35, 17, 4, 2, 102],
    [35, 21, 2, 1, 85],
    [35, 23, 1, 1, 51],
    [35, 24, 112, 1, 34],
    [35, 136, 1, 1, 68],
    [35, 137, 2, 1, 51],
    [35, 139, 2, 1, 34],
    [35, 141, 4, 1, 51],
    [36, 0, 12, 2, 85],
    [36, 12, 3, 2, 102],
    [36, 15, 2, 2, 119],
    [36, 21, 1, 1, 85],
    [36, 22, 1, 1, 51],
    [36, 23, 114, 1, 34],
    [36, 137, 1, 1, 68],
    [36, 138, 1, 1, 51],
    [36, 139, 4, 1, 34],
    [36, 143, 3, 1, 51],
    [36, 146, 8, 1, 68],
    [37, 17, 3, 4, 102],
    [37, 20, 1, 2, 85],
    [37, 21, 1, 1, 68],
    [37, 22, 115, 1, 34],
    [37, 137, 2, 1, 51],
    [37, 139, 5, 2, 34],
    [37, 144, 3, 2, 51],
    [37, 147, 7, 3, 68],
    [38, 0, 11, 85, 85],
    [38, 11, 3, 2, 102],
    [38, 14, 3, 2, 119],
    [38, 21, 1, 1, 51],
    [38, 22, 116, 1, 34],
    [38, 138, 1, 1, 51],
    [39, 20, 1, 2, 68],
    [39, 21, 116, 1, 34],
    [39, 137, 1, 1, 17],
    [39, 138, 1, 1, 34],
    [39, 139, 1, 29, 51],
    [39, 140, 1, 1, 17],
    [39, 141, 4, 1, 34],
    [39, 145, 2, 1, 51],
    [40, 11, 2, 13, 102],
    [40, 13, 4, 9, 119],
    [40, 21, 118, 1, 34],
    [40, 140, 1, 28, 34],
    [40, 141, 1, 1, 17],
    [40, 142, 3, 1, 34],
    [40, 145, 3, 9, 51],
    [40, 148, 6, 4, 68],
    [40, 155, 2, 4, 68],
    [40, 157, 1, 18, 85],
    [40, 158, 1, 18, 68],
    [41, 17, 2, 8, 102],
    [41, 19, 1, 73, 85],
    [41, 20, 1, 1, 51],
    [41, 21, 117, 1, 34],
    [41, 138, 1, 2, 17],
    [41, 141, 2, 69, 17],
    [41, 143, 2, 8, 34],
    [42, 20, 118, 1, 34],
    [43, 20, 119, 15, 34],
    [44, 148, 9, 14, 68],
    [49, 13, 3, 4, 119],
    [49, 16, 3, 5, 102],
    [49, 143, 3, 9, 34],
    [49, 146, 2, 9, 51],
    [53, 11, 3, 29, 102],
    [53, 14, 2, 1, 119],
    [54, 14, 3, 28, 119],
    [54, 17, 2, 37, 102],
    [58, 20, 118, 4, 34],
    [58, 138, 1, 4, 17],
    [58, 143, 2, 5, 34],
    [58, 145, 3, 5, 51],
    [58, 148, 11, 61, 68],
    [62, 20, 119, 5, 34],
    [63, 143, 3, 23, 34],
    [63, 146, 2, 23, 51],
    [67, 20, 118, 28, 34],
    [67, 138, 1, 28, 17],
    [68, 139, 2, 18, 34],
    [82, 11, 2, 6, 102],
    [82, 13, 4, 6, 119],
    [86, 139, 1, 34, 51],
    [86, 140, 1, 30, 34],
    [86, 143, 2, 24, 34],
    [86, 145, 3, 33, 51],
    [88, 11, 3, 3, 102],
    [88, 14, 3, 3, 119],
    [91, 11, 2, 4, 102],
    [91, 13, 3, 4, 119],
    [91, 16, 3, 4, 102],
    [95, 11, 3, 5, 102],
    [95, 14, 3, 5, 119],
    [95, 17, 2, 5, 102],
    [95, 20, 119, 6, 34],
    [100, 11, 2, 5, 102],
    [100, 13, 5, 4, 119],
    [100, 18, 1, 4, 102],
    [101, 20, 118, 16, 34],
    [101, 138, 1, 17, 17],
    [104, 13, 4, 1, 119],
    [104, 17, 2, 14, 102],
    [105, 11, 3, 6, 102],
    [105, 14, 3, 6, 119],
    [110, 141, 1, 6, 17],
    [110, 142, 3, 6, 34],
    [111, 11, 2, 2, 102],
    [111, 13, 4, 2, 119],
    [113, 11, 3, 6, 102],
    [113, 14, 3, 5, 119],
    [114, 19, 1, 1, 68],
    [115, 19, 1, 5, 85],
    [116, 140, 5, 3, 34],
    [117, 20, 1, 3, 51],
    [117, 21, 117, 1, 34],
    [118, 14, 2, 1, 119],
    [118, 16, 3, 1, 102],
    [118, 21, 118, 3, 34],
    [119, 11, 8, 1, 102],
    [119, 140, 4, 1, 34],
    [119, 144, 4, 1, 51],
    [119, 148, 8, 1, 68],
    [119, 156, 2, 25, 85],
    [119, 158, 1, 31, 68],
    [120, 11, 9, 3, 102],
    [120, 20, 1, 1, 68],
    [120, 139, 1, 1, 68],
    [120, 140, 3, 1, 34],
    [120, 143, 4, 1, 51],
    [120, 147, 9, 1, 68],
    [121, 20, 1, 2, 85],
    [121, 21, 116, 1, 34],
    [121, 137, 1, 1, 17],
    [121, 138, 2, 1, 51],
    [121, 140, 1, 1, 34],
    [121, 141, 6, 1, 51],
    [121, 147, 7, 1, 68],
    [121, 154, 1, 15, 85],
    [121, 155, 1, 23, 68],
    [122, 21, 1, 1, 68],
    [122, 22, 116, 1, 34],
    [122, 138, 1, 2, 68],
    [122, 139, 7, 2, 51],
    [122, 146, 8, 2, 68],
    [123, 0, 12, 2, 85],
    [123, 12, 9, 2, 102],
    [123, 21, 1, 2, 85],
    [123, 22, 1, 1, 51],
    [123, 23, 114, 1, 34],
    [123, 137, 1, 1, 51],
    [124, 22, 1, 1, 68],
    [124, 23, 113, 1, 34],
    [124, 136, 1, 1, 51],
    [124, 137, 3, 1, 68],
    [124, 140, 4, 1, 51],
    [124, 144, 10, 1, 68],
    [125, 0, 13, 2, 85],
    [125, 13, 8, 1, 102],
    [125, 21, 2, 1, 85],
    [125, 23, 1, 1, 68],
    [125, 24, 112, 1, 34],
    [125, 136, 18, 1, 68],
    [126, 13, 10, 1, 102],
    [126, 23, 1, 1, 85],
    [126, 24, 1, 1, 68],
    [126, 25, 109, 1, 34],
    [126, 134, 1, 1, 51],
    [126, 135, 1, 1, 68],
    [126, 136, 1, 1, 85],
    [126, 137, 17, 1, 68],
    [127, 0, 14, 2, 85],
    [127, 14, 11, 1, 102],
    [127, 25, 1, 1, 85],
    [127, 26, 1, 1, 51],
    [127, 27, 105, 1, 34],
    [127, 132, 1, 1, 51],
    [127, 133, 1, 1, 68],
    [127, 134, 5, 1, 85],
    [127, 139, 15, 2, 68],
    [128, 14, 10, 1, 102],
    [128, 24, 2, 1, 119],
    [128, 26, 1, 1, 102],
    [128, 27, 1, 1, 85],
    [128, 28, 1, 1, 68],
    [128, 29, 2, 1, 51],
    [128, 31, 99, 1, 34],
    [128, 130, 1, 1, 51],
    [128, 131, 1, 1, 68],
    [128, 132, 1, 1, 85],
    [128, 133, 3, 1, 102],
    [128, 136, 3, 1, 85],
    [129, 0, 15, 1, 85],
    [129, 15, 8, 1, 102],
    [129, 23, 3, 2, 119],
    [129, 26, 2, 3, 136],
    [129, 28, 1, 1, 119],
    [129, 29, 1, 1, 102],
    [129, 30, 1, 1, 85],
    [129, 31, 3, 1, 68],
    [129, 34, 93, 1, 51],
    [129, 127, 2, 1, 68],
    [129, 129, 1, 1, 85],
    [129, 130, 1, 1, 102],
    [129, 131, 3, 1, 119],
    [129, 134, 2, 3, 102],
    [129, 136, 4, 3, 85],
    [129, 140, 14, 3, 68],
    [130, 0, 16, 1, 85],
    [130, 16, 7, 1, 102],
    [130, 28, 4, 1, 153],
    [130, 32, 83, 1, 136],
    [130, 115, 5, 1, 119],
    [130, 120, 8, 1, 136],
    [130, 128, 3, 2, 153],
    [130, 131, 2, 1, 136],
    [130, 133, 1, 1, 119],
    [131, 0, 17, 1, 85],
    [131, 17, 7, 1, 102],
    [131, 24, 2, 1, 119],
    [131, 28, 2, 1, 153],
    [131, 30, 4, 1, 170],
    [131, 34, 91, 1, 187],
    [131, 125, 3, 1, 170],
    [131, 131, 1, 1, 136],
    [131, 132, 2, 1, 119],
    [132, 0, 18, 1, 85],
    [132, 18, 7, 1, 102],
    [132, 25, 2, 1, 119],
    [132, 27, 2, 1, 136],
    [132, 29, 3, 1, 153],
    [132, 32, 95, 1, 170],
    [132, 127, 3, 1, 153],
    [132, 130, 1, 1, 136],
    [132, 131, 3, 1, 119],
    [132, 134, 1, 1, 102],
    [132, 135, 4, 1, 85],
    [132, 139, 15, 3, 68],
    [133, 0, 20, 1, 85],
    [133, 20, 7, 1, 102],
    [133, 27, 2, 1, 119],
    [133, 29, 3, 1, 136],
    [133, 32, 95, 1, 153],
    [133, 127, 3, 1, 136],
    [133, 130, 2, 1, 119],
    [133, 132, 2, 1, 102],
    [133, 134, 5, 1, 85],
    [134, 0, 22, 1, 85],
    [134, 22, 7, 1, 102],
    [134, 29, 7, 1, 119],
    [134, 36, 87, 1, 136],
    [134, 123, 6, 1, 119],
    [134, 129, 3, 1, 102],
    [134, 132, 7, 1, 85],
    [135, 0, 25, 1, 85],
    [135, 25, 105, 1, 102],
    [135, 130, 11, 1, 85],
    [135, 141, 13, 1, 68],
    [136, 0, 28, 1, 85],
    [136, 28, 99, 1, 102],
    [136, 127, 28, 1, 85],
    [137, 0, 10, 1, 85],
    [137, 10, 14, 1, 68],
    [137, 24, 108, 1, 85],
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
