alexliesenfeld/dgx-spark-printables/spark-rack-10/load_test/loadtest_gputemps.png

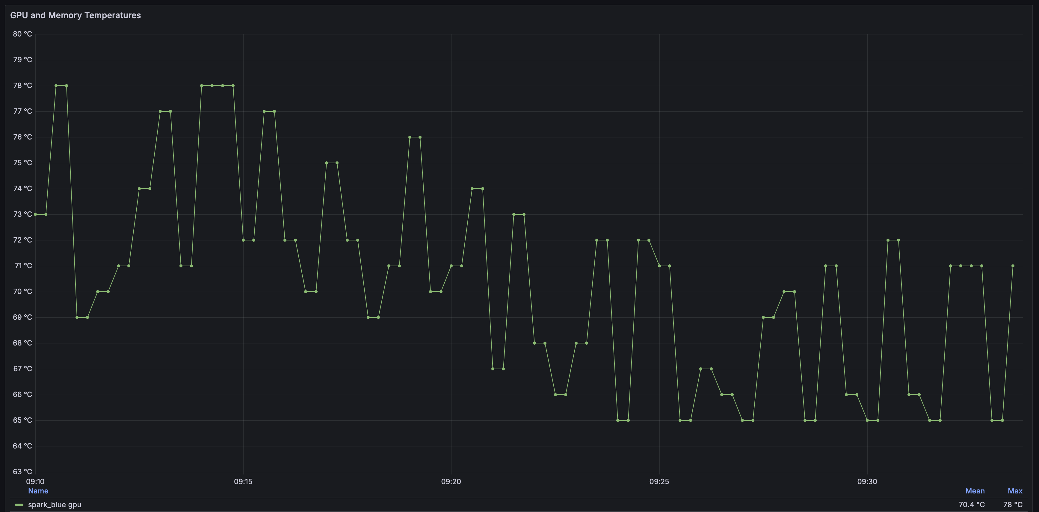
spark-rack-10/load_test/loadtest_gputemps.png
