alexliesenfeld/dgx-spark-printables/spark-atom/shop-img/IMG_5973.JPG

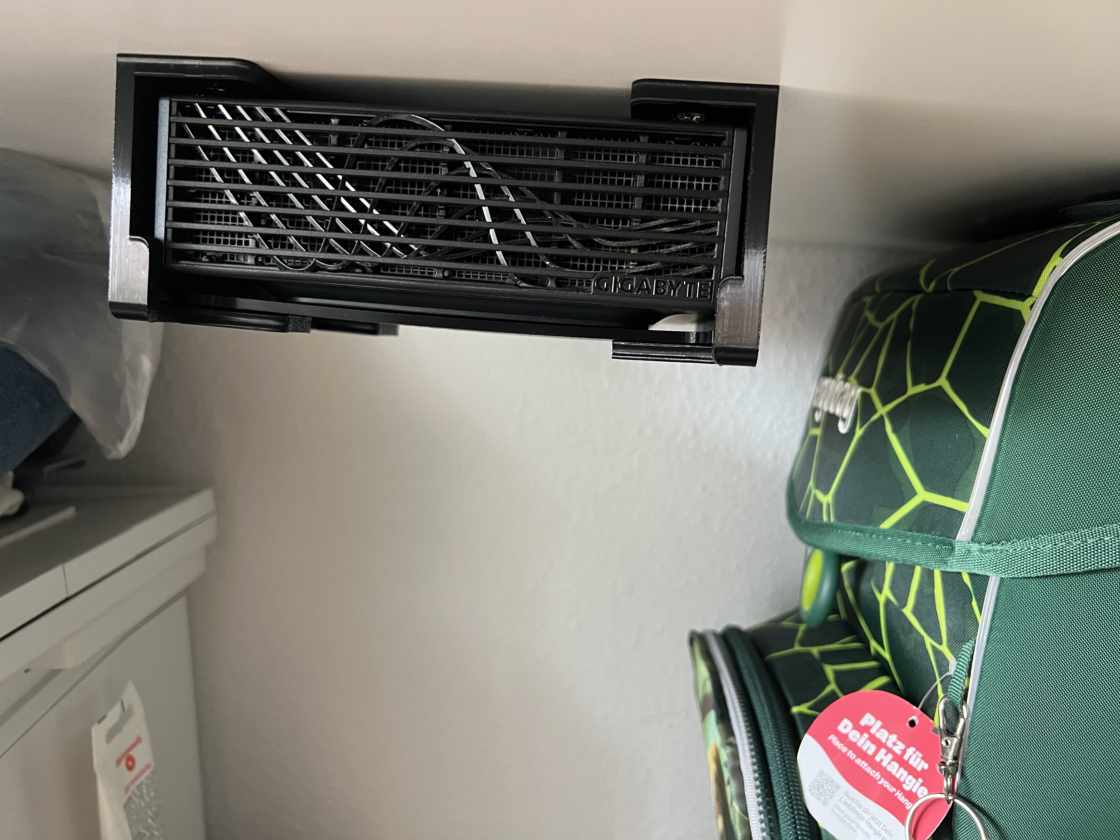
spark-atom/shop-img/IMG_5973.JPG
