alexliesenfeld/dgx-spark-printables/spark-atom/shop-img/untitled folder/IMG_5971.JPG

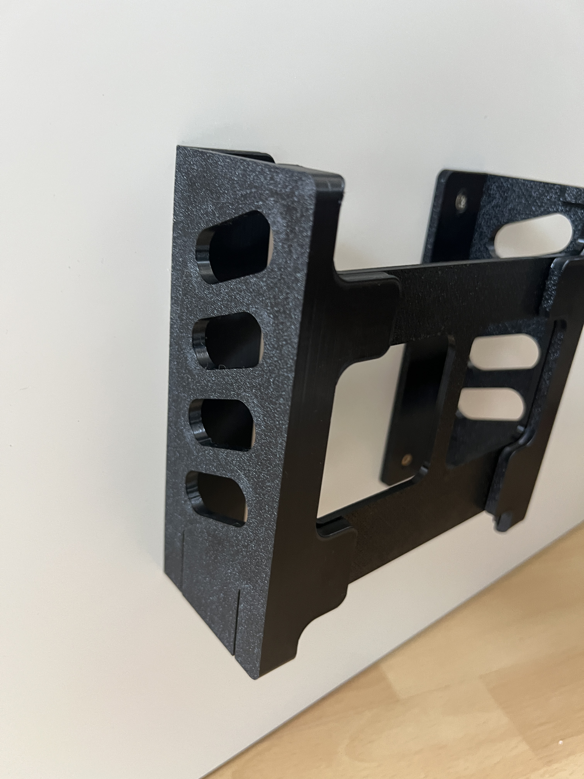
spark-atom/shop-img/untitled folder/IMG_5971.JPG
